Takazudo/zudo-bus/footprints/3dshapes/CAP-SMD_BD6.3-L6.6-W6.6-LS7.3-FD.step

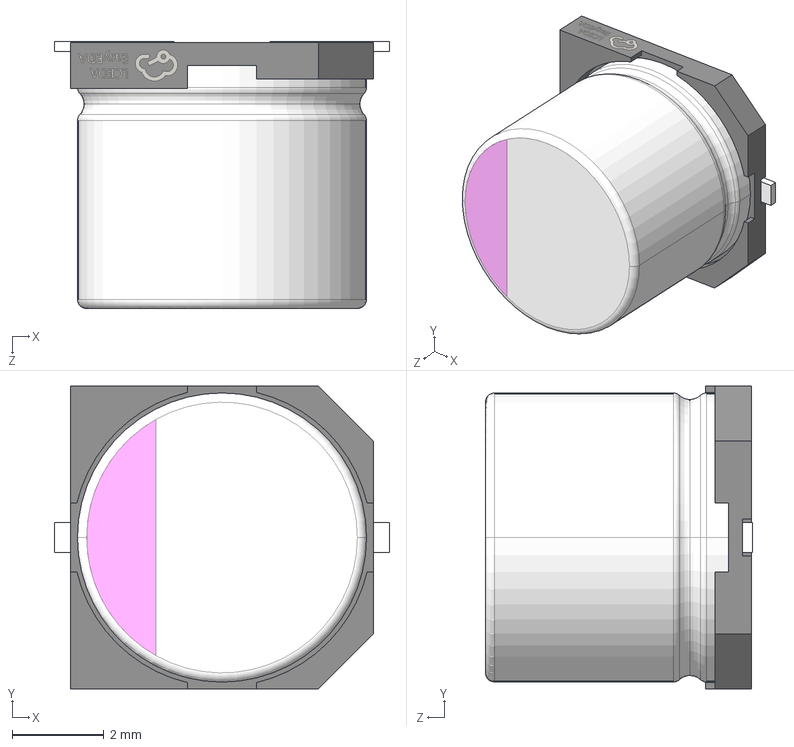
[picture p15: CAD file, 2026-02-04]
footprints/3dshapes/CAP-SMD_BD6.3-L6.6-W6.6-LS7.3-FD.step
7.30 x 6.60 x 5.82 mm
