Takazudo/zudo-bus/footprints/3dshapes/F1206_L3.2-W1.7-H0.6.step

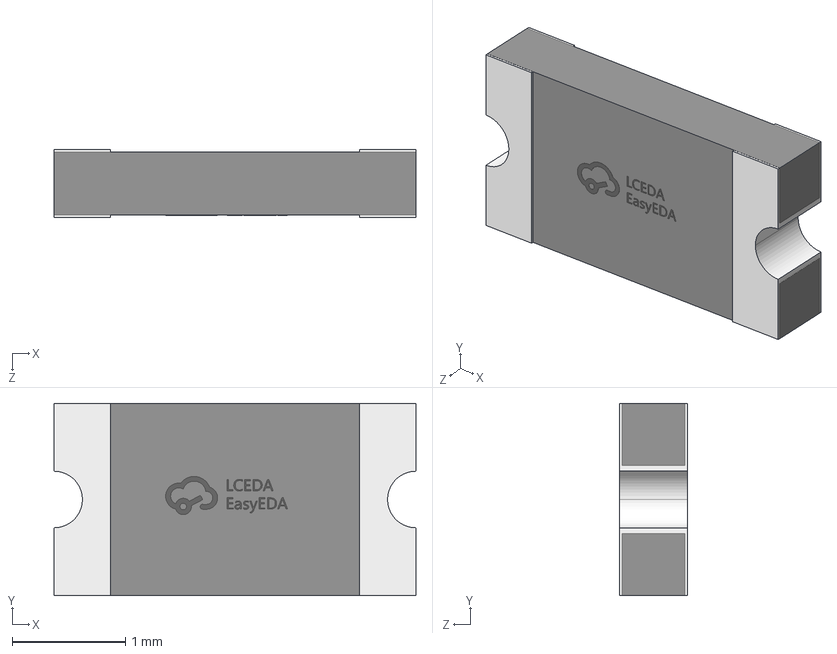
[picture p16: CAD file, 2026-02-04]
footprints/3dshapes/F1206_L3.2-W1.7-H0.6.step
3.20 x 1.70 x 0.6 mm
