Takazudo/zudo-bus/footprints/3dshapes/QFN-20_L3.0-W3.0-P0.40-BL-EP1.7.step

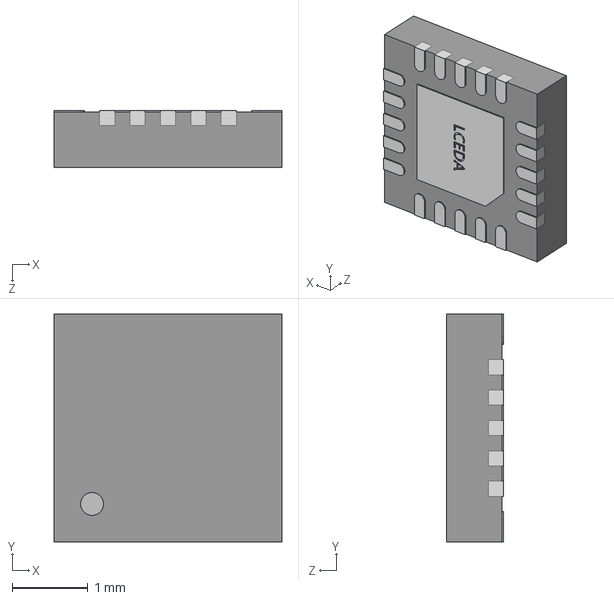
[picture p17: CAD file, 2026-02-04]
footprints/3dshapes/QFN-20_L3.0-W3.0-P0.40-BL-EP1.7.step
3.00 x 3.00 x 0.75 mm
