Takazudo/zudo-bus/footprints/3dshapes/F1812_L4.5-W3.2-H1.0.step

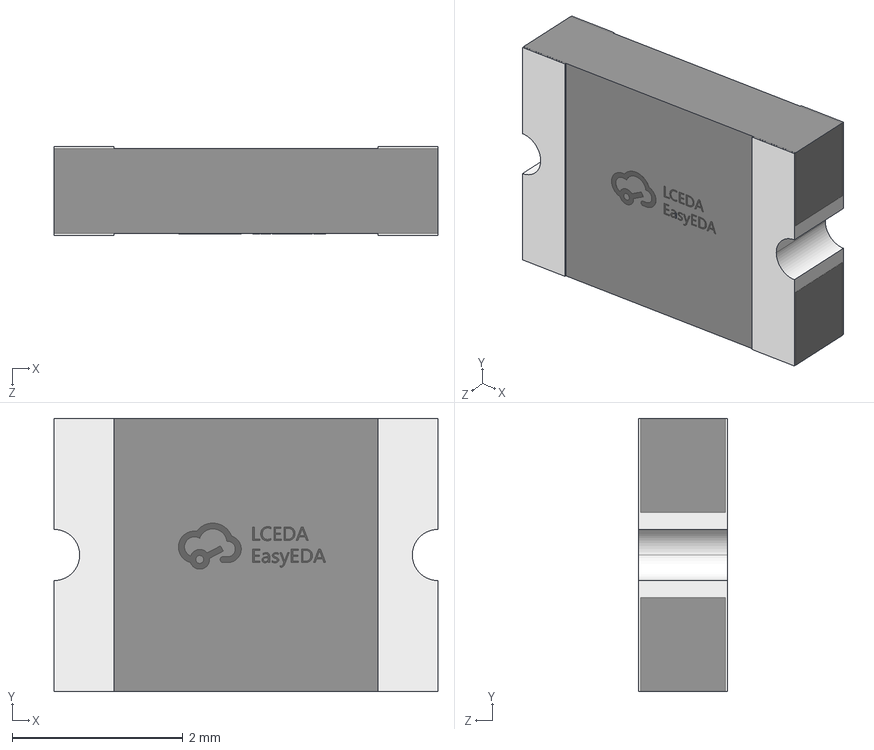
[picture p18: CAD file, 2026-02-04]
footprints/3dshapes/F1812_L4.5-W3.2-H1.0.step
4.50 x 3.20 x 1.04 mm
