Takazudo/zudo-bus/footprints/3dshapes/CAP-SMD_BD10.0-L10.3-W10.3-H10.2.step

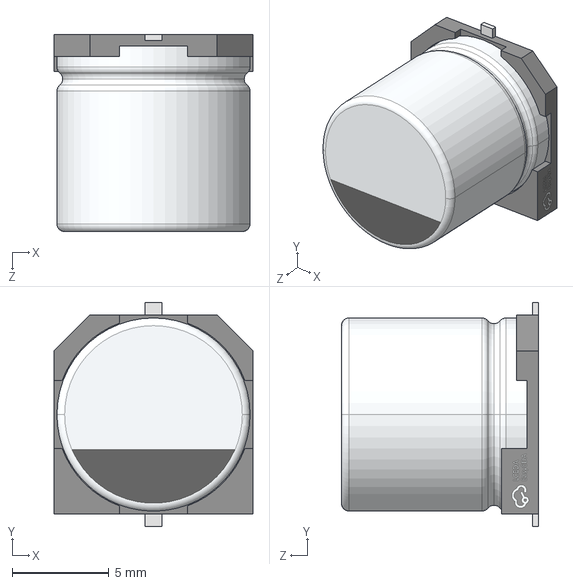
[picture p19: CAD file, 2026-02-04]
footprints/3dshapes/CAP-SMD_BD10.0-L10.3-W10.3-H10.2.step
10.3 x 11.6 x 10.2 mm
