Takazudo/zudo-bus/footprints/3dshapes/DC-IN-TH_DC550250-0366-2H.step

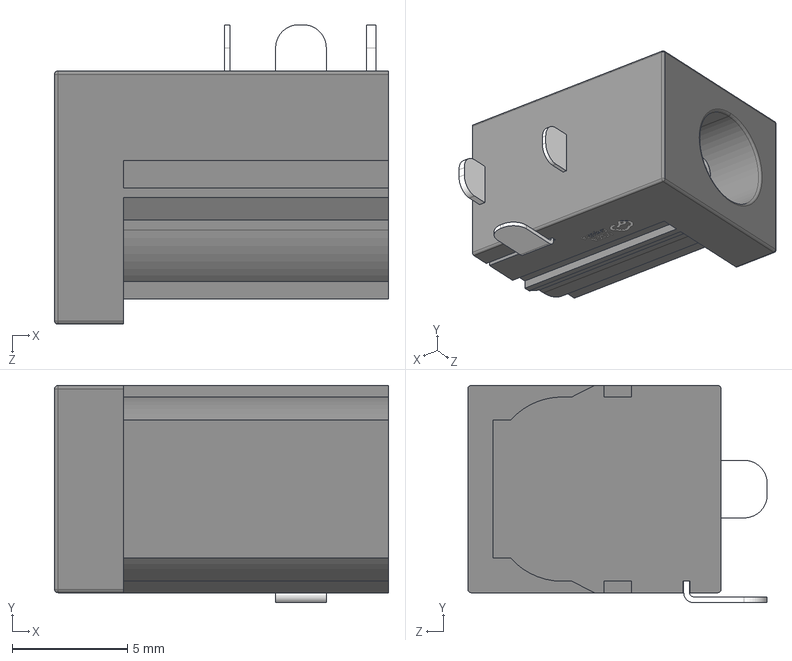
[picture p20: CAD file, 2026-02-04]
footprints/3dshapes/DC-IN-TH_DC550250-0366-2H.step
14.5 x 9.43 x 13.0 mm
