Takazudo/zudo-bus/footprints/3dshapes/CAP-SMD_BD6.3-L6.6-W6.6-FD.step

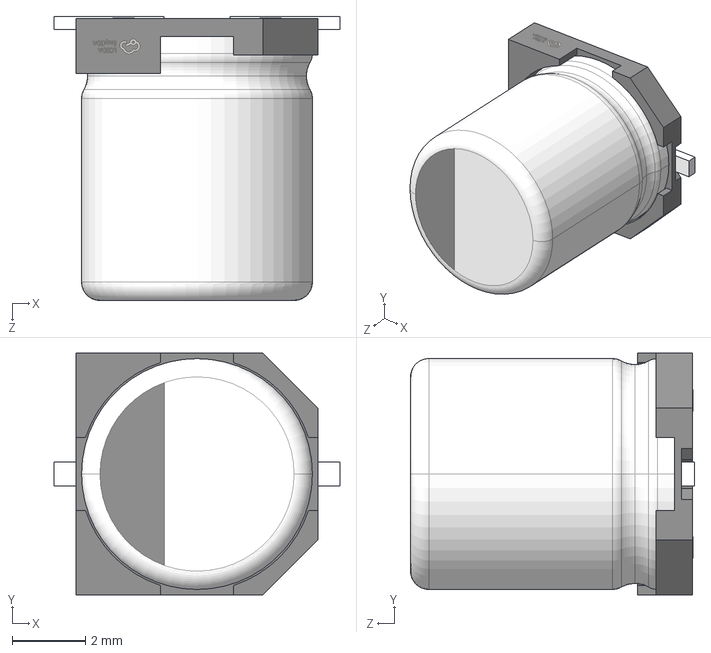
[picture p21: CAD file, 2026-02-04]
footprints/3dshapes/CAP-SMD_BD6.3-L6.6-W6.6-FD.step
7.80 x 6.60 x 7.75 mm
