Takazudo/zudo-bus/footprints/3dshapes/HDR-TH_16P-P2.54-M-WI-2X8P.step

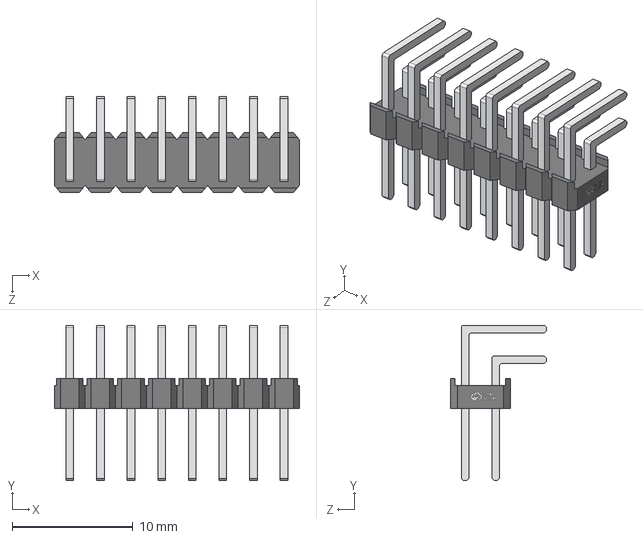
[picture p22: CAD file, 2026-02-04]
footprints/3dshapes/HDR-TH_16P-P2.54-M-WI-2X8P.step
20.3 x 12.9 x 8.00 mm
