Takazudo/zudo-bus/footprints/3dshapes/HDR-M-2.54_1x3.step

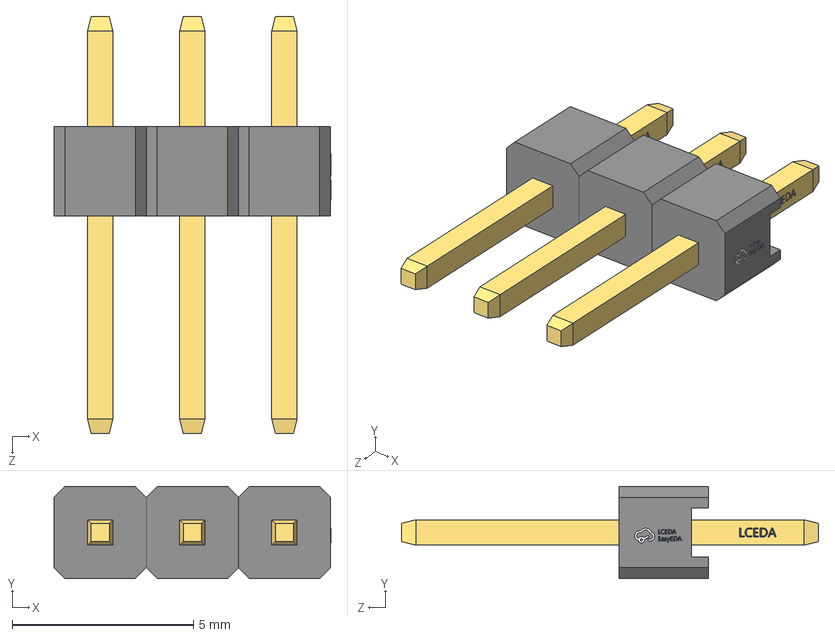
[picture p23: CAD file, 2026-02-04]
footprints/3dshapes/HDR-M-2.54_1x3.step
7.63 x 2.54 x 11.5 mm
