Takazudo/zudo-bus/footprints/3dshapes/R0805_L2.0-W1.3-H0.6.step

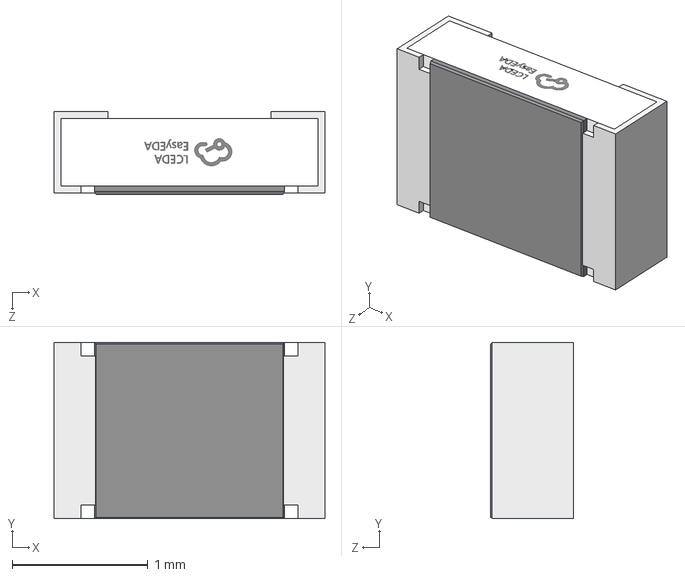
[picture p24: CAD file, 2026-02-04]
footprints/3dshapes/R0805_L2.0-W1.3-H0.6.step
2.00 x 1.30 x 0.61 mm
