Takazudo/zudo-bus/footprints/3dshapes/HDR-SMD_8P-P2.54-V-M-LS4.8_R2.step

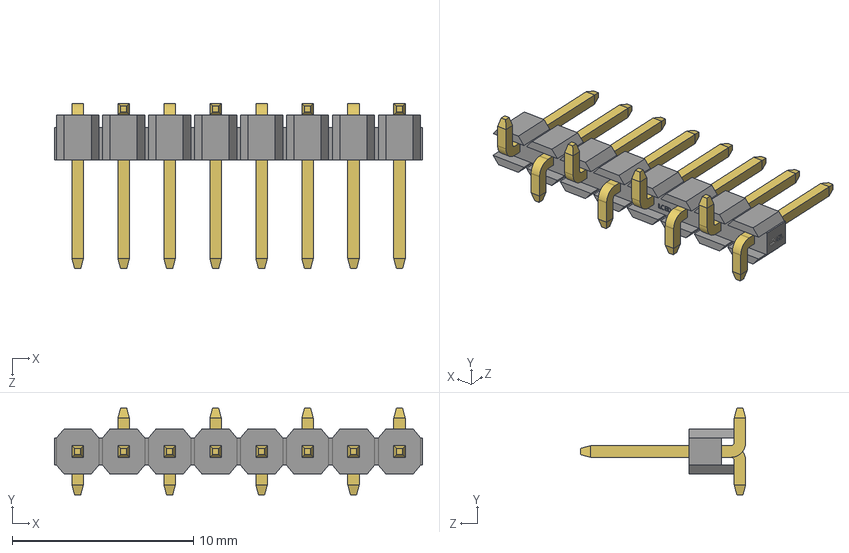
[picture p25: CAD file, 2026-02-04]
footprints/3dshapes/HDR-SMD_8P-P2.54-V-M-LS4.8_R2.step
20.3 x 4.80 x 9.14 mm
