Takazudo/zudo-bus/footprints/3dshapes/DO-214AC_L4.3-W2.7-LS5.0-RD.step

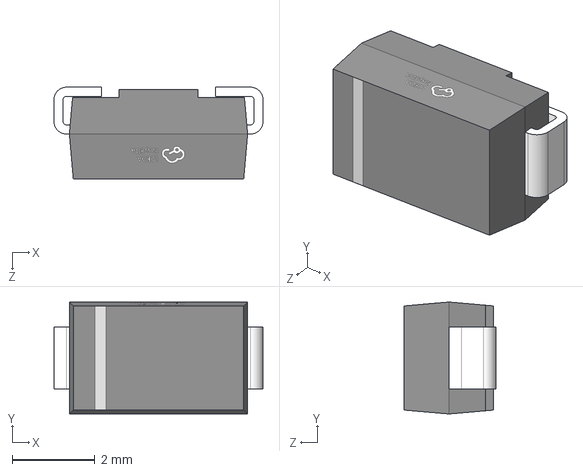
[picture p26: CAD file, 2026-02-04]
footprints/3dshapes/DO-214AC_L4.3-W2.7-LS5.0-RD.step
5.04 x 2.70 x 2.21 mm
