Takazudo/zudo-bus/footprints/3dshapes/TO-263-3_L10.2-W8.7-H4.5-LS14.4-P2.54.step

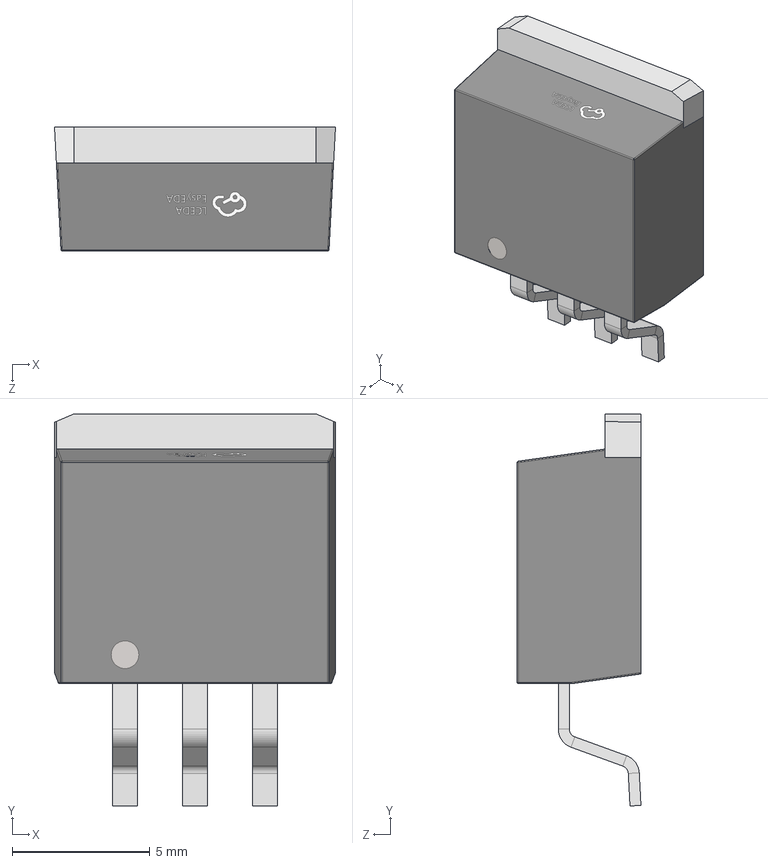
[picture p27: CAD file, 2026-02-04]
footprints/3dshapes/TO-263-3_L10.2-W8.7-H4.5-LS14.4-P2.54.step
10.2 x 14.2 x 4.50 mm
