Takazudo/zudo-bus/footprints/3dshapes/HDR-SMD_36P-P2.00-V-M_XBK_R2.step

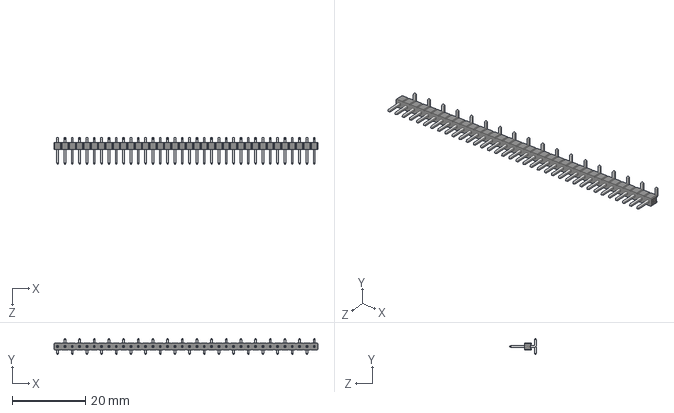
[picture p28: CAD file, 2026-02-04]
footprints/3dshapes/HDR-SMD_36P-P2.00-V-M_XBK_R2.step
72.0 x 4.40 x 7.25 mm
