Takazudo/zudo-bus/footprints/3dshapes/C0603_L1.6-W0.8-H0.8.step

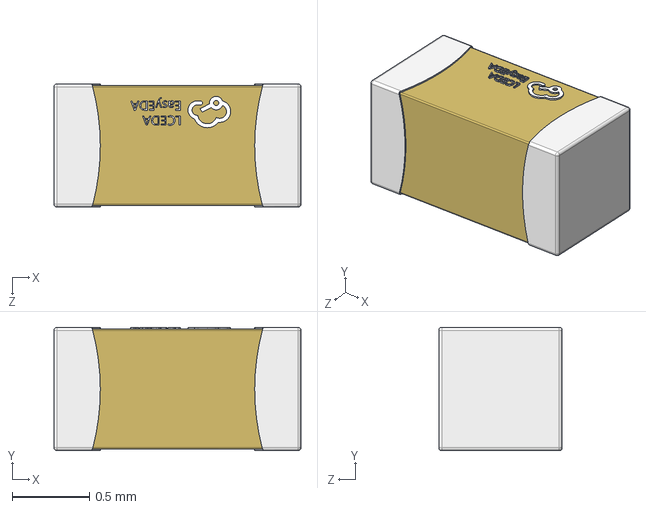
[picture p29: CAD file, 2026-02-04]
footprints/3dshapes/C0603_L1.6-W0.8-H0.8.step
1.60 x 0.8 x 0.8 mm
