Takazudo/zudo-bus/footprints/3dshapes/C1206_L3.2-W1.6-H1.3.step

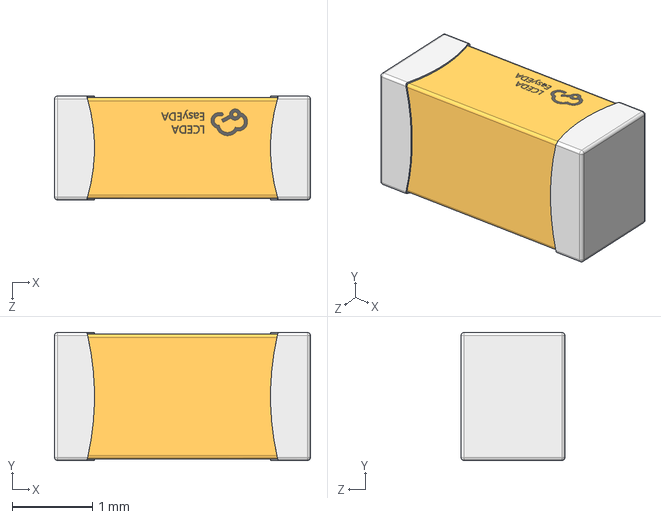
[picture p30: CAD file, 2026-02-04]
footprints/3dshapes/C1206_L3.2-W1.6-H1.3.step
3.20 x 1.60 x 1.30 mm
