Takazudo/zudo-bus/footprints/3dshapes/SMA_L4.4-W2.8-LS5.4-RD.step

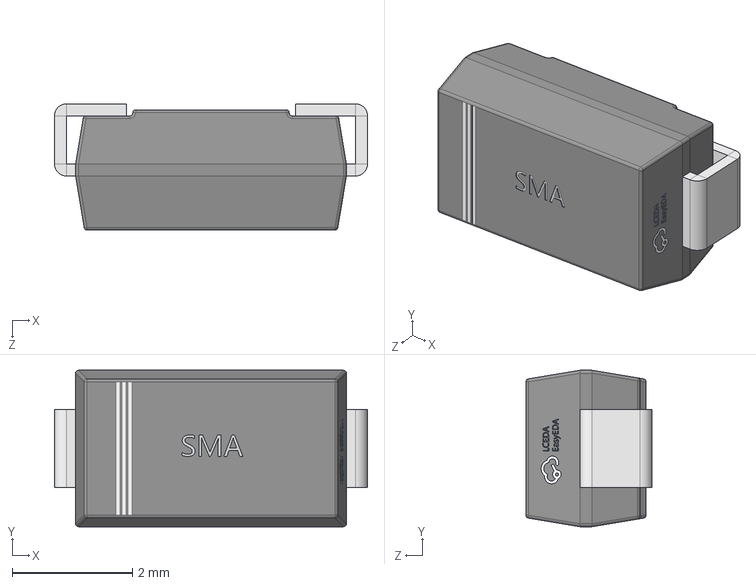
[picture p31: CAD file, 2026-02-04]
footprints/3dshapes/SMA_L4.4-W2.8-LS5.4-RD.step
5.20 x 2.60 x 2.10 mm
