Takazudo/zudo-bus/footprints/3dshapes/FUSE-SMD_L10.1-W3.1-H3.1.step

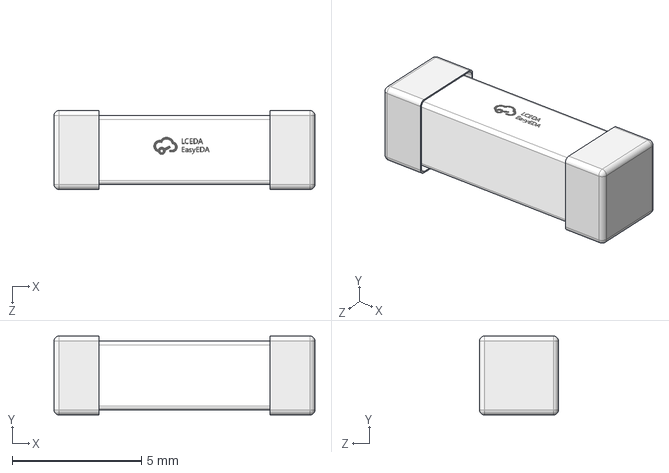
[picture p33: CAD file, 2026-02-04]
footprints/3dshapes/FUSE-SMD_L10.1-W3.1-H3.1.step
10.1 x 3.05 x 3.05 mm
