Takazudo/zudo-bus/footprints/3dshapes/SOD-123FL_L2.8-W1.8-LS3.7-RD.step

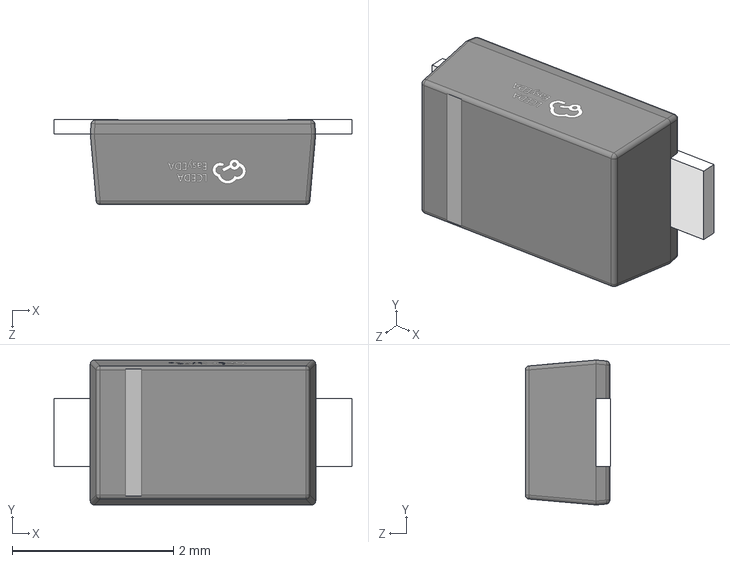
[picture p34: CAD file, 2026-02-04]
footprints/3dshapes/SOD-123FL_L2.8-W1.8-LS3.7-RD.step
3.70 x 1.80 x 1.06 mm
