Takazudo/zudo-bus/footprints/3dshapes/LED0805-RD.step

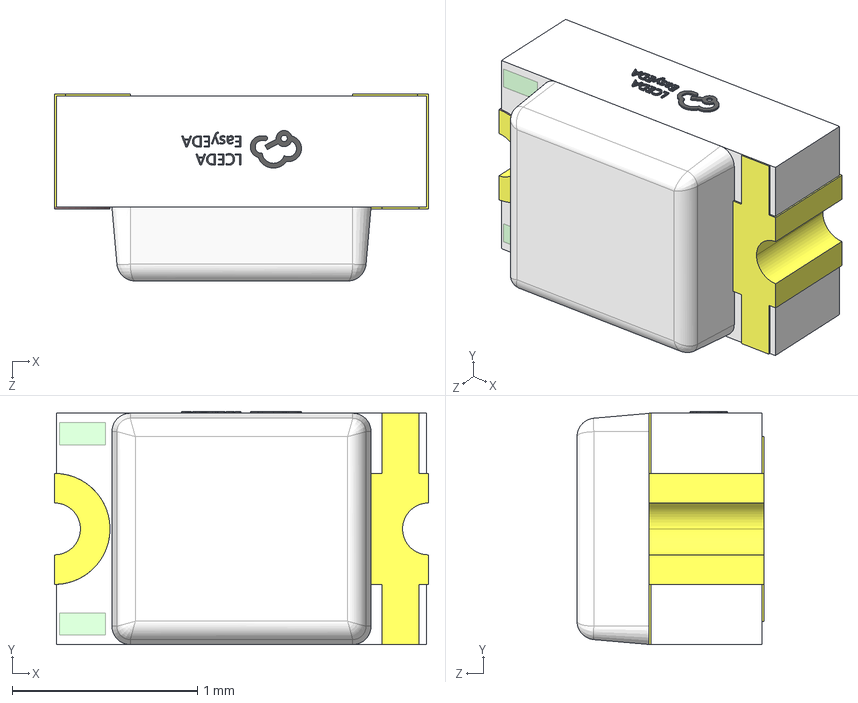
[picture p35: CAD file, 2026-02-04]
footprints/3dshapes/LED0805-RD.step
2.02 x 1.26 x 1.01 mm
