Takazudo/zudo-bus/footprints/3dshapes/HDR-TH_3P-P2.54-M-LI-1X3P.step

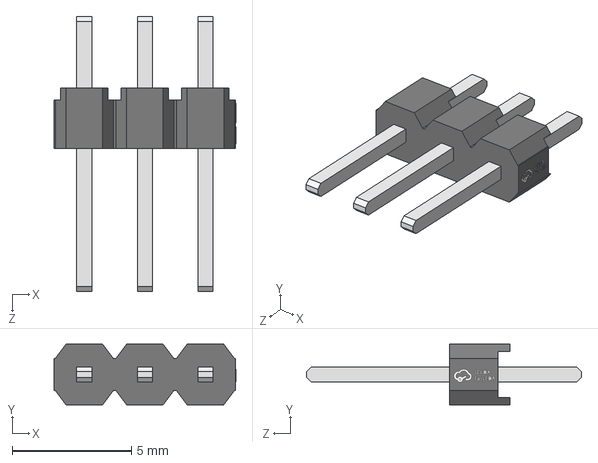
[picture p36: CAD file, 2026-02-04]
footprints/3dshapes/HDR-TH_3P-P2.54-M-LI-1X3P.step
7.63 x 2.54 x 11.5 mm
