Takazudo/zudo-bus/footprints/3dshapes/R0603.step

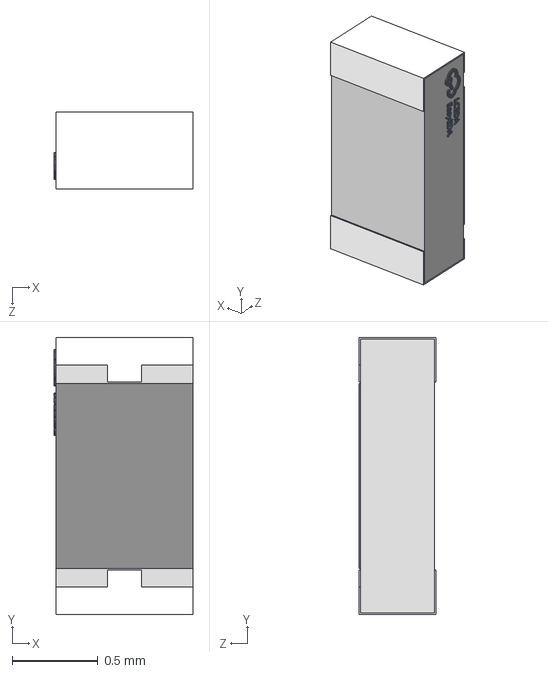
[picture p37: CAD file, 2026-02-04]
footprints/3dshapes/R0603.step
0.81 x 1.62 x 0.45 mm
