Takazudo/zudo-bus/footprints/3dshapes/CAP-SMD_BD18.0-L19.0-W19.0-LS20.4-FD.step

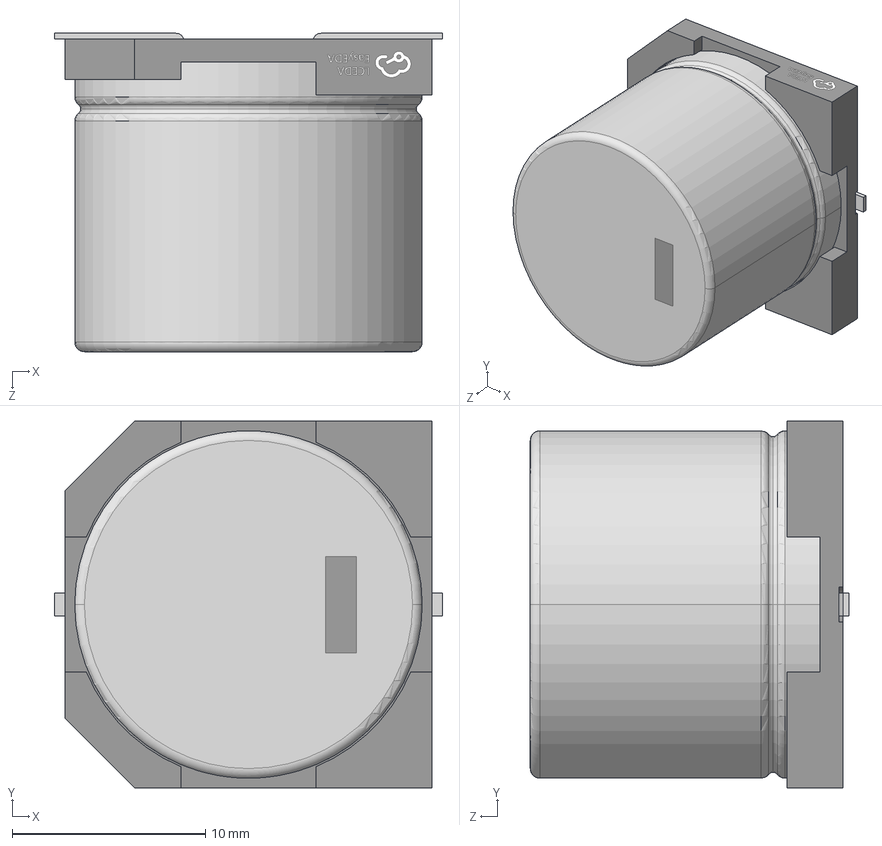
[picture p38: CAD file, 2026-02-04]
footprints/3dshapes/CAP-SMD_BD18.0-L19.0-W19.0-LS20.4-FD.step
20.1 x 19.0 x 16.5 mm
