Takazudo/zudo-bus/footprints/3dshapes/TO-263-2_L10.2-W8.7-H4.5-LS15.2-P2.54.step

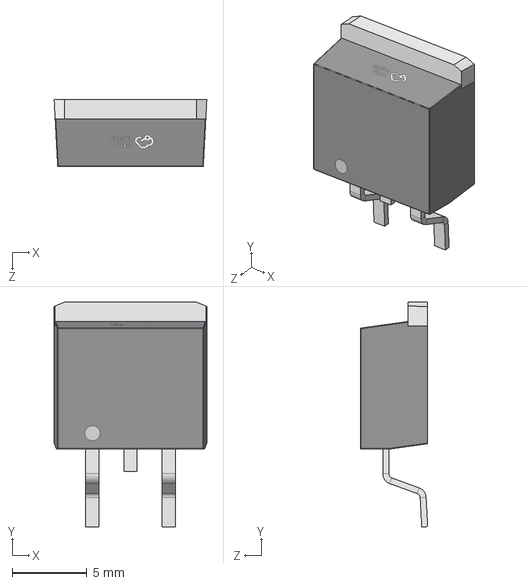
[picture p39: CAD file, 2026-02-04]
footprints/3dshapes/TO-263-2_L10.2-W8.7-H4.5-LS15.2-P2.54.step
10.2 x 15.0 x 4.50 mm
