Takazudo/zudo-bus/footprints/3dshapes/LED0603-R-RD_WHITE.step

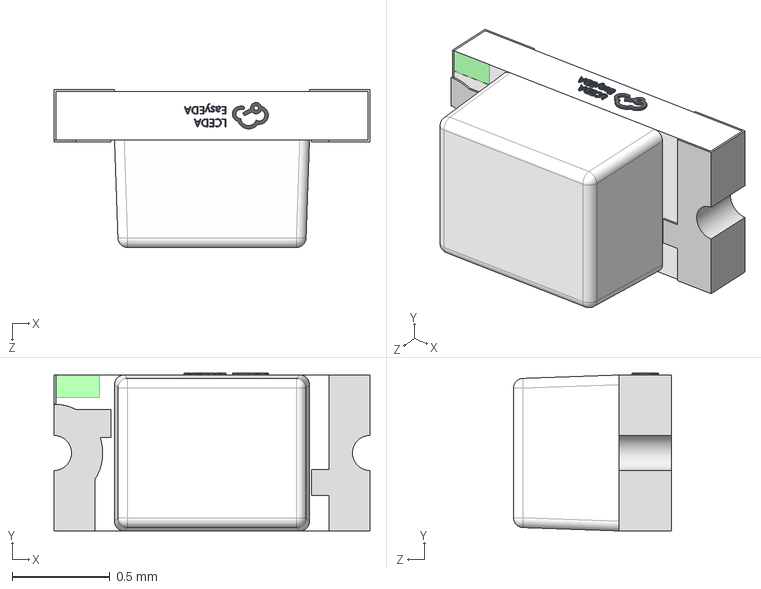
[picture p40: CAD file, 2026-02-04]
footprints/3dshapes/LED0603-R-RD_WHITE.step
1.62 x 0.81 x 0.81 mm
