Takazudo/zudo-bus/footprints/3dshapes/F1210_L3.2-W2.6-H0.6.step

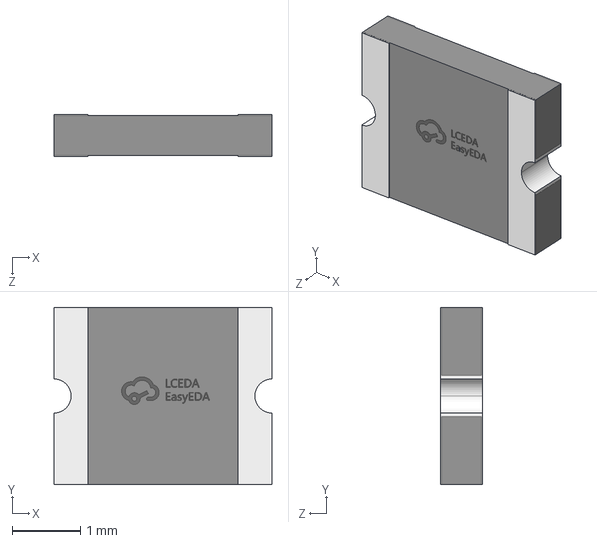
[picture p41: CAD file, 2026-02-04]
footprints/3dshapes/F1210_L3.2-W2.6-H0.6.step
3.20 x 2.60 x 0.62 mm
