Takazudo/zudo-bus/footprints/3dshapes/CONN-TH_2P-P5.00_WJ500V-5.08-2P.step

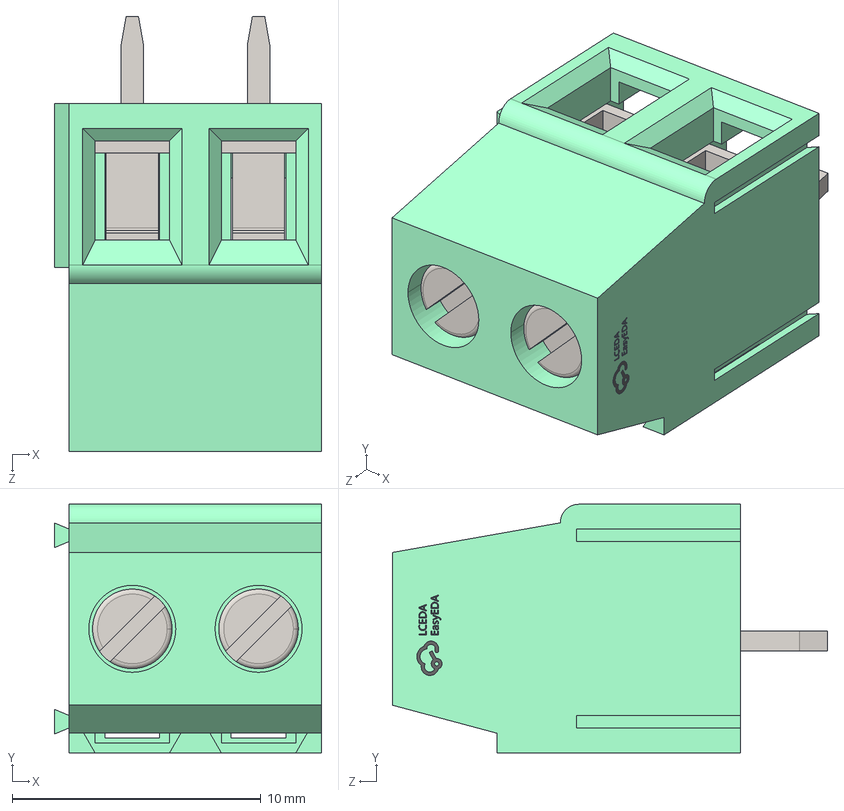
[picture p42: CAD file, 2026-02-04]
footprints/3dshapes/CONN-TH_2P-P5.00_WJ500V-5.08-2P.step
10.8 x 10.0 x 17.5 mm
