Takazudo/zudo-bus/footprints/3dshapes/CONN-TH_1217754-1.step

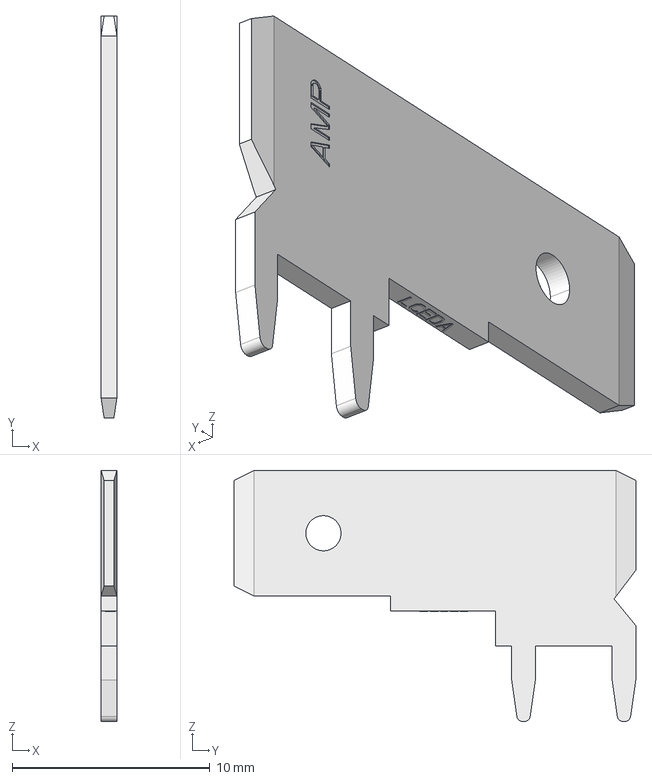
[picture p43: CAD file, 2026-02-04]
footprints/3dshapes/CONN-TH_1217754-1.step
0.8 x 20.3 x 12.7 mm
