Takazudo/zudo-bus/footprints/3dshapes/FUSE-SMD_L6.1-W2.6-H2.6.step

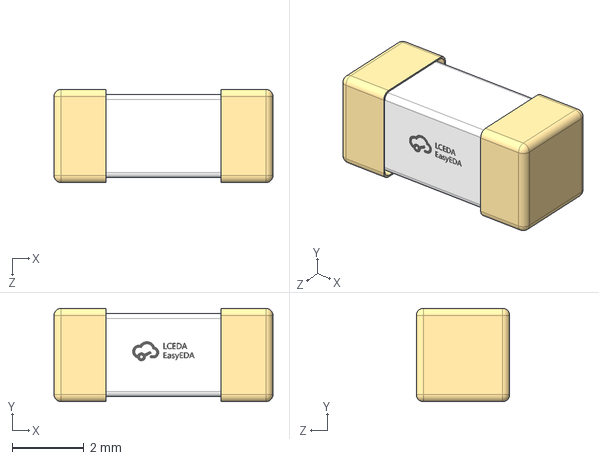
[picture p44: CAD file, 2026-02-04]
footprints/3dshapes/FUSE-SMD_L6.1-W2.6-H2.6.step
6.10 x 2.60 x 2.60 mm
