Takazudo/zudo-bus/footprints/3dshapes/SOD-123_L2.8-W1.8-LS3.7-BI.step

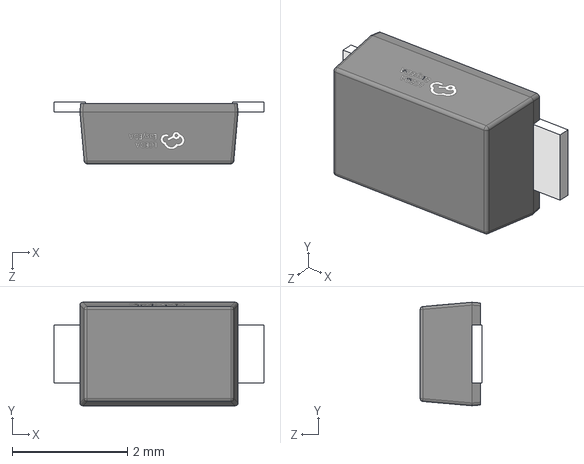
[picture p45: CAD file, 2026-02-04]
footprints/3dshapes/SOD-123_L2.8-W1.8-LS3.7-BI.step
3.65 x 1.80 x 1.07 mm
