Takazudo/zudo-bus/footprints/3dshapes/SOD-323_L1.7-W1.3-H1.1-LS2.5.step

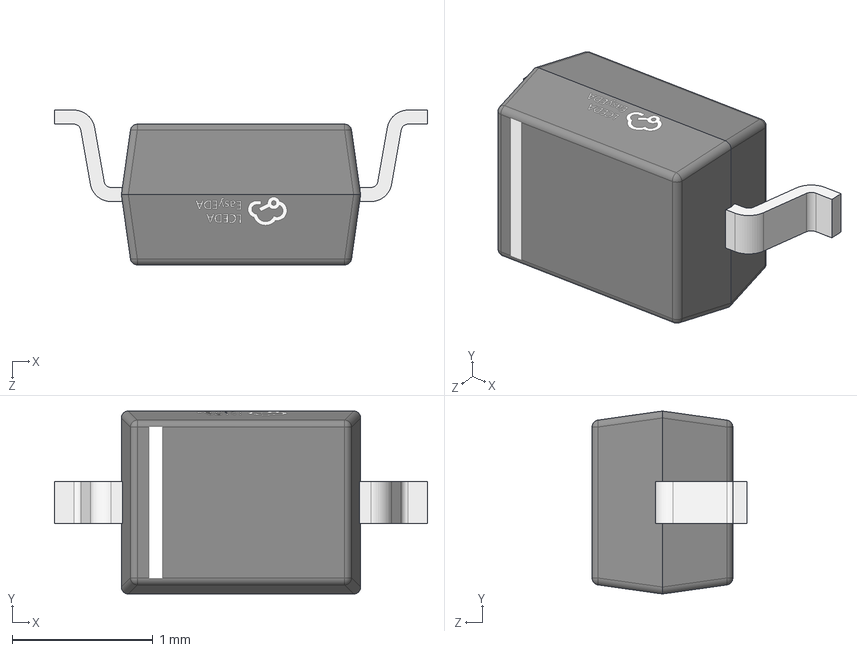
[picture p46: CAD file, 2026-02-04]
footprints/3dshapes/SOD-323_L1.7-W1.3-H1.1-LS2.5.step
2.65 x 1.30 x 1.10 mm
