Takazudo/zudo-bus/footprints/3dshapes/CAP-SMD_L4.3-W4.3-H5.3-LS5.1.step

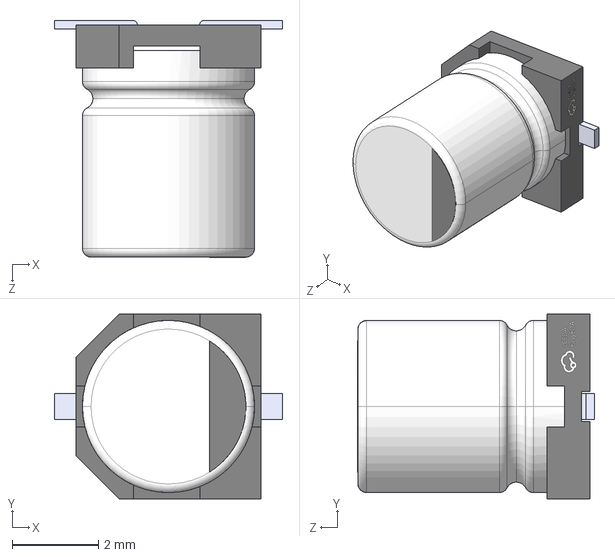
[picture p47: CAD file, 2026-02-04]
footprints/3dshapes/CAP-SMD_L4.3-W4.3-H5.3-LS5.1.step
5.30 x 4.30 x 5.51 mm
