Takazudo/zudo-bus/footprints/3dshapes/D-FLAT_L4.3-W2.6-LS5.3-RD.step

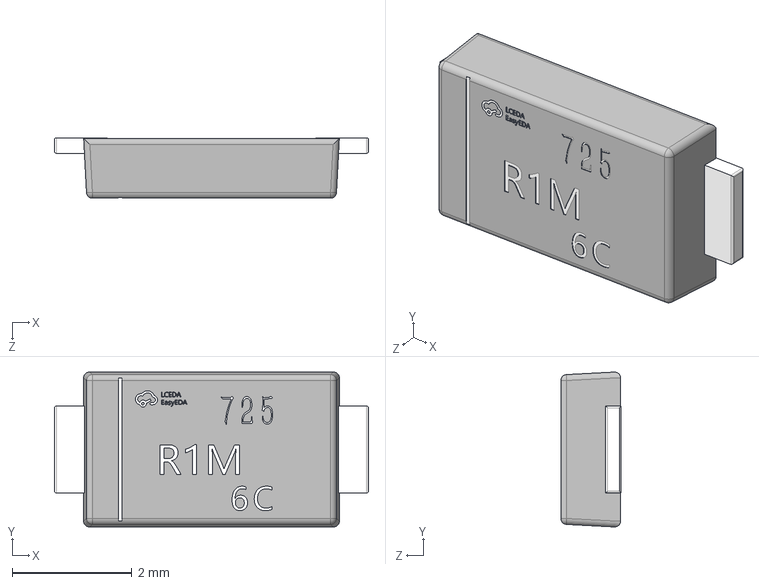
[picture p48: CAD file, 2026-02-04]
footprints/3dshapes/D-FLAT_L4.3-W2.6-LS5.3-RD.step
5.25 x 2.59 x 1.01 mm
