Takazudo/zudo-bus/footprints/3dshapes/TO-252-3_L6.5-W5.8-P4.58-BL.step

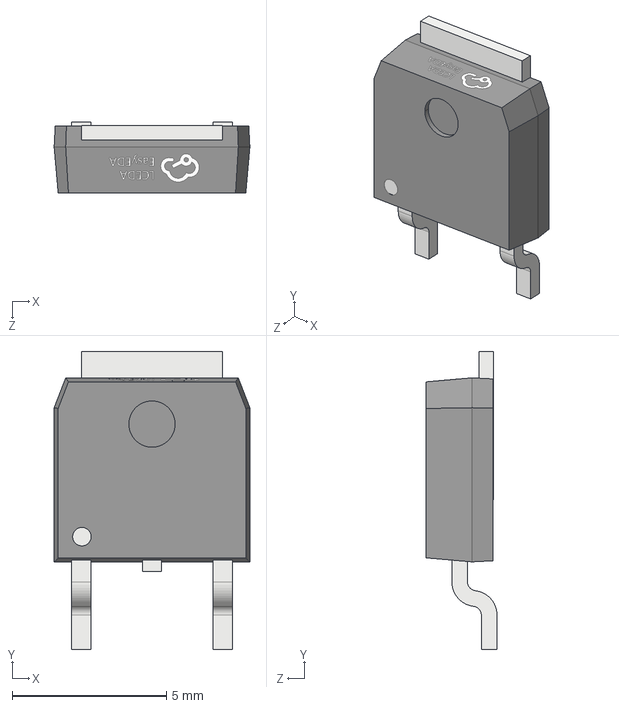
[picture p49: CAD file, 2026-02-04]
footprints/3dshapes/TO-252-3_L6.5-W5.8-P4.58-BL.step
6.35 x 9.67 x 2.31 mm
