Takazudo/zudo-bus/footprints/3dshapes/CAP-SMD_BD6.3-L6.6-W6.6-LS7.3-FD_H7.7.step

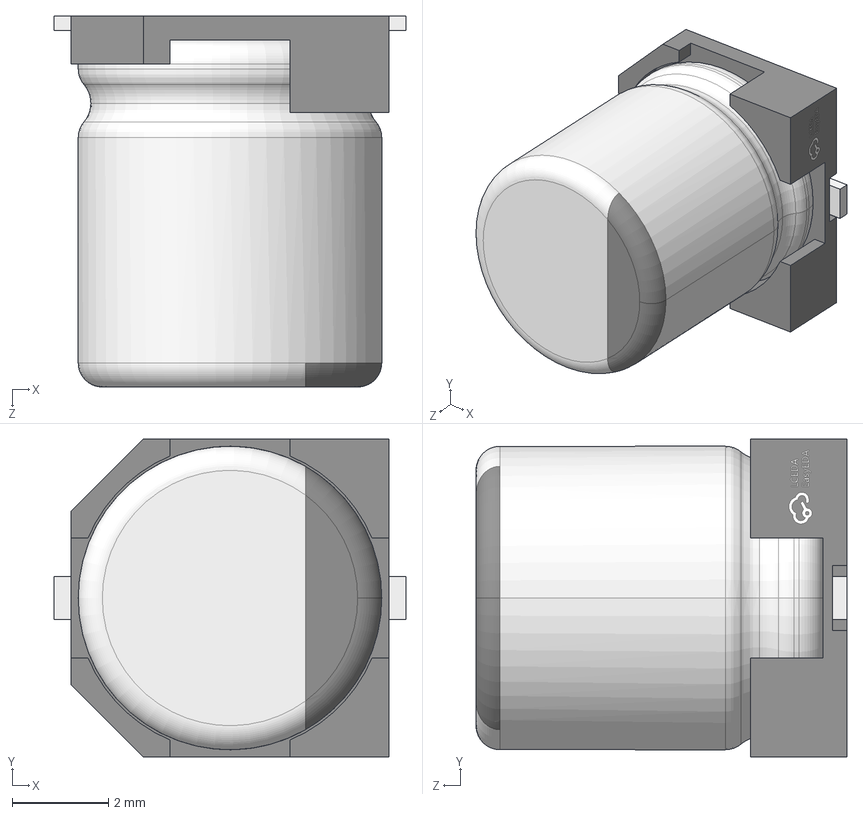
[picture p50: CAD file, 2026-02-04]
footprints/3dshapes/CAP-SMD_BD6.3-L6.6-W6.6-LS7.3-FD_H7.7.step
7.30 x 6.60 x 7.70 mm
