Takazudo/zudo-bus/doc/pnpm-lock.yaml

lockfileVersion: '9.0'

settings:
  autoInstallPeers: true
  excludeLinksFromLockfile: false

importers:

  .:
    dependencies:
      '@docusaurus/core':
        specifier: 3.9.2
        version: 3.9.2(@mdx-js/react@3.1.1(@types/react@19.2.8)(react@19.2.3))(react-dom@19.2.3(react@19.2.3))(react@19.2.3)(typescript@5.9.3)
      '@docusaurus/plugin-content-docs':
        specifier: 3.9.2
        version: 3.9.2(@mdx-js/react@3.1.1(@types/react@19.2.8)(react@19.2.3))(react-dom@19.2.3(react@19.2.3))(react@19.2.3)(typescript@5.9.3)
      '@docusaurus/preset-classic':
        specifier: 3.9.2
        version: 3.9.2(@algolia/client-search@5.46.2)(@mdx-js/react@3.1.1(@types/react@19.2.8)(react@19.2.3))(@types/react@19.2.8)(react-dom@19.2.3(react@19.2.3))(react@19.2.3)(search-insights@2.17.3)(typescript@5.9.3)
      '@docusaurus/theme-common':
        specifier: 3.9.2
        version: 3.9.2(@docusaurus/plugin-content-docs@3.9.2(@mdx-js/react@3.1.1(@types/react@19.2.8)(react@19.2.3))(react-dom@19.2.3(react@19.2.3))(react@19.2.3)(typescript@5.9.3))(react-dom@19.2.3(react@19.2.3))(react@19.2.3)
      '@docusaurus/theme-mermaid':
        specifier: ^3.9.2
        version: 3.9.2(@docusaurus/plugin-content-docs@3.9.2(@mdx-js/react@3.1.1(@types/react@19.2.8)(react@19.2.3))(react-dom@19.2.3(react@19.2.3))(react@19.2.3)(typescript@5.9.3))(@mdx-js/react@3.1.1(@types/react@19.2.8)(react@19.2.3))(react-dom@19.2.3(react@19.2.3))(react@19.2.3)(typescript@5.9.3)
      '@mdx-js/react':
        specifier: ^3.1.1
        version: 3.1.1(@types/react@19.2.8)(react@19.2.3)
      clsx:
        specifier: ^2.1.1
        version: 2.1.1
      prism-react-renderer:
        specifier: ^2.4.1
        version: 2.4.1(react@19.2.3)
      react:
        specifier: ^19.2.3
        version: 19.2.3
      react-dom:
        specifier: ^19.2.3
        version: 19.2.3(react@19.2.3)
    devDependencies:
      '@docusaurus/module-type-aliases':
        specifier: 3.9.2
        version: 3.9.2(react-dom@19.2.3(react@19.2.3))(react@19.2.3)
      '@docusaurus/types':
        specifier: 3.9.2
        version: 3.9.2(react-dom@19.2.3(react@19.2.3))(react@19.2.3)
      '@eslint/js':
        specifier: ^9.39.2
        version: 9.39.2
      '@types/react':
        specifier: ^19.2.7
        version: 19.2.8
      '@types/react-dom':
        specifier: ^19.2.3
        version: 19.2.3(@types/react@19.2.8)
      '@typescript-eslint/eslint-plugin':
        specifier: ^8.51.0
        version: 8.52.0(@typescript-eslint/parser@8.52.0(eslint@9.39.2(jiti@1.21.7))(typescript@5.9.3))(eslint@9.39.2(jiti@1.21.7))(typescript@5.9.3)
      '@typescript-eslint/parser':
        specifier: ^8.51.0
        version: 8.52.0(eslint@9.39.2(jiti@1.21.7))(typescript@5.9.3)
      eslint:
        specifier: ^9.39.2
        version: 9.39.2(jiti@1.21.7)
      eslint-config-prettier:
        specifier: ^10.1.8
        version: 10.1.8(eslint@9.39.2(jiti@1.21.7))
      eslint-plugin-prettier:
        specifier: ^5.5.4
        version: 5.5.4(@types/eslint@9.6.1)(eslint-config-prettier@10.1.8(eslint@9.39.2(jiti@1.21.7)))(eslint@9.39.2(jiti@1.21.7))(prettier@3.7.4)
      eslint-plugin-react:
        specifier: ^7.37.5
        version: 7.37.5(eslint@9.39.2(jiti@1.21.7))
      eslint-plugin-react-hooks:
        specifier: ^5.2.0
        version: 5.2.0(eslint@9.39.2(jiti@1.21.7))
      globals:
        specifier: ^16.5.0
        version: 16.5.0
      gray-matter:
        specifier: ^4.0.3
        version: 4.0.3
      husky:
        specifier: ^9.1.7
        version: 9.1.7
      lint-staged:
        specifier: ^16.2.7
        version: 16.2.7
      prettier:
        specifier: ^3.7.4
        version: 3.7.4
      typescript:
        specifier: ^5.9.3
        version: 5.9.3

packages:

  '@ai-sdk/gateway@2.0.25':
    resolution: {integrity: sha512-Rq+FX55ne7lMiqai7NcvvDZj4HLsr+hg77WayqmySqc6zhw3tIOLxd4Ty6OpwNj0C0bVMi3iCl2zvJIEirh9XA==}
    engines: {node: '>=18'}
    peerDependencies:
      zod: ^3.25.76 || ^4.1.8

  '@ai-sdk/provider-utils@3.0.20':
    resolution: {integrity: sha512-iXHVe0apM2zUEzauqJwqmpC37A5rihrStAih5Ks+JE32iTe4LZ58y17UGBjpQQTCRw9YxMeo2UFLxLpBluyvLQ==}
    engines: {node: '>=18'}
    peerDependencies:
      zod: ^3.25.76 || ^4.1.8

  '@ai-sdk/provider@2.0.1':
    resolution: {integrity: sha512-KCUwswvsC5VsW2PWFqF8eJgSCu5Ysj7m1TxiHTVA6g7k360bk0RNQENT8KTMAYEs+8fWPD3Uu4dEmzGHc+jGng==}
    engines: {node: '>=18'}

  '@ai-sdk/react@2.0.121':
    resolution: {integrity: sha512-VbckviE2ryPaWcecjGXP9zY4CJUqXYoLFfJZJl95XtZL4Gl8X0AuU2p7p6ModCoavHuFw1bfL8k6d0Mu59WROw==}
    engines: {node: '>=18'}
    peerDependencies:
      react: ^18 || ~19.0.1 || ~19.1.2 || ^19.2.1
      zod: ^3.25.76 || ^4.1.8
    peerDependenciesMeta:
      zod:
        optional: true

  '@algolia/abtesting@1.12.2':
    resolution: {integrity: sha512-oWknd6wpfNrmRcH0vzed3UPX0i17o4kYLM5OMITyMVM2xLgaRbIafoxL0e8mcrNNb0iORCJA0evnNDKRYth5WQ==}
    engines: {node: '>= 14.0.0'}

  '@algolia/autocomplete-core@1.19.2':
    resolution: {integrity: sha512-mKv7RyuAzXvwmq+0XRK8HqZXt9iZ5Kkm2huLjgn5JoCPtDy+oh9yxUMfDDaVCw0oyzZ1isdJBc7l9nuCyyR7Nw==}

  '@algolia/autocomplete-plugin-algolia-insights@1.19.2':
    resolution: {integrity: sha512-TjxbcC/r4vwmnZaPwrHtkXNeqvlpdyR+oR9Wi2XyfORkiGkLTVhX2j+O9SaCCINbKoDfc+c2PB8NjfOnz7+oKg==}
    peerDependencies:
      search-insights: '>= 1 < 3'

  '@algolia/autocomplete-shared@1.19.2':
    resolution: {integrity: sha512-jEazxZTVD2nLrC+wYlVHQgpBoBB5KPStrJxLzsIFl6Kqd1AlG9sIAGl39V5tECLpIQzB3Qa2T6ZPJ1ChkwMK/w==}
    peerDependencies:
      '@algolia/client-search': '>= 4.9.1 < 6'
      algoliasearch: '>= 4.9.1 < 6'

  '@algolia/client-abtesting@5.46.2':
    resolution: {integrity: sha512-oRSUHbylGIuxrlzdPA8FPJuwrLLRavOhAmFGgdAvMcX47XsyM+IOGa9tc7/K5SPvBqn4nhppOCEz7BrzOPWc4A==}
    engines: {node: '>= 14.0.0'}

  '@algolia/client-analytics@5.46.2':
    resolution: {integrity: sha512-EPBN2Oruw0maWOF4OgGPfioTvd+gmiNwx0HmD9IgmlS+l75DatcBkKOPNJN+0z3wBQWUO5oq602ATxIfmTQ8bA==}
    engines: {node: '>= 14.0.0'}

  '@algolia/client-common@5.46.2':
    resolution: {integrity: sha512-Hj8gswSJNKZ0oyd0wWissqyasm+wTz1oIsv5ZmLarzOZAp3vFEda8bpDQ8PUhO+DfkbiLyVnAxsPe4cGzWtqkg==}
    engines: {node: '>= 14.0.0'}

  '@algolia/client-insights@5.46.2':
    resolution: {integrity: sha512-6dBZko2jt8FmQcHCbmNLB0kCV079Mx/DJcySTL3wirgDBUH7xhY1pOuUTLMiGkqM5D8moVZTvTdRKZUJRkrwBA==}
    engines: {node: '>= 14.0.0'}

  '@algolia/client-personalization@5.46.2':
    resolution: {integrity: sha512-1waE2Uqh/PHNeDXGn/PM/WrmYOBiUGSVxAWqiJIj73jqPqvfzZgzdakHscIVaDl6Cp+j5dwjsZ5LCgaUr6DtmA==}
    engines: {node: '>= 14.0.0'}

  '@algolia/client-query-suggestions@5.46.2':
    resolution: {integrity: sha512-EgOzTZkyDcNL6DV0V/24+oBJ+hKo0wNgyrOX/mePBM9bc9huHxIY2352sXmoZ648JXXY2x//V1kropF/Spx83w==}
    engines: {node: '>= 14.0.0'}

  '@algolia/client-search@5.46.2':
    resolution: {integrity: sha512-ZsOJqu4HOG5BlvIFnMU0YKjQ9ZI6r3C31dg2jk5kMWPSdhJpYL9xa5hEe7aieE+707dXeMI4ej3diy6mXdZpgA==}
    engines: {node: '>= 14.0.0'}

  '@algolia/events@4.0.1':
    resolution: {integrity: sha512-FQzvOCgoFXAbf5Y6mYozw2aj5KCJoA3m4heImceldzPSMbdyS4atVjJzXKMsfX3wnZTFYwkkt8/z8UesLHlSBQ==}

  '@algolia/ingestion@1.46.2':
    resolution: {integrity: sha512-1Uw2OslTWiOFDtt83y0bGiErJYy5MizadV0nHnOoHFWMoDqWW0kQoMFI65pXqRSkVvit5zjXSLik2xMiyQJDWQ==}
    engines: {node: '>= 14.0.0'}

  '@algolia/monitoring@1.46.2':
    resolution: {integrity: sha512-xk9f+DPtNcddWN6E7n1hyNNsATBCHIqAvVGG2EAGHJc4AFYL18uM/kMTiOKXE/LKDPyy1JhIerrh9oYb7RBrgw==}
    engines: {node: '>= 14.0.0'}

  '@algolia/recommend@5.46.2':
    resolution: {integrity: sha512-NApbTPj9LxGzNw4dYnZmj2BoXiAc8NmbbH6qBNzQgXklGklt/xldTvu+FACN6ltFsTzoNU6j2mWNlHQTKGC5+Q==}
    engines: {node: '>= 14.0.0'}

  '@algolia/requester-browser-xhr@5.46.2':
    resolution: {integrity: sha512-ekotpCwpSp033DIIrsTpYlGUCF6momkgupRV/FA3m62SreTSZUKjgK6VTNyG7TtYfq9YFm/pnh65bATP/ZWJEg==}
    engines: {node: '>= 14.0.0'}

  '@algolia/requester-fetch@5.46.2':
    resolution: {integrity: sha512-gKE+ZFi/6y7saTr34wS0SqYFDcjHW4Wminv8PDZEi0/mE99+hSrbKgJWxo2ztb5eqGirQTgIh1AMVacGGWM1iw==}
    engines: {node: '>= 14.0.0'}

  '@algolia/requester-node-http@5.46.2':
    resolution: {integrity: sha512-ciPihkletp7ttweJ8Zt+GukSVLp2ANJHU+9ttiSxsJZThXc4Y2yJ8HGVWesW5jN1zrsZsezN71KrMx/iZsOYpg==}
    engines: {node: '>= 14.0.0'}

  '@antfu/install-pkg@1.1.0':
    resolution: {integrity: sha512-MGQsmw10ZyI+EJo45CdSER4zEb+p31LpDAFp2Z3gkSd1yqVZGi0Ebx++YTEMonJy4oChEMLsxZ64j8FH6sSqtQ==}

  '@babel/code-frame@7.27.1':
    resolution: {integrity: sha512-cjQ7ZlQ0Mv3b47hABuTevyTuYN4i+loJKGeV9flcCgIK37cCXRh+L1bd3iBHlynerhQ7BhCkn2BPbQUL+rGqFg==}
    engines: {node: '>=6.9.0'}

  '@babel/compat-data@7.28.5':
    resolution: {integrity: sha512-6uFXyCayocRbqhZOB+6XcuZbkMNimwfVGFji8CTZnCzOHVGvDqzvitu1re2AU5LROliz7eQPhB8CpAMvnx9EjA==}
    engines: {node: '>=6.9.0'}

  '@babel/core@7.28.5':
    resolution: {integrity: sha512-e7jT4DxYvIDLk1ZHmU/m/mB19rex9sv0c2ftBtjSBv+kVM/902eh0fINUzD7UwLLNR+jU585GxUJ8/EBfAM5fw==}
    engines: {node: '>=6.9.0'}

  '@babel/generator@7.28.5':
    resolution: {integrity: sha512-3EwLFhZ38J4VyIP6WNtt2kUdW9dokXA9Cr4IVIFHuCpZ3H8/YFOl5JjZHisrn1fATPBmKKqXzDFvh9fUwHz6CQ==}
    engines: {node: '>=6.9.0'}

  '@babel/helper-annotate-as-pure@7.27.3':
    resolution: {integrity: sha512-fXSwMQqitTGeHLBC08Eq5yXz2m37E4pJX1qAU1+2cNedz/ifv/bVXft90VeSav5nFO61EcNgwr0aJxbyPaWBPg==}
    engines: {node: '>=6.9.0'}

  '@babel/helper-compilation-targets@7.27.2':
    resolution: {integrity: sha512-2+1thGUUWWjLTYTHZWK1n8Yga0ijBz1XAhUXcKy81rd5g6yh7hGqMp45v7cadSbEHc9G3OTv45SyneRN3ps4DQ==}
    engines: {node: '>=6.9.0'}

  '@babel/helper-create-class-features-plugin@7.28.5':
    resolution: {integrity: sha512-q3WC4JfdODypvxArsJQROfupPBq9+lMwjKq7C33GhbFYJsufD0yd/ziwD+hJucLeWsnFPWZjsU2DNFqBPE7jwQ==}
    engines: {node: '>=6.9.0'}
    peerDependencies:
      '@babel/core': ^7.0.0

  '@babel/helper-create-regexp-features-plugin@7.28.5':
    resolution: {integrity: sha512-N1EhvLtHzOvj7QQOUCCS3NrPJP8c5W6ZXCHDn7Yialuy1iu4r5EmIYkXlKNqT99Ciw+W0mDqWoR6HWMZlFP3hw==}
    engines: {node: '>=6.9.0'}
    peerDependencies:
      '@babel/core': ^7.0.0

  '@babel/helper-define-polyfill-provider@0.6.5':
    resolution: {integrity: sha512-uJnGFcPsWQK8fvjgGP5LZUZZsYGIoPeRjSF5PGwrelYgq7Q15/Ft9NGFp1zglwgIv//W0uG4BevRuSJRyylZPg==}
    peerDependencies:
      '@babel/core': ^7.4.0 || ^8.0.0-0 <8.0.0

  '@babel/helper-globals@7.28.0':
    resolution: {integrity: sha512-+W6cISkXFa1jXsDEdYA8HeevQT/FULhxzR99pxphltZcVaugps53THCeiWA8SguxxpSp3gKPiuYfSWopkLQ4hw==}
    engines: {node: '>=6.9.0'}

  '@babel/helper-member-expression-to-functions@7.28.5':
    resolution: {integrity: sha512-cwM7SBRZcPCLgl8a7cY0soT1SptSzAlMH39vwiRpOQkJlh53r5hdHwLSCZpQdVLT39sZt+CRpNwYG4Y2v77atg==}
    engines: {node: '>=6.9.0'}

  '@babel/helper-module-imports@7.27.1':
    resolution: {integrity: sha512-0gSFWUPNXNopqtIPQvlD5WgXYI5GY2kP2cCvoT8kczjbfcfuIljTbcWrulD1CIPIX2gt1wghbDy08yE1p+/r3w==}
    engines: {node: '>=6.9.0'}

  '@babel/helper-module-transforms@7.28.3':
    resolution: {integrity: sha512-gytXUbs8k2sXS9PnQptz5o0QnpLL51SwASIORY6XaBKF88nsOT0Zw9szLqlSGQDP/4TljBAD5y98p2U1fqkdsw==}
    engines: {node: '>=6.9.0'}
    peerDependencies:
      '@babel/core': ^7.0.0

  '@babel/helper-optimise-call-expression@7.27.1':
    resolution: {integrity: sha512-URMGH08NzYFhubNSGJrpUEphGKQwMQYBySzat5cAByY1/YgIRkULnIy3tAMeszlL/so2HbeilYloUmSpd7GdVw==}
    engines: {node: '>=6.9.0'}

  '@babel/helper-plugin-utils@7.27.1':
    resolution: {integrity: sha512-1gn1Up5YXka3YYAHGKpbideQ5Yjf1tDa9qYcgysz+cNCXukyLl6DjPXhD3VRwSb8c0J9tA4b2+rHEZtc6R0tlw==}
    engines: {node: '>=6.9.0'}

  '@babel/helper-remap-async-to-generator@7.27.1':
    resolution: {integrity: sha512-7fiA521aVw8lSPeI4ZOD3vRFkoqkJcS+z4hFo82bFSH/2tNd6eJ5qCVMS5OzDmZh/kaHQeBaeyxK6wljcPtveA==}
    engines: {node: '>=6.9.0'}
    peerDependencies:
      '@babel/core': ^7.0.0

  '@babel/helper-replace-supers@7.27.1':
    resolution: {integrity: sha512-7EHz6qDZc8RYS5ElPoShMheWvEgERonFCs7IAonWLLUTXW59DP14bCZt89/GKyreYn8g3S83m21FelHKbeDCKA==}
    engines: {node: '>=6.9.0'}
    peerDependencies:
      '@babel/core': ^7.0.0

  '@babel/helper-skip-transparent-expression-wrappers@7.27.1':
    resolution: {integrity: sha512-Tub4ZKEXqbPjXgWLl2+3JpQAYBJ8+ikpQ2Ocj/q/r0LwE3UhENh7EUabyHjz2kCEsrRY83ew2DQdHluuiDQFzg==}
    engines: {node: '>=6.9.0'}

  '@babel/helper-string-parser@7.27.1':
    resolution: {integrity: sha512-qMlSxKbpRlAridDExk92nSobyDdpPijUq2DW6oDnUqd0iOGxmQjyqhMIihI9+zv4LPyZdRje2cavWPbCbWm3eA==}
    engines: {node: '>=6.9.0'}

  '@babel/helper-validator-identifier@7.28.5':
    resolution: {integrity: sha512-qSs4ifwzKJSV39ucNjsvc6WVHs6b7S03sOh2OcHF9UHfVPqWWALUsNUVzhSBiItjRZoLHx7nIarVjqKVusUZ1Q==}
    engines: {node: '>=6.9.0'}

  '@babel/helper-validator-option@7.27.1':
    resolution: {integrity: sha512-YvjJow9FxbhFFKDSuFnVCe2WxXk1zWc22fFePVNEaWJEu8IrZVlda6N0uHwzZrUM1il7NC9Mlp4MaJYbYd9JSg==}
    engines: {node: '>=6.9.0'}

  '@babel/helper-wrap-function@7.28.3':
    resolution: {integrity: sha512-zdf983tNfLZFletc0RRXYrHrucBEg95NIFMkn6K9dbeMYnsgHaSBGcQqdsCSStG2PYwRre0Qc2NNSCXbG+xc6g==}
    engines: {node: '>=6.9.0'}

  '@babel/helpers@7.28.4':
    resolution: {integrity: sha512-HFN59MmQXGHVyYadKLVumYsA9dBFun/ldYxipEjzA4196jpLZd8UjEEBLkbEkvfYreDqJhZxYAWFPtrfhNpj4w==}
    engines: {node: '>=6.9.0'}

  '@babel/parser@7.28.5':
    resolution: {integrity: sha512-KKBU1VGYR7ORr3At5HAtUQ+TV3SzRCXmA/8OdDZiLDBIZxVyzXuztPjfLd3BV1PRAQGCMWWSHYhL0F8d5uHBDQ==}
    engines: {node: '>=6.0.0'}
    hasBin: true

  '@babel/plugin-bugfix-firefox-class-in-computed-class-key@7.28.5':
    resolution: {integrity: sha512-87GDMS3tsmMSi/3bWOte1UblL+YUTFMV8SZPZ2eSEL17s74Cw/l63rR6NmGVKMYW2GYi85nE+/d6Hw5N0bEk2Q==}
    engines: {node: '>=6.9.0'}
    peerDependencies:
      '@babel/core': ^7.0.0

  '@babel/plugin-bugfix-safari-class-field-initializer-scope@7.27.1':
    resolution: {integrity: sha512-qNeq3bCKnGgLkEXUuFry6dPlGfCdQNZbn7yUAPCInwAJHMU7THJfrBSozkcWq5sNM6RcF3S8XyQL2A52KNR9IA==}
    engines: {node: '>=6.9.0'}
    peerDependencies:
      '@babel/core': ^7.0.0

  '@babel/plugin-bugfix-safari-id-destructuring-collision-in-function-expression@7.27.1':
    resolution: {integrity: sha512-g4L7OYun04N1WyqMNjldFwlfPCLVkgB54A/YCXICZYBsvJJE3kByKv9c9+R/nAfmIfjl2rKYLNyMHboYbZaWaA==}
    engines: {node: '>=6.9.0'}
    peerDependencies:
      '@babel/core': ^7.0.0

  '@babel/plugin-bugfix-v8-spread-parameters-in-optional-chaining@7.27.1':
    resolution: {integrity: sha512-oO02gcONcD5O1iTLi/6frMJBIwWEHceWGSGqrpCmEL8nogiS6J9PBlE48CaK20/Jx1LuRml9aDftLgdjXT8+Cw==}
    engines: {node: '>=6.9.0'}
    peerDependencies:
      '@babel/core': ^7.13.0

  '@babel/plugin-bugfix-v8-static-class-fields-redefine-readonly@7.28.3':
    resolution: {integrity: sha512-b6YTX108evsvE4YgWyQ921ZAFFQm3Bn+CA3+ZXlNVnPhx+UfsVURoPjfGAPCjBgrqo30yX/C2nZGX96DxvR9Iw==}
    engines: {node: '>=6.9.0'}
    peerDependencies:
      '@babel/core': ^7.0.0

  '@babel/plugin-proposal-private-property-in-object@7.21.0-placeholder-for-preset-env.2':
    resolution: {integrity: sha512-SOSkfJDddaM7mak6cPEpswyTRnuRltl429hMraQEglW+OkovnCzsiszTmsrlY//qLFjCpQDFRvjdm2wA5pPm9w==}
    engines: {node: '>=6.9.0'}
    peerDependencies:
      '@babel/core': ^7.0.0-0

  '@babel/plugin-syntax-dynamic-import@7.8.3':
    resolution: {integrity: sha512-5gdGbFon+PszYzqs83S3E5mpi7/y/8M9eC90MRTZfduQOYW76ig6SOSPNe41IG5LoP3FGBn2N0RjVDSQiS94kQ==}
    peerDependencies:
      '@babel/core': ^7.0.0-0

  '@babel/plugin-syntax-import-assertions@7.27.1':
    resolution: {integrity: sha512-UT/Jrhw57xg4ILHLFnzFpPDlMbcdEicaAtjPQpbj9wa8T4r5KVWCimHcL/460g8Ht0DMxDyjsLgiWSkVjnwPFg==}
    engines: {node: '>=6.9.0'}
    peerDependencies:
      '@babel/core': ^7.0.0-0

  '@babel/plugin-syntax-import-attributes@7.27.1':
    resolution: {integrity: sha512-oFT0FrKHgF53f4vOsZGi2Hh3I35PfSmVs4IBFLFj4dnafP+hIWDLg3VyKmUHfLoLHlyxY4C7DGtmHuJgn+IGww==}
    engines: {node: '>=6.9.0'}
    peerDependencies:
      '@babel/core': ^7.0.0-0

  '@babel/plugin-syntax-jsx@7.27.1':
    resolution: {integrity: sha512-y8YTNIeKoyhGd9O0Jiyzyyqk8gdjnumGTQPsz0xOZOQ2RmkVJeZ1vmmfIvFEKqucBG6axJGBZDE/7iI5suUI/w==}
    engines: {node: '>=6.9.0'}
    peerDependencies:
      '@babel/core': ^7.0.0-0

  '@babel/plugin-syntax-typescript@7.27.1':
    resolution: {integrity: sha512-xfYCBMxveHrRMnAWl1ZlPXOZjzkN82THFvLhQhFXFt81Z5HnN+EtUkZhv/zcKpmT3fzmWZB0ywiBrbC3vogbwQ==}
    engines: {node: '>=6.9.0'}
    peerDependencies:
      '@babel/core': ^7.0.0-0

  '@babel/plugin-syntax-unicode-sets-regex@7.18.6':
    resolution: {integrity: sha512-727YkEAPwSIQTv5im8QHz3upqp92JTWhidIC81Tdx4VJYIte/VndKf1qKrfnnhPLiPghStWfvC/iFaMCQu7Nqg==}
    engines: {node: '>=6.9.0'}
    peerDependencies:
      '@babel/core': ^7.0.0

  '@babel/plugin-transform-arrow-functions@7.27.1':
    resolution: {integrity: sha512-8Z4TGic6xW70FKThA5HYEKKyBpOOsucTOD1DjU3fZxDg+K3zBJcXMFnt/4yQiZnf5+MiOMSXQ9PaEK/Ilh1DeA==}
    engines: {node: '>=6.9.0'}
    peerDependencies:
      '@babel/core': ^7.0.0-0

  '@babel/plugin-transform-async-generator-functions@7.28.0':
    resolution: {integrity: sha512-BEOdvX4+M765icNPZeidyADIvQ1m1gmunXufXxvRESy/jNNyfovIqUyE7MVgGBjWktCoJlzvFA1To2O4ymIO3Q==}
    engines: {node: '>=6.9.0'}
    peerDependencies:
      '@babel/core': ^7.0.0-0

  '@babel/plugin-transform-async-to-generator@7.27.1':
    resolution: {integrity: sha512-NREkZsZVJS4xmTr8qzE5y8AfIPqsdQfRuUiLRTEzb7Qii8iFWCyDKaUV2c0rCuh4ljDZ98ALHP/PetiBV2nddA==}
    engines: {node: '>=6.9.0'}
    peerDependencies:
      '@babel/core': ^7.0.0-0

  '@babel/plugin-transform-block-scoped-functions@7.27.1':
    resolution: {integrity: sha512-cnqkuOtZLapWYZUYM5rVIdv1nXYuFVIltZ6ZJ7nIj585QsjKM5dhL2Fu/lICXZ1OyIAFc7Qy+bvDAtTXqGrlhg==}
    engines: {node: '>=6.9.0'}
    peerDependencies:
      '@babel/core': ^7.0.0-0

  '@babel/plugin-transform-block-scoping@7.28.5':
    resolution: {integrity: sha512-45DmULpySVvmq9Pj3X9B+62Xe+DJGov27QravQJU1LLcapR6/10i+gYVAucGGJpHBp5mYxIMK4nDAT/QDLr47g==}
    engines: {node: '>=6.9.0'}
    peerDependencies:
      '@babel/core': ^7.0.0-0

  '@babel/plugin-transform-class-properties@7.27.1':
    resolution: {integrity: sha512-D0VcalChDMtuRvJIu3U/fwWjf8ZMykz5iZsg77Nuj821vCKI3zCyRLwRdWbsuJ/uRwZhZ002QtCqIkwC/ZkvbA==}
    engines: {node: '>=6.9.0'}
    peerDependencies:
      '@babel/core': ^7.0.0-0

  '@babel/plugin-transform-class-static-block@7.28.3':
    resolution: {integrity: sha512-LtPXlBbRoc4Njl/oh1CeD/3jC+atytbnf/UqLoqTDcEYGUPj022+rvfkbDYieUrSj3CaV4yHDByPE+T2HwfsJg==}
    engines: {node: '>=6.9.0'}
    peerDependencies:
      '@babel/core': ^7.12.0

  '@babel/plugin-transform-classes@7.28.4':
    resolution: {integrity: sha512-cFOlhIYPBv/iBoc+KS3M6et2XPtbT2HiCRfBXWtfpc9OAyostldxIf9YAYB6ypURBBbx+Qv6nyrLzASfJe+hBA==}
    engines: {node: '>=6.9.0'}
    peerDependencies:
      '@babel/core': ^7.0.0-0

  '@babel/plugin-transform-computed-properties@7.27.1':
    resolution: {integrity: sha512-lj9PGWvMTVksbWiDT2tW68zGS/cyo4AkZ/QTp0sQT0mjPopCmrSkzxeXkznjqBxzDI6TclZhOJbBmbBLjuOZUw==}
    engines: {node: '>=6.9.0'}
    peerDependencies:
      '@babel/core': ^7.0.0-0

  '@babel/plugin-transform-destructuring@7.28.5':
    resolution: {integrity: sha512-Kl9Bc6D0zTUcFUvkNuQh4eGXPKKNDOJQXVyyM4ZAQPMveniJdxi8XMJwLo+xSoW3MIq81bD33lcUe9kZpl0MCw==}
    engines: {node: '>=6.9.0'}
    peerDependencies:
      '@babel/core': ^7.0.0-0

  '@babel/plugin-transform-dotall-regex@7.27.1':
    resolution: {integrity: sha512-gEbkDVGRvjj7+T1ivxrfgygpT7GUd4vmODtYpbs0gZATdkX8/iSnOtZSxiZnsgm1YjTgjI6VKBGSJJevkrclzw==}
    engines: {node: '>=6.9.0'}
    peerDependencies:
      '@babel/core': ^7.0.0-0

  '@babel/plugin-transform-duplicate-keys@7.27.1':
    resolution: {integrity: sha512-MTyJk98sHvSs+cvZ4nOauwTTG1JeonDjSGvGGUNHreGQns+Mpt6WX/dVzWBHgg+dYZhkC4X+zTDfkTU+Vy9y7Q==}
    engines: {node: '>=6.9.0'}
    peerDependencies:
      '@babel/core': ^7.0.0-0

  '@babel/plugin-transform-duplicate-named-capturing-groups-regex@7.27.1':
    resolution: {integrity: sha512-hkGcueTEzuhB30B3eJCbCYeCaaEQOmQR0AdvzpD4LoN0GXMWzzGSuRrxR2xTnCrvNbVwK9N6/jQ92GSLfiZWoQ==}
    engines: {node: '>=6.9.0'}
    peerDependencies:
      '@babel/core': ^7.0.0

  '@babel/plugin-transform-dynamic-import@7.27.1':
    resolution: {integrity: sha512-MHzkWQcEmjzzVW9j2q8LGjwGWpG2mjwaaB0BNQwst3FIjqsg8Ct/mIZlvSPJvfi9y2AC8mi/ktxbFVL9pZ1I4A==}
    engines: {node: '>=6.9.0'}
    peerDependencies:
      '@babel/core': ^7.0.0-0

  '@babel/plugin-transform-explicit-resource-management@7.28.0':
    resolution: {integrity: sha512-K8nhUcn3f6iB+P3gwCv/no7OdzOZQcKchW6N389V6PD8NUWKZHzndOd9sPDVbMoBsbmjMqlB4L9fm+fEFNVlwQ==}
    engines: {node: '>=6.9.0'}
    peerDependencies:
      '@babel/core': ^7.0.0-0

  '@babel/plugin-transform-exponentiation-operator@7.28.5':
    resolution: {integrity: sha512-D4WIMaFtwa2NizOp+dnoFjRez/ClKiC2BqqImwKd1X28nqBtZEyCYJ2ozQrrzlxAFrcrjxo39S6khe9RNDlGzw==}
    engines: {node: '>=6.9.0'}
    peerDependencies:
      '@babel/core': ^7.0.0-0

  '@babel/plugin-transform-export-namespace-from@7.27.1':
    resolution: {integrity: sha512-tQvHWSZ3/jH2xuq/vZDy0jNn+ZdXJeM8gHvX4lnJmsc3+50yPlWdZXIc5ay+umX+2/tJIqHqiEqcJvxlmIvRvQ==}
    engines: {node: '>=6.9.0'}
    peerDependencies:
      '@babel/core': ^7.0.0-0

  '@babel/plugin-transform-for-of@7.27.1':
    resolution: {integrity: sha512-BfbWFFEJFQzLCQ5N8VocnCtA8J1CLkNTe2Ms2wocj75dd6VpiqS5Z5quTYcUoo4Yq+DN0rtikODccuv7RU81sw==}
    engines: {node: '>=6.9.0'}
    peerDependencies:
      '@babel/core': ^7.0.0-0

  '@babel/plugin-transform-function-name@7.27.1':
    resolution: {integrity: sha512-1bQeydJF9Nr1eBCMMbC+hdwmRlsv5XYOMu03YSWFwNs0HsAmtSxxF1fyuYPqemVldVyFmlCU7w8UE14LupUSZQ==}
    engines: {node: '>=6.9.0'}
    peerDependencies:
      '@babel/core': ^7.0.0-0

  '@babel/plugin-transform-json-strings@7.27.1':
    resolution: {integrity: sha512-6WVLVJiTjqcQauBhn1LkICsR2H+zm62I3h9faTDKt1qP4jn2o72tSvqMwtGFKGTpojce0gJs+76eZ2uCHRZh0Q==}
    engines: {node: '>=6.9.0'}
    peerDependencies:
      '@babel/core': ^7.0.0-0

  '@babel/plugin-transform-literals@7.27.1':
    resolution: {integrity: sha512-0HCFSepIpLTkLcsi86GG3mTUzxV5jpmbv97hTETW3yzrAij8aqlD36toB1D0daVFJM8NK6GvKO0gslVQmm+zZA==}
    engines: {node: '>=6.9.0'}
    peerDependencies:
      '@babel/core': ^7.0.0-0

  '@babel/plugin-transform-logical-assignment-operators@7.28.5':
    resolution: {integrity: sha512-axUuqnUTBuXyHGcJEVVh9pORaN6wC5bYfE7FGzPiaWa3syib9m7g+/IT/4VgCOe2Upef43PHzeAvcrVek6QuuA==}
    engines: {node: '>=6.9.0'}
    peerDependencies:
      '@babel/core': ^7.0.0-0

  '@babel/plugin-transform-member-expression-literals@7.27.1':
    resolution: {integrity: sha512-hqoBX4dcZ1I33jCSWcXrP+1Ku7kdqXf1oeah7ooKOIiAdKQ+uqftgCFNOSzA5AMS2XIHEYeGFg4cKRCdpxzVOQ==}
    engines: {node: '>=6.9.0'}
    peerDependencies:
      '@babel/core': ^7.0.0-0

  '@babel/plugin-transform-modules-amd@7.27.1':
    resolution: {integrity: sha512-iCsytMg/N9/oFq6n+gFTvUYDZQOMK5kEdeYxmxt91fcJGycfxVP9CnrxoliM0oumFERba2i8ZtwRUCMhvP1LnA==}
    engines: {node: '>=6.9.0'}
    peerDependencies:
      '@babel/core': ^7.0.0-0

  '@babel/plugin-transform-modules-commonjs@7.27.1':
    resolution: {integrity: sha512-OJguuwlTYlN0gBZFRPqwOGNWssZjfIUdS7HMYtN8c1KmwpwHFBwTeFZrg9XZa+DFTitWOW5iTAG7tyCUPsCCyw==}
    engines: {node: '>=6.9.0'}
    peerDependencies:
      '@babel/core': ^7.0.0-0

  '@babel/plugin-transform-modules-systemjs@7.28.5':
    resolution: {integrity: sha512-vn5Jma98LCOeBy/KpeQhXcV2WZgaRUtjwQmjoBuLNlOmkg0fB5pdvYVeWRYI69wWKwK2cD1QbMiUQnoujWvrew==}
    engines: {node: '>=6.9.0'}
    peerDependencies:
      '@babel/core': ^7.0.0-0

  '@babel/plugin-transform-modules-umd@7.27.1':
    resolution: {integrity: sha512-iQBE/xC5BV1OxJbp6WG7jq9IWiD+xxlZhLrdwpPkTX3ydmXdvoCpyfJN7acaIBZaOqTfr76pgzqBJflNbeRK+w==}
    engines: {node: '>=6.9.0'}
    peerDependencies:
      '@babel/core': ^7.0.0-0

  '@babel/plugin-transform-named-capturing-groups-regex@7.27.1':
    resolution: {integrity: sha512-SstR5JYy8ddZvD6MhV0tM/j16Qds4mIpJTOd1Yu9J9pJjH93bxHECF7pgtc28XvkzTD6Pxcm/0Z73Hvk7kb3Ng==}
    engines: {node: '>=6.9.0'}
    peerDependencies:
      '@babel/core': ^7.0.0

  '@babel/plugin-transform-new-target@7.27.1':
    resolution: {integrity: sha512-f6PiYeqXQ05lYq3TIfIDu/MtliKUbNwkGApPUvyo6+tc7uaR4cPjPe7DFPr15Uyycg2lZU6btZ575CuQoYh7MQ==}
    engines: {node: '>=6.9.0'}
    peerDependencies:
      '@babel/core': ^7.0.0-0

  '@babel/plugin-transform-nullish-coalescing-operator@7.27.1':
    resolution: {integrity: sha512-aGZh6xMo6q9vq1JGcw58lZ1Z0+i0xB2x0XaauNIUXd6O1xXc3RwoWEBlsTQrY4KQ9Jf0s5rgD6SiNkaUdJegTA==}
    engines: {node: '>=6.9.0'}
    peerDependencies:
      '@babel/core': ^7.0.0-0

  '@babel/plugin-transform-numeric-separator@7.27.1':
    resolution: {integrity: sha512-fdPKAcujuvEChxDBJ5c+0BTaS6revLV7CJL08e4m3de8qJfNIuCc2nc7XJYOjBoTMJeqSmwXJ0ypE14RCjLwaw==}
    engines: {node: '>=6.9.0'}
    peerDependencies:
      '@babel/core': ^7.0.0-0

  '@babel/plugin-transform-object-rest-spread@7.28.4':
    resolution: {integrity: sha512-373KA2HQzKhQCYiRVIRr+3MjpCObqzDlyrM6u4I201wL8Mp2wHf7uB8GhDwis03k2ti8Zr65Zyyqs1xOxUF/Ew==}
    engines: {node: '>=6.9.0'}
    peerDependencies:
      '@babel/core': ^7.0.0-0

  '@babel/plugin-transform-object-super@7.27.1':
    resolution: {integrity: sha512-SFy8S9plRPbIcxlJ8A6mT/CxFdJx/c04JEctz4jf8YZaVS2px34j7NXRrlGlHkN/M2gnpL37ZpGRGVFLd3l8Ng==}
    engines: {node: '>=6.9.0'}
    peerDependencies:
      '@babel/core': ^7.0.0-0

  '@babel/plugin-transform-optional-catch-binding@7.27.1':
    resolution: {integrity: sha512-txEAEKzYrHEX4xSZN4kJ+OfKXFVSWKB2ZxM9dpcE3wT7smwkNmXo5ORRlVzMVdJbD+Q8ILTgSD7959uj+3Dm3Q==}
    engines: {node: '>=6.9.0'}
    peerDependencies:
      '@babel/core': ^7.0.0-0

  '@babel/plugin-transform-optional-chaining@7.28.5':
    resolution: {integrity: sha512-N6fut9IZlPnjPwgiQkXNhb+cT8wQKFlJNqcZkWlcTqkcqx6/kU4ynGmLFoa4LViBSirn05YAwk+sQBbPfxtYzQ==}
    engines: {node: '>=6.9.0'}
    peerDependencies:
      '@babel/core': ^7.0.0-0

  '@babel/plugin-transform-parameters@7.27.7':
    resolution: {integrity: sha512-qBkYTYCb76RRxUM6CcZA5KRu8K4SM8ajzVeUgVdMVO9NN9uI/GaVmBg/WKJJGnNokV9SY8FxNOVWGXzqzUidBg==}
    engines: {node: '>=6.9.0'}
    peerDependencies:
      '@babel/core': ^7.0.0-0

  '@babel/plugin-transform-private-methods@7.27.1':
    resolution: {integrity: sha512-10FVt+X55AjRAYI9BrdISN9/AQWHqldOeZDUoLyif1Kn05a56xVBXb8ZouL8pZ9jem8QpXaOt8TS7RHUIS+GPA==}
    engines: {node: '>=6.9.0'}
    peerDependencies:
      '@babel/core': ^7.0.0-0

  '@babel/plugin-transform-private-property-in-object@7.27.1':
    resolution: {integrity: sha512-5J+IhqTi1XPa0DXF83jYOaARrX+41gOewWbkPyjMNRDqgOCqdffGh8L3f/Ek5utaEBZExjSAzcyjmV9SSAWObQ==}
    engines: {node: '>=6.9.0'}
    peerDependencies:
      '@babel/core': ^7.0.0-0

  '@babel/plugin-transform-property-literals@7.27.1':
    resolution: {integrity: sha512-oThy3BCuCha8kDZ8ZkgOg2exvPYUlprMukKQXI1r1pJ47NCvxfkEy8vK+r/hT9nF0Aa4H1WUPZZjHTFtAhGfmQ==}
    engines: {node: '>=6.9.0'}
    peerDependencies:
      '@babel/core': ^7.0.0-0

  '@babel/plugin-transform-react-constant-elements@7.27.1':
    resolution: {integrity: sha512-edoidOjl/ZxvYo4lSBOQGDSyToYVkTAwyVoa2tkuYTSmjrB1+uAedoL5iROVLXkxH+vRgA7uP4tMg2pUJpZ3Ug==}
    engines: {node: '>=6.9.0'}
    peerDependencies:
      '@babel/core': ^7.0.0-0

  '@babel/plugin-transform-react-display-name@7.28.0':
    resolution: {integrity: sha512-D6Eujc2zMxKjfa4Zxl4GHMsmhKKZ9VpcqIchJLvwTxad9zWIYulwYItBovpDOoNLISpcZSXoDJ5gaGbQUDqViA==}
    engines: {node: '>=6.9.0'}
    peerDependencies:
      '@babel/core': ^7.0.0-0

  '@babel/plugin-transform-react-jsx-development@7.27.1':
    resolution: {integrity: sha512-ykDdF5yI4f1WrAolLqeF3hmYU12j9ntLQl/AOG1HAS21jxyg1Q0/J/tpREuYLfatGdGmXp/3yS0ZA76kOlVq9Q==}
    engines: {node: '>=6.9.0'}
    peerDependencies:
      '@babel/core': ^7.0.0-0

  '@babel/plugin-transform-react-jsx@7.27.1':
    resolution: {integrity: sha512-2KH4LWGSrJIkVf5tSiBFYuXDAoWRq2MMwgivCf+93dd0GQi8RXLjKA/0EvRnVV5G0hrHczsquXuD01L8s6dmBw==}
    engines: {node: '>=6.9.0'}
    peerDependencies:
      '@babel/core': ^7.0.0-0

  '@babel/plugin-transform-react-pure-annotations@7.27.1':
    resolution: {integrity: sha512-JfuinvDOsD9FVMTHpzA/pBLisxpv1aSf+OIV8lgH3MuWrks19R27e6a6DipIg4aX1Zm9Wpb04p8wljfKrVSnPA==}
    engines: {node: '>=6.9.0'}
    peerDependencies:
      '@babel/core': ^7.0.0-0

  '@babel/plugin-transform-regenerator@7.28.4':
    resolution: {integrity: sha512-+ZEdQlBoRg9m2NnzvEeLgtvBMO4tkFBw5SQIUgLICgTrumLoU7lr+Oghi6km2PFj+dbUt2u1oby2w3BDO9YQnA==}
    engines: {node: '>=6.9.0'}
    peerDependencies:
      '@babel/core': ^7.0.0-0

  '@babel/plugin-transform-regexp-modifiers@7.27.1':
    resolution: {integrity: sha512-TtEciroaiODtXvLZv4rmfMhkCv8jx3wgKpL68PuiPh2M4fvz5jhsA7697N1gMvkvr/JTF13DrFYyEbY9U7cVPA==}
    engines: {node: '>=6.9.0'}
    peerDependencies:
      '@babel/core': ^7.0.0

  '@babel/plugin-transform-reserved-words@7.27.1':
    resolution: {integrity: sha512-V2ABPHIJX4kC7HegLkYoDpfg9PVmuWy/i6vUM5eGK22bx4YVFD3M5F0QQnWQoDs6AGsUWTVOopBiMFQgHaSkVw==}
    engines: {node: '>=6.9.0'}
    peerDependencies:
      '@babel/core': ^7.0.0-0

  '@babel/plugin-transform-runtime@7.28.5':
    resolution: {integrity: sha512-20NUVgOrinudkIBzQ2bNxP08YpKprUkRTiRSd2/Z5GOdPImJGkoN4Z7IQe1T5AdyKI1i5L6RBmluqdSzvaq9/w==}
    engines: {node: '>=6.9.0'}
    peerDependencies:
      '@babel/core': ^7.0.0-0

  '@babel/plugin-transform-shorthand-properties@7.27.1':
    resolution: {integrity: sha512-N/wH1vcn4oYawbJ13Y/FxcQrWk63jhfNa7jef0ih7PHSIHX2LB7GWE1rkPrOnka9kwMxb6hMl19p7lidA+EHmQ==}
    engines: {node: '>=6.9.0'}
    peerDependencies:
      '@babel/core': ^7.0.0-0

  '@babel/plugin-transform-spread@7.27.1':
    resolution: {integrity: sha512-kpb3HUqaILBJcRFVhFUs6Trdd4mkrzcGXss+6/mxUd273PfbWqSDHRzMT2234gIg2QYfAjvXLSquP1xECSg09Q==}
    engines: {node: '>=6.9.0'}
    peerDependencies:
      '@babel/core': ^7.0.0-0

  '@babel/plugin-transform-sticky-regex@7.27.1':
    resolution: {integrity: sha512-lhInBO5bi/Kowe2/aLdBAawijx+q1pQzicSgnkB6dUPc1+RC8QmJHKf2OjvU+NZWitguJHEaEmbV6VWEouT58g==}
    engines: {node: '>=6.9.0'}
    peerDependencies:
      '@babel/core': ^7.0.0-0

  '@babel/plugin-transform-template-literals@7.27.1':
    resolution: {integrity: sha512-fBJKiV7F2DxZUkg5EtHKXQdbsbURW3DZKQUWphDum0uRP6eHGGa/He9mc0mypL680pb+e/lDIthRohlv8NCHkg==}
    engines: {node: '>=6.9.0'}
    peerDependencies:
      '@babel/core': ^7.0.0-0

  '@babel/plugin-transform-typeof-symbol@7.27.1':
    resolution: {integrity: sha512-RiSILC+nRJM7FY5srIyc4/fGIwUhyDuuBSdWn4y6yT6gm652DpCHZjIipgn6B7MQ1ITOUnAKWixEUjQRIBIcLw==}
    engines: {node: '>=6.9.0'}
    peerDependencies:
      '@babel/core': ^7.0.0-0

  '@babel/plugin-transform-typescript@7.28.5':
    resolution: {integrity: sha512-x2Qa+v/CuEoX7Dr31iAfr0IhInrVOWZU/2vJMJ00FOR/2nM0BcBEclpaf9sWCDc+v5e9dMrhSH8/atq/kX7+bA==}
    engines: {node: '>=6.9.0'}
    peerDependencies:
      '@babel/core': ^7.0.0-0

  '@babel/plugin-transform-unicode-escapes@7.27.1':
    resolution: {integrity: sha512-Ysg4v6AmF26k9vpfFuTZg8HRfVWzsh1kVfowA23y9j/Gu6dOuahdUVhkLqpObp3JIv27MLSii6noRnuKN8H0Mg==}
    engines: {node: '>=6.9.0'}
    peerDependencies:
      '@babel/core': ^7.0.0-0

  '@babel/plugin-transform-unicode-property-regex@7.27.1':
    resolution: {integrity: sha512-uW20S39PnaTImxp39O5qFlHLS9LJEmANjMG7SxIhap8rCHqu0Ik+tLEPX5DKmHn6CsWQ7j3lix2tFOa5YtL12Q==}
    engines: {node: '>=6.9.0'}
    peerDependencies:
      '@babel/core': ^7.0.0-0

  '@babel/plugin-transform-unicode-regex@7.27.1':
    resolution: {integrity: sha512-xvINq24TRojDuyt6JGtHmkVkrfVV3FPT16uytxImLeBZqW3/H52yN+kM1MGuyPkIQxrzKwPHs5U/MP3qKyzkGw==}
    engines: {node: '>=6.9.0'}
    peerDependencies:
      '@babel/core': ^7.0.0-0

  '@babel/plugin-transform-unicode-sets-regex@7.27.1':
    resolution: {integrity: sha512-EtkOujbc4cgvb0mlpQefi4NTPBzhSIevblFevACNLUspmrALgmEBdL/XfnyyITfd8fKBZrZys92zOWcik7j9Tw==}
    engines: {node: '>=6.9.0'}
    peerDependencies:
      '@babel/core': ^7.0.0

  '@babel/preset-env@7.28.5':
    resolution: {integrity: sha512-S36mOoi1Sb6Fz98fBfE+UZSpYw5mJm0NUHtIKrOuNcqeFauy1J6dIvXm2KRVKobOSaGq4t/hBXdN4HGU3wL9Wg==}
    engines: {node: '>=6.9.0'}
    peerDependencies:
      '@babel/core': ^7.0.0-0

  '@babel/preset-modules@0.1.6-no-external-plugins':
    resolution: {integrity: sha512-HrcgcIESLm9aIR842yhJ5RWan/gebQUJ6E/E5+rf0y9o6oj7w0Br+sWuL6kEQ/o/AdfvR1Je9jG18/gnpwjEyA==}
    peerDependencies:
      '@babel/core': ^7.0.0-0 || ^8.0.0-0 <8.0.0

  '@babel/preset-react@7.28.5':
    resolution: {integrity: sha512-Z3J8vhRq7CeLjdC58jLv4lnZ5RKFUJWqH5emvxmv9Hv3BD1T9R/Im713R4MTKwvFaV74ejZ3sM01LyEKk4ugNQ==}
    engines: {node: '>=6.9.0'}
    peerDependencies:
      '@babel/core': ^7.0.0-0

  '@babel/preset-typescript@7.28.5':
    resolution: {integrity: sha512-+bQy5WOI2V6LJZpPVxY+yp66XdZ2yifu0Mc1aP5CQKgjn4QM5IN2i5fAZ4xKop47pr8rpVhiAeu+nDQa12C8+g==}
    engines: {node: '>=6.9.0'}
    peerDependencies:
      '@babel/core': ^7.0.0-0

  '@babel/runtime-corejs3@7.28.4':
    resolution: {integrity: sha512-h7iEYiW4HebClDEhtvFObtPmIvrd1SSfpI9EhOeKk4CtIK/ngBWFpuhCzhdmRKtg71ylcue+9I6dv54XYO1epQ==}
    engines: {node: '>=6.9.0'}

  '@babel/runtime@7.28.4':
    resolution: {integrity: sha512-Q/N6JNWvIvPnLDvjlE1OUBLPQHH6l3CltCEsHIujp45zQUSSh8K+gHnaEX45yAT1nyngnINhvWtzN+Nb9D8RAQ==}
    engines: {node: '>=6.9.0'}

  '@babel/template@7.27.2':
    resolution: {integrity: sha512-LPDZ85aEJyYSd18/DkjNh4/y1ntkE5KwUHWTiqgRxruuZL2F1yuHligVHLvcHY2vMHXttKFpJn6LwfI7cw7ODw==}
    engines: {node: '>=6.9.0'}

  '@babel/traverse@7.28.5':
    resolution: {integrity: sha512-TCCj4t55U90khlYkVV/0TfkJkAkUg3jZFA3Neb7unZT8CPok7iiRfaX0F+WnqWqt7OxhOn0uBKXCw4lbL8W0aQ==}
    engines: {node: '>=6.9.0'}

  '@babel/types@7.28.5':
    resolution: {integrity: sha512-qQ5m48eI/MFLQ5PxQj4PFaprjyCTLI37ElWMmNs0K8Lk3dVeOdNpB3ks8jc7yM5CDmVC73eMVk/trk3fgmrUpA==}
    engines: {node: '>=6.9.0'}

  '@braintree/sanitize-url@7.1.1':
    resolution: {integrity: sha512-i1L7noDNxtFyL5DmZafWy1wRVhGehQmzZaz1HiN5e7iylJMSZR7ekOV7NsIqa5qBldlLrsKv4HbgFUVlQrz8Mw==}

  '@chevrotain/cst-dts-gen@11.0.3':
    resolution: {integrity: sha512-BvIKpRLeS/8UbfxXxgC33xOumsacaeCKAjAeLyOn7Pcp95HiRbrpl14S+9vaZLolnbssPIUuiUd8IvgkRyt6NQ==}

  '@chevrotain/gast@11.0.3':
    resolution: {integrity: sha512-+qNfcoNk70PyS/uxmj3li5NiECO+2YKZZQMbmjTqRI3Qchu8Hig/Q9vgkHpI3alNjr7M+a2St5pw5w5F6NL5/Q==}

  '@chevrotain/regexp-to-ast@11.0.3':
    resolution: {integrity: sha512-1fMHaBZxLFvWI067AVbGJav1eRY7N8DDvYCTwGBiE/ytKBgP8azTdgyrKyWZ9Mfh09eHWb5PgTSO8wi7U824RA==}

  '@chevrotain/types@11.0.3':
    resolution: {integrity: sha512-gsiM3G8b58kZC2HaWR50gu6Y1440cHiJ+i3JUvcp/35JchYejb2+5MVeJK0iKThYpAa/P2PYFV4hoi44HD+aHQ==}

  '@chevrotain/utils@11.0.3':
    resolution: {integrity: sha512-YslZMgtJUyuMbZ+aKvfF3x1f5liK4mWNxghFRv7jqRR9C3R3fAOGTTKvxXDa2Y1s9zSbcpuO0cAxDYsc9SrXoQ==}

  '@colors/colors@1.5.0':
    resolution: {integrity: sha512-ooWCrlZP11i8GImSjTHYHLkvFDP48nS4+204nGb1RiX/WXYHmJA2III9/e2DWVabCESdW7hBAEzHRqUn9OUVvQ==}
    engines: {node: '>=0.1.90'}

  '@csstools/cascade-layer-name-parser@2.0.5':
    resolution: {integrity: sha512-p1ko5eHgV+MgXFVa4STPKpvPxr6ReS8oS2jzTukjR74i5zJNyWO1ZM1m8YKBXnzDKWfBN1ztLYlHxbVemDD88A==}
    engines: {node: '>=18'}
    peerDependencies:
      '@csstools/css-parser-algorithms': ^3.0.5
      '@csstools/css-tokenizer': ^3.0.4

  '@csstools/color-helpers@5.1.0':
    resolution: {integrity: sha512-S11EXWJyy0Mz5SYvRmY8nJYTFFd1LCNV+7cXyAgQtOOuzb4EsgfqDufL+9esx72/eLhsRdGZwaldu/h+E4t4BA==}
    engines: {node: '>=18'}

  '@csstools/css-calc@2.1.4':
    resolution: {integrity: sha512-3N8oaj+0juUw/1H3YwmDDJXCgTB1gKU6Hc/bB502u9zR0q2vd786XJH9QfrKIEgFlZmhZiq6epXl4rHqhzsIgQ==}
    engines: {node: '>=18'}
    peerDependencies:
      '@csstools/css-parser-algorithms': ^3.0.5
      '@csstools/css-tokenizer': ^3.0.4

  '@csstools/css-color-parser@3.1.0':
    resolution: {integrity: sha512-nbtKwh3a6xNVIp/VRuXV64yTKnb1IjTAEEh3irzS+HkKjAOYLTGNb9pmVNntZ8iVBHcWDA2Dof0QtPgFI1BaTA==}
    engines: {node: '>=18'}
    peerDependencies:
      '@csstools/css-parser-algorithms': ^3.0.5
      '@csstools/css-tokenizer': ^3.0.4

  '@csstools/css-parser-algorithms@3.0.5':
    resolution: {integrity: sha512-DaDeUkXZKjdGhgYaHNJTV9pV7Y9B3b644jCLs9Upc3VeNGg6LWARAT6O+Q+/COo+2gg/bM5rhpMAtf70WqfBdQ==}
    engines: {node: '>=18'}
    peerDependencies:
      '@csstools/css-tokenizer': ^3.0.4

  '@csstools/css-tokenizer@3.0.4':
    resolution: {integrity: sha512-Vd/9EVDiu6PPJt9yAh6roZP6El1xHrdvIVGjyBsHR0RYwNHgL7FJPyIIW4fANJNG6FtyZfvlRPpFI4ZM/lubvw==}
    engines: {node: '>=18'}

  '@csstools/media-query-list-parser@4.0.3':
    resolution: {integrity: sha512-HAYH7d3TLRHDOUQK4mZKf9k9Ph/m8Akstg66ywKR4SFAigjs3yBiUeZtFxywiTm5moZMAp/5W/ZuFnNXXYLuuQ==}
    engines: {node: '>=18'}
    peerDependencies:
      '@csstools/css-parser-algorithms': ^3.0.5
      '@csstools/css-tokenizer': ^3.0.4

  '@csstools/postcss-alpha-function@1.0.1':
    resolution: {integrity: sha512-isfLLwksH3yHkFXfCI2Gcaqg7wGGHZZwunoJzEZk0yKYIokgre6hYVFibKL3SYAoR1kBXova8LB+JoO5vZzi9w==}
    engines: {node: '>=18'}
    peerDependencies:
      postcss: ^8.4

  '@csstools/postcss-cascade-layers@5.0.2':
    resolution: {integrity: sha512-nWBE08nhO8uWl6kSAeCx4im7QfVko3zLrtgWZY4/bP87zrSPpSyN/3W3TDqz1jJuH+kbKOHXg5rJnK+ZVYcFFg==}
    engines: {node: '>=18'}
    peerDependencies:
      postcss: ^8.4

  '@csstools/postcss-color-function-display-p3-linear@1.0.1':
    resolution: {integrity: sha512-E5qusdzhlmO1TztYzDIi8XPdPoYOjoTY6HBYBCYSj+Gn4gQRBlvjgPQXzfzuPQqt8EhkC/SzPKObg4Mbn8/xMg==}
    engines: {node: '>=18'}
    peerDependencies:
      postcss: ^8.4

  '@csstools/postcss-color-function@4.0.12':
    resolution: {integrity: sha512-yx3cljQKRaSBc2hfh8rMZFZzChaFgwmO2JfFgFr1vMcF3C/uyy5I4RFIBOIWGq1D+XbKCG789CGkG6zzkLpagA==}
    engines: {node: '>=18'}
    peerDependencies:
      postcss: ^8.4

  '@csstools/postcss-color-mix-function@3.0.12':
    resolution: {integrity: sha512-4STERZfCP5Jcs13P1U5pTvI9SkgLgfMUMhdXW8IlJWkzOOOqhZIjcNhWtNJZes2nkBDsIKJ0CJtFtuaZ00moag==}
    engines: {node: '>=18'}
    peerDependencies:
      postcss: ^8.4

  '@csstools/postcss-color-mix-variadic-function-arguments@1.0.2':
    resolution: {integrity: sha512-rM67Gp9lRAkTo+X31DUqMEq+iK+EFqsidfecmhrteErxJZb6tUoJBVQca1Vn1GpDql1s1rD1pKcuYzMsg7Z1KQ==}
    engines: {node: '>=18'}
    peerDependencies:
      postcss: ^8.4

  '@csstools/postcss-content-alt-text@2.0.8':
    resolution: {integrity: sha512-9SfEW9QCxEpTlNMnpSqFaHyzsiRpZ5J5+KqCu1u5/eEJAWsMhzT40qf0FIbeeglEvrGRMdDzAxMIz3wqoGSb+Q==}
    engines: {node: '>=18'}
    peerDependencies:
      postcss: ^8.4

  '@csstools/postcss-contrast-color-function@2.0.12':
    resolution: {integrity: sha512-YbwWckjK3qwKjeYz/CijgcS7WDUCtKTd8ShLztm3/i5dhh4NaqzsbYnhm4bjrpFpnLZ31jVcbK8YL77z3GBPzA==}
    engines: {node: '>=18'}
    peerDependencies:
      postcss: ^8.4

  '@csstools/postcss-exponential-functions@2.0.9':
    resolution: {integrity: sha512-abg2W/PI3HXwS/CZshSa79kNWNZHdJPMBXeZNyPQFbbj8sKO3jXxOt/wF7juJVjyDTc6JrvaUZYFcSBZBhaxjw==}
    engines: {node: '>=18'}
    peerDependencies:
      postcss: ^8.4

  '@csstools/postcss-font-format-keywords@4.0.0':
    resolution: {integrity: sha512-usBzw9aCRDvchpok6C+4TXC57btc4bJtmKQWOHQxOVKen1ZfVqBUuCZ/wuqdX5GHsD0NRSr9XTP+5ID1ZZQBXw==}
    engines: {node: '>=18'}
    peerDependencies:
      postcss: ^8.4

  '@csstools/postcss-gamut-mapping@2.0.11':
    resolution: {integrity: sha512-fCpCUgZNE2piVJKC76zFsgVW1apF6dpYsqGyH8SIeCcM4pTEsRTWTLCaJIMKFEundsCKwY1rwfhtrio04RJ4Dw==}
    engines: {node: '>=18'}
    peerDependencies:
      postcss: ^8.4

  '@csstools/postcss-gradients-interpolation-method@5.0.12':
    resolution: {integrity: sha512-jugzjwkUY0wtNrZlFeyXzimUL3hN4xMvoPnIXxoZqxDvjZRiSh+itgHcVUWzJ2VwD/VAMEgCLvtaJHX+4Vj3Ow==}
    engines: {node: '>=18'}
    peerDependencies:
      postcss: ^8.4

  '@csstools/postcss-hwb-function@4.0.12':
    resolution: {integrity: sha512-mL/+88Z53KrE4JdePYFJAQWFrcADEqsLprExCM04GDNgHIztwFzj0Mbhd/yxMBngq0NIlz58VVxjt5abNs1VhA==}
    engines: {node: '>=18'}
    peerDependencies:
      postcss: ^8.4

  '@csstools/postcss-ic-unit@4.0.4':
    resolution: {integrity: sha512-yQ4VmossuOAql65sCPppVO1yfb7hDscf4GseF0VCA/DTDaBc0Wtf8MTqVPfjGYlT5+2buokG0Gp7y0atYZpwjg==}
    engines: {node: '>=18'}
    peerDependencies:
      postcss: ^8.4

  '@csstools/postcss-initial@2.0.1':
    resolution: {integrity: sha512-L1wLVMSAZ4wovznquK0xmC7QSctzO4D0Is590bxpGqhqjboLXYA16dWZpfwImkdOgACdQ9PqXsuRroW6qPlEsg==}
    engines: {node: '>=18'}
    peerDependencies:
      postcss: ^8.4

  '@csstools/postcss-is-pseudo-class@5.0.3':
    resolution: {integrity: sha512-jS/TY4SpG4gszAtIg7Qnf3AS2pjcUM5SzxpApOrlndMeGhIbaTzWBzzP/IApXoNWEW7OhcjkRT48jnAUIFXhAQ==}
    engines: {node: '>=18'}
    peerDependencies:
      postcss: ^8.4

  '@csstools/postcss-light-dark-function@2.0.11':
    resolution: {integrity: sha512-fNJcKXJdPM3Lyrbmgw2OBbaioU7yuKZtiXClf4sGdQttitijYlZMD5K7HrC/eF83VRWRrYq6OZ0Lx92leV2LFA==}
    engines: {node: '>=18'}
    peerDependencies:
      postcss: ^8.4

  '@csstools/postcss-logical-float-and-clear@3.0.0':
    resolution: {integrity: sha512-SEmaHMszwakI2rqKRJgE+8rpotFfne1ZS6bZqBoQIicFyV+xT1UF42eORPxJkVJVrH9C0ctUgwMSn3BLOIZldQ==}
    engines: {node: '>=18'}
    peerDependencies:
      postcss: ^8.4

  '@csstools/postcss-logical-overflow@2.0.0':
    resolution: {integrity: sha512-spzR1MInxPuXKEX2csMamshR4LRaSZ3UXVaRGjeQxl70ySxOhMpP2252RAFsg8QyyBXBzuVOOdx1+bVO5bPIzA==}
    engines: {node: '>=18'}
    peerDependencies:
      postcss: ^8.4

  '@csstools/postcss-logical-overscroll-behavior@2.0.0':
    resolution: {integrity: sha512-e/webMjoGOSYfqLunyzByZj5KKe5oyVg/YSbie99VEaSDE2kimFm0q1f6t/6Jo+VVCQ/jbe2Xy+uX+C4xzWs4w==}
    engines: {node: '>=18'}
    peerDependencies:
      postcss: ^8.4

  '@csstools/postcss-logical-resize@3.0.0':
    resolution: {integrity: sha512-DFbHQOFW/+I+MY4Ycd/QN6Dg4Hcbb50elIJCfnwkRTCX05G11SwViI5BbBlg9iHRl4ytB7pmY5ieAFk3ws7yyg==}
    engines: {node: '>=18'}
    peerDependencies:
      postcss: ^8.4

  '@csstools/postcss-logical-viewport-units@3.0.4':
    resolution: {integrity: sha512-q+eHV1haXA4w9xBwZLKjVKAWn3W2CMqmpNpZUk5kRprvSiBEGMgrNH3/sJZ8UA3JgyHaOt3jwT9uFa4wLX4EqQ==}
    engines: {node: '>=18'}
    peerDependencies:
      postcss: ^8.4

  '@csstools/postcss-media-minmax@2.0.9':
    resolution: {integrity: sha512-af9Qw3uS3JhYLnCbqtZ9crTvvkR+0Se+bBqSr7ykAnl9yKhk6895z9rf+2F4dClIDJWxgn0iZZ1PSdkhrbs2ig==}
    engines: {node: '>=18'}
    peerDependencies:
      postcss: ^8.4

  '@csstools/postcss-media-queries-aspect-ratio-number-values@3.0.5':
    resolution: {integrity: sha512-zhAe31xaaXOY2Px8IYfoVTB3wglbJUVigGphFLj6exb7cjZRH9A6adyE22XfFK3P2PzwRk0VDeTJmaxpluyrDg==}
    engines: {node: '>=18'}
    peerDependencies:
      postcss: ^8.4

  '@csstools/postcss-nested-calc@4.0.0':
    resolution: {integrity: sha512-jMYDdqrQQxE7k9+KjstC3NbsmC063n1FTPLCgCRS2/qHUbHM0mNy9pIn4QIiQGs9I/Bg98vMqw7mJXBxa0N88A==}
    engines: {node: '>=18'}
    peerDependencies:
      postcss: ^8.4

  '@csstools/postcss-normalize-display-values@4.0.1':
    resolution: {integrity: sha512-TQUGBuRvxdc7TgNSTevYqrL8oItxiwPDixk20qCB5me/W8uF7BPbhRrAvFuhEoywQp/woRsUZ6SJ+sU5idZAIA==}
    engines: {node: '>=18'}
    peerDependencies:
      postcss: ^8.4

  '@csstools/postcss-oklab-function@4.0.12':
    resolution: {integrity: sha512-HhlSmnE1NKBhXsTnNGjxvhryKtO7tJd1w42DKOGFD6jSHtYOrsJTQDKPMwvOfrzUAk8t7GcpIfRyM7ssqHpFjg==}
    engines: {node: '>=18'}
    peerDependencies:
      postcss: ^8.4

  '@csstools/postcss-position-area-property@1.0.0':
    resolution: {integrity: sha512-fUP6KR8qV2NuUZV3Cw8itx0Ep90aRjAZxAEzC3vrl6yjFv+pFsQbR18UuQctEKmA72K9O27CoYiKEgXxkqjg8Q==}
    engines: {node: '>=18'}
    peerDependencies:
      postcss: ^8.4

  '@csstools/postcss-progressive-custom-properties@4.2.1':
    resolution: {integrity: sha512-uPiiXf7IEKtUQXsxu6uWtOlRMXd2QWWy5fhxHDnPdXKCQckPP3E34ZgDoZ62r2iT+UOgWsSbM4NvHE5m3mAEdw==}
    engines: {node: '>=18'}
    peerDependencies:
      postcss: ^8.4

  '@csstools/postcss-property-rule-prelude-list@1.0.0':
    resolution: {integrity: sha512-IxuQjUXq19fobgmSSvUDO7fVwijDJaZMvWQugxfEUxmjBeDCVaDuMpsZ31MsTm5xbnhA+ElDi0+rQ7sQQGisFA==}
    engines: {node: '>=18'}
    peerDependencies:
      postcss: ^8.4

  '@csstools/postcss-random-function@2.0.1':
    resolution: {integrity: sha512-q+FQaNiRBhnoSNo+GzqGOIBKoHQ43lYz0ICrV+UudfWnEF6ksS6DsBIJSISKQT2Bvu3g4k6r7t0zYrk5pDlo8w==}
    engines: {node: '>=18'}
    peerDependencies:
      postcss: ^8.4

  '@csstools/postcss-relative-color-syntax@3.0.12':
    resolution: {integrity: sha512-0RLIeONxu/mtxRtf3o41Lq2ghLimw0w9ByLWnnEVuy89exmEEq8bynveBxNW3nyHqLAFEeNtVEmC1QK9MZ8Huw==}
    engines: {node: '>=18'}
    peerDependencies:
      postcss: ^8.4

  '@csstools/postcss-scope-pseudo-class@4.0.1':
    resolution: {integrity: sha512-IMi9FwtH6LMNuLea1bjVMQAsUhFxJnyLSgOp/cpv5hrzWmrUYU5fm0EguNDIIOHUqzXode8F/1qkC/tEo/qN8Q==}
    engines: {node: '>=18'}
    peerDependencies:
      postcss: ^8.4

  '@csstools/postcss-sign-functions@1.1.4':
    resolution: {integrity: sha512-P97h1XqRPcfcJndFdG95Gv/6ZzxUBBISem0IDqPZ7WMvc/wlO+yU0c5D/OCpZ5TJoTt63Ok3knGk64N+o6L2Pg==}
    engines: {node: '>=18'}
    peerDependencies:
      postcss: ^8.4

  '@csstools/postcss-stepped-value-functions@4.0.9':
    resolution: {integrity: sha512-h9btycWrsex4dNLeQfyU3y3w40LMQooJWFMm/SK9lrKguHDcFl4VMkncKKoXi2z5rM9YGWbUQABI8BT2UydIcA==}
    engines: {node: '>=18'}
    peerDependencies:
      postcss: ^8.4

  '@csstools/postcss-syntax-descriptor-syntax-production@1.0.1':
    resolution: {integrity: sha512-GneqQWefjM//f4hJ/Kbox0C6f2T7+pi4/fqTqOFGTL3EjnvOReTqO1qUQ30CaUjkwjYq9qZ41hzarrAxCc4gow==}
    engines: {node: '>=18'}
    peerDependencies:
      postcss: ^8.4

  '@csstools/postcss-system-ui-font-family@1.0.0':
    resolution: {integrity: sha512-s3xdBvfWYfoPSBsikDXbuorcMG1nN1M6GdU0qBsGfcmNR0A/qhloQZpTxjA3Xsyrk1VJvwb2pOfiOT3at/DuIQ==}
    engines: {node: '>=18'}
    peerDependencies:
      postcss: ^8.4

  '@csstools/postcss-text-decoration-shorthand@4.0.3':
    resolution: {integrity: sha512-KSkGgZfx0kQjRIYnpsD7X2Om9BUXX/Kii77VBifQW9Ih929hK0KNjVngHDH0bFB9GmfWcR9vJYJJRvw/NQjkrA==}
    engines: {node: '>=18'}
    peerDependencies:
      postcss: ^8.4

  '@csstools/postcss-trigonometric-functions@4.0.9':
    resolution: {integrity: sha512-Hnh5zJUdpNrJqK9v1/E3BbrQhaDTj5YiX7P61TOvUhoDHnUmsNNxcDAgkQ32RrcWx9GVUvfUNPcUkn8R3vIX6A==}
    engines: {node: '>=18'}
    peerDependencies:
      postcss: ^8.4

  '@csstools/postcss-unset-value@4.0.0':
    resolution: {integrity: sha512-cBz3tOCI5Fw6NIFEwU3RiwK6mn3nKegjpJuzCndoGq3BZPkUjnsq7uQmIeMNeMbMk7YD2MfKcgCpZwX5jyXqCA==}
    engines: {node: '>=18'}
    peerDependencies:
      postcss: ^8.4

  '@csstools/selector-resolve-nested@3.1.0':
    resolution: {integrity: sha512-mf1LEW0tJLKfWyvn5KdDrhpxHyuxpbNwTIwOYLIvsTffeyOf85j5oIzfG0yosxDgx/sswlqBnESYUcQH0vgZ0g==}
    engines: {node: '>=18'}
    peerDependencies:
      postcss-selector-parser: ^7.0.0

  '@csstools/selector-specificity@5.0.0':
    resolution: {integrity: sha512-PCqQV3c4CoVm3kdPhyeZ07VmBRdH2EpMFA/pd9OASpOEC3aXNGoqPDAZ80D0cLpMBxnmk0+yNhGsEx31hq7Gtw==}
    engines: {node: '>=18'}
    peerDependencies:
      postcss-selector-parser: ^7.0.0

  '@csstools/utilities@2.0.0':
    resolution: {integrity: sha512-5VdOr0Z71u+Yp3ozOx8T11N703wIFGVRgOWbOZMKgglPJsWA54MRIoMNVMa7shUToIhx5J8vX4sOZgD2XiihiQ==}
    engines: {node: '>=18'}
    peerDependencies:
      postcss: ^8.4

  '@discoveryjs/json-ext@0.5.7':
    resolution: {integrity: sha512-dBVuXR082gk3jsFp7Rd/JI4kytwGHecnCoTtXFb7DB6CNHp4rg5k1bhg0nWdLGLnOV71lmDzGQaLMy8iPLY0pw==}
    engines: {node: '>=10.0.0'}

  '@docsearch/core@4.4.0':
    resolution: {integrity: sha512-kiwNo5KEndOnrf5Kq/e5+D9NBMCFgNsDoRpKQJ9o/xnSlheh6b8AXppMuuUVVdAUIhIfQFk/07VLjjk/fYyKmw==}
    peerDependencies:
      '@types/react': '>= 16.8.0 < 20.0.0'
      react: '>= 16.8.0 < 20.0.0'
      react-dom: '>= 16.8.0 < 20.0.0'
    peerDependenciesMeta:
      '@types/react':
        optional: true
      react:
        optional: true
      react-dom:
        optional: true

  '@docsearch/css@4.4.0':
    resolution: {integrity: sha512-e9vPgtih6fkawakmYo0Y6V4BKBmDV7Ykudn7ADWXUs5b6pmtBRwDbpSG/WiaUG63G28OkJDEnsMvgIAnZgGwYw==}

  '@docsearch/react@4.4.0':
    resolution: {integrity: sha512-z12zeg1mV7WD4Ag4pKSuGukETJLaucVFwszDXL/qLaEgRqxEaVacO9SR1qqnCXvZztlvz2rt7cMqryi/7sKfjA==}
    peerDependencies:
      '@types/react': '>= 16.8.0 < 20.0.0'
      react: '>= 16.8.0 < 20.0.0'
      react-dom: '>= 16.8.0 < 20.0.0'
      search-insights: '>= 1 < 3'
    peerDependenciesMeta:
      '@types/react':
        optional: true
      react:
        optional: true
      react-dom:
        optional: true
      search-insights:
        optional: true

  '@docusaurus/babel@3.9.2':
    resolution: {integrity: sha512-GEANdi/SgER+L7Japs25YiGil/AUDnFFHaCGPBbundxoWtCkA2lmy7/tFmgED4y1htAy6Oi4wkJEQdGssnw9MA==}
    engines: {node: '>=20.0'}

  '@docusaurus/bundler@3.9.2':
    resolution: {integrity: sha512-ZOVi6GYgTcsZcUzjblpzk3wH1Fya2VNpd5jtHoCCFcJlMQ1EYXZetfAnRHLcyiFeBABaI1ltTYbOBtH/gahGVA==}
    engines: {node: '>=20.0'}
    peerDependencies:
      '@docusaurus/faster': '*'
    peerDependenciesMeta:
      '@docusaurus/faster':
        optional: true

  '@docusaurus/core@3.9.2':
    resolution: {integrity: sha512-HbjwKeC+pHUFBfLMNzuSjqFE/58+rLVKmOU3lxQrpsxLBOGosYco/Q0GduBb0/jEMRiyEqjNT/01rRdOMWq5pw==}
    engines: {node: '>=20.0'}
    hasBin: true
    peerDependencies:
      '@mdx-js/react': ^3.0.0
      react: ^18.0.0 || ^19.0.0
      react-dom: ^18.0.0 || ^19.0.0

  '@docusaurus/cssnano-preset@3.9.2':
    resolution: {integrity: sha512-8gBKup94aGttRduABsj7bpPFTX7kbwu+xh3K9NMCF5K4bWBqTFYW+REKHF6iBVDHRJ4grZdIPbvkiHd/XNKRMQ==}
    engines: {node: '>=20.0'}

  '@docusaurus/logger@3.9.2':
    resolution: {integrity: sha512-/SVCc57ByARzGSU60c50rMyQlBuMIJCjcsJlkphxY6B0GV4UH3tcA1994N8fFfbJ9kX3jIBe/xg3XP5qBtGDbA==}
    engines: {node: '>=20.0'}

  '@docusaurus/mdx-loader@3.9.2':
    resolution: {integrity: sha512-wiYoGwF9gdd6rev62xDU8AAM8JuLI/hlwOtCzMmYcspEkzecKrP8J8X+KpYnTlACBUUtXNJpSoCwFWJhLRevzQ==}
    engines: {node: '>=20.0'}
    peerDependencies:
      react: ^18.0.0 || ^19.0.0
      react-dom: ^18.0.0 || ^19.0.0

  '@docusaurus/module-type-aliases@3.9.2':
    resolution: {integrity: sha512-8qVe2QA9hVLzvnxP46ysuofJUIc/yYQ82tvA/rBTrnpXtCjNSFLxEZfd5U8cYZuJIVlkPxamsIgwd5tGZXfvew==}
    peerDependencies:
      react: '*'
      react-dom: '*'

  '@docusaurus/plugin-content-blog@3.9.2':
    resolution: {integrity: sha512-3I2HXy3L1QcjLJLGAoTvoBnpOwa6DPUa3Q0dMK19UTY9mhPkKQg/DYhAGTiBUKcTR0f08iw7kLPqOhIgdV3eVQ==}
    engines: {node: '>=20.0'}
    peerDependencies:
      '@docusaurus/plugin-content-docs': '*'
      react: ^18.0.0 || ^19.0.0
      react-dom: ^18.0.0 || ^19.0.0

  '@docusaurus/plugin-content-docs@3.9.2':
    resolution: {integrity: sha512-C5wZsGuKTY8jEYsqdxhhFOe1ZDjH0uIYJ9T/jebHwkyxqnr4wW0jTkB72OMqNjsoQRcb0JN3PcSeTwFlVgzCZg==}
    engines: {node: '>=20.0'}
    peerDependencies:
      react: ^18.0.0 || ^19.0.0
      react-dom: ^18.0.0 || ^19.0.0

  '@docusaurus/plugin-content-pages@3.9.2':
    resolution: {integrity: sha512-s4849w/p4noXUrGpPUF0BPqIAfdAe76BLaRGAGKZ1gTDNiGxGcpsLcwJ9OTi1/V8A+AzvsmI9pkjie2zjIQZKA==}
    engines: {node: '>=20.0'}
    peerDependencies:
      react: ^18.0.0 || ^19.0.0
      react-dom: ^18.0.0 || ^19.0.0

  '@docusaurus/plugin-css-cascade-layers@3.9.2':
    resolution: {integrity: sha512-w1s3+Ss+eOQbscGM4cfIFBlVg/QKxyYgj26k5AnakuHkKxH6004ZtuLe5awMBotIYF2bbGDoDhpgQ4r/kcj4rQ==}
    engines: {node: '>=20.0'}

  '@docusaurus/plugin-debug@3.9.2':
    resolution: {integrity: sha512-j7a5hWuAFxyQAkilZwhsQ/b3T7FfHZ+0dub6j/GxKNFJp2h9qk/P1Bp7vrGASnvA9KNQBBL1ZXTe7jlh4VdPdA==}
    engines: {node: '>=20.0'}
    peerDependencies:
      react: ^18.0.0 || ^19.0.0
      react-dom: ^18.0.0 || ^19.0.0

  '@docusaurus/plugin-google-analytics@3.9.2':
    resolution: {integrity: sha512-mAwwQJ1Us9jL/lVjXtErXto4p4/iaLlweC54yDUK1a97WfkC6Z2k5/769JsFgwOwOP+n5mUQGACXOEQ0XDuVUw==}
    engines: {node: '>=20.0'}
    peerDependencies:
      react: ^18.0.0 || ^19.0.0
      react-dom: ^18.0.0 || ^19.0.0

  '@docusaurus/plugin-google-gtag@3.9.2':
    resolution: {integrity: sha512-YJ4lDCphabBtw19ooSlc1MnxtYGpjFV9rEdzjLsUnBCeis2djUyCozZaFhCg6NGEwOn7HDDyMh0yzcdRpnuIvA==}
    engines: {node: '>=20.0'}
    peerDependencies:
      react: ^18.0.0 || ^19.0.0
      react-dom: ^18.0.0 || ^19.0.0

  '@docusaurus/plugin-google-tag-manager@3.9.2':
    resolution: {integrity: sha512-LJtIrkZN/tuHD8NqDAW1Tnw0ekOwRTfobWPsdO15YxcicBo2ykKF0/D6n0vVBfd3srwr9Z6rzrIWYrMzBGrvNw==}
    engines: {node: '>=20.0'}
    peerDependencies:
      react: ^18.0.0 || ^19.0.0
      react-dom: ^18.0.0 || ^19.0.0

  '@docusaurus/plugin-sitemap@3.9.2':
    resolution: {integrity: sha512-WLh7ymgDXjG8oPoM/T4/zUP7KcSuFYRZAUTl8vR6VzYkfc18GBM4xLhcT+AKOwun6kBivYKUJf+vlqYJkm+RHw==}
    engines: {node: '>=20.0'}
    peerDependencies:
      react: ^18.0.0 || ^19.0.0
      react-dom: ^18.0.0 || ^19.0.0

  '@docusaurus/plugin-svgr@3.9.2':
    resolution: {integrity: sha512-n+1DE+5b3Lnf27TgVU5jM1d4x5tUh2oW5LTsBxJX4PsAPV0JGcmI6p3yLYtEY0LRVEIJh+8RsdQmRE66wSV8mw==}
    engines: {node: '>=20.0'}
    peerDependencies:
      react: ^18.0.0 || ^19.0.0
      react-dom: ^18.0.0 || ^19.0.0

  '@docusaurus/preset-classic@3.9.2':
    resolution: {integrity: sha512-IgyYO2Gvaigi21LuDIe+nvmN/dfGXAiMcV/murFqcpjnZc7jxFAxW+9LEjdPt61uZLxG4ByW/oUmX/DDK9t/8w==}
    engines: {node: '>=20.0'}
    peerDependencies:
      react: ^18.0.0 || ^19.0.0
      react-dom: ^18.0.0 || ^19.0.0

  '@docusaurus/react-loadable@6.0.0':
    resolution: {integrity: sha512-YMMxTUQV/QFSnbgrP3tjDzLHRg7vsbMn8e9HAa8o/1iXoiomo48b7sk/kkmWEuWNDPJVlKSJRB6Y2fHqdJk+SQ==}
    peerDependencies:
      react: '*'

  '@docusaurus/theme-classic@3.9.2':
    resolution: {integrity: sha512-IGUsArG5hhekXd7RDb11v94ycpJpFdJPkLnt10fFQWOVxAtq5/D7hT6lzc2fhyQKaaCE62qVajOMKL7OiAFAIA==}
    engines: {node: '>=20.0'}
    peerDependencies:
      react: ^18.0.0 || ^19.0.0
      react-dom: ^18.0.0 || ^19.0.0

  '@docusaurus/theme-common@3.9.2':
    resolution: {integrity: sha512-6c4DAbR6n6nPbnZhY2V3tzpnKnGL+6aOsLvFL26VRqhlczli9eWG0VDUNoCQEPnGwDMhPS42UhSAnz5pThm5Ag==}
    engines: {node: '>=20.0'}
    peerDependencies:
      '@docusaurus/plugin-content-docs': '*'
      react: ^18.0.0 || ^19.0.0
      react-dom: ^18.0.0 || ^19.0.0

  '@docusaurus/theme-mermaid@3.9.2':
    resolution: {integrity: sha512-5vhShRDq/ntLzdInsQkTdoKWSzw8d1jB17sNPYhA/KvYYFXfuVEGHLM6nrf8MFbV8TruAHDG21Fn3W4lO8GaDw==}
    engines: {node: '>=20.0'}
    peerDependencies:
      '@mermaid-js/layout-elk': ^0.1.9
      react: ^18.0.0 || ^19.0.0
      react-dom: ^18.0.0 || ^19.0.0
    peerDependenciesMeta:
      '@mermaid-js/layout-elk':
        optional: true

  '@docusaurus/theme-search-algolia@3.9.2':
    resolution: {integrity: sha512-GBDSFNwjnh5/LdkxCKQHkgO2pIMX1447BxYUBG2wBiajS21uj64a+gH/qlbQjDLxmGrbrllBrtJkUHxIsiwRnw==}
    engines: {node: '>=20.0'}
    peerDependencies:
      react: ^18.0.0 || ^19.0.0
      react-dom: ^18.0.0 || ^19.0.0

  '@docusaurus/theme-translations@3.9.2':
    resolution: {integrity: sha512-vIryvpP18ON9T9rjgMRFLr2xJVDpw1rtagEGf8Ccce4CkTrvM/fRB8N2nyWYOW5u3DdjkwKw5fBa+3tbn9P4PA==}
    engines: {node: '>=20.0'}

  '@docusaurus/types@3.9.2':
    resolution: {integrity: sha512-Ux1JUNswg+EfUEmajJjyhIohKceitY/yzjRUpu04WXgvVz+fbhVC0p+R0JhvEu4ytw8zIAys2hrdpQPBHRIa8Q==}
    peerDependencies:
      react: ^18.0.0 || ^19.0.0
      react-dom: ^18.0.0 || ^19.0.0

  '@docusaurus/utils-common@3.9.2':
    resolution: {integrity: sha512-I53UC1QctruA6SWLvbjbhCpAw7+X7PePoe5pYcwTOEXD/PxeP8LnECAhTHHwWCblyUX5bMi4QLRkxvyZ+IT8Aw==}
    engines: {node: '>=20.0'}

  '@docusaurus/utils-validation@3.9.2':
    resolution: {integrity: sha512-l7yk3X5VnNmATbwijJkexdhulNsQaNDwoagiwujXoxFbWLcxHQqNQ+c/IAlzrfMMOfa/8xSBZ7KEKDesE/2J7A==}
    engines: {node: '>=20.0'}

  '@docusaurus/utils@3.9.2':
    resolution: {integrity: sha512-lBSBiRruFurFKXr5Hbsl2thmGweAPmddhF3jb99U4EMDA5L+e5Y1rAkOS07Nvrup7HUMBDrCV45meaxZnt28nQ==}
    engines: {node: '>=20.0'}

  '@eslint-community/eslint-utils@4.9.1':
    resolution: {integrity: sha512-phrYmNiYppR7znFEdqgfWHXR6NCkZEK7hwWDHZUjit/2/U0r6XvkDl0SYnoM51Hq7FhCGdLDT6zxCCOY1hexsQ==}
    engines: {node: ^12.22.0 || ^14.17.0 || >=16.0.0}
    peerDependencies:
      eslint: ^6.0.0 || ^7.0.0 || >=8.0.0

  '@eslint-community/regexpp@4.12.2':
    resolution: {integrity: sha512-EriSTlt5OC9/7SXkRSCAhfSxxoSUgBm33OH+IkwbdpgoqsSsUg7y3uh+IICI/Qg4BBWr3U2i39RpmycbxMq4ew==}
    engines: {node: ^12.0.0 || ^14.0.0 || >=16.0.0}

  '@eslint/config-array@0.21.1':
    resolution: {integrity: sha512-aw1gNayWpdI/jSYVgzN5pL0cfzU02GT3NBpeT/DXbx1/1x7ZKxFPd9bwrzygx/qiwIQiJ1sw/zD8qY/kRvlGHA==}
    engines: {node: ^18.18.0 || ^20.9.0 || >=21.1.0}

  '@eslint/config-helpers@0.4.2':
    resolution: {integrity: sha512-gBrxN88gOIf3R7ja5K9slwNayVcZgK6SOUORm2uBzTeIEfeVaIhOpCtTox3P6R7o2jLFwLFTLnC7kU/RGcYEgw==}
    engines: {node: ^18.18.0 || ^20.9.0 || >=21.1.0}

  '@eslint/core@0.17.0':
    resolution: {integrity: sha512-yL/sLrpmtDaFEiUj1osRP4TI2MDz1AddJL+jZ7KSqvBuliN4xqYY54IfdN8qD8Toa6g1iloph1fxQNkjOxrrpQ==}
    engines: {node: ^18.18.0 || ^20.9.0 || >=21.1.0}

  '@eslint/eslintrc@3.3.3':
    resolution: {integrity: sha512-Kr+LPIUVKz2qkx1HAMH8q1q6azbqBAsXJUxBl/ODDuVPX45Z9DfwB8tPjTi6nNZ8BuM3nbJxC5zCAg5elnBUTQ==}
    engines: {node: ^18.18.0 || ^20.9.0 || >=21.1.0}

  '@eslint/js@9.39.2':
    resolution: {integrity: sha512-q1mjIoW1VX4IvSocvM/vbTiveKC4k9eLrajNEuSsmjymSDEbpGddtpfOoN7YGAqBK3NG+uqo8ia4PDTt8buCYA==}
    engines: {node: ^18.18.0 || ^20.9.0 || >=21.1.0}

  '@eslint/object-schema@2.1.7':
    resolution: {integrity: sha512-VtAOaymWVfZcmZbp6E2mympDIHvyjXs/12LqWYjVw6qjrfF+VK+fyG33kChz3nnK+SU5/NeHOqrTEHS8sXO3OA==}
    engines: {node: ^18.18.0 || ^20.9.0 || >=21.1.0}

  '@eslint/plugin-kit@0.4.1':
    resolution: {integrity: sha512-43/qtrDUokr7LJqoF2c3+RInu/t4zfrpYdoSDfYyhg52rwLV6TnOvdG4fXm7IkSB3wErkcmJS9iEhjVtOSEjjA==}
    engines: {node: ^18.18.0 || ^20.9.0 || >=21.1.0}

  '@hapi/hoek@9.3.0':
    resolution: {integrity: sha512-/c6rf4UJlmHlC9b5BaNvzAcFv7HZ2QHaV0D4/HNlBdvFnvQq8RI4kYdhyPCl7Xj+oWvTWQ8ujhqS53LIgAe6KQ==}

  '@hapi/topo@5.1.0':
    resolution: {integrity: sha512-foQZKJig7Ob0BMAYBfcJk8d77QtOe7Wo4ox7ff1lQYoNNAb6jwcY1ncdoy2e9wQZzvNy7ODZCYJkK8kzmcAnAg==}

  '@humanfs/core@0.19.1':
    resolution: {integrity: sha512-5DyQ4+1JEUzejeK1JGICcideyfUbGixgS9jNgex5nqkW+cY7WZhxBigmieN5Qnw9ZosSNVC9KQKyb+GUaGyKUA==}
    engines: {node: '>=18.18.0'}

  '@humanfs/node@0.16.7':
    resolution: {integrity: sha512-/zUx+yOsIrG4Y43Eh2peDeKCxlRt/gET6aHfaKpuq267qXdYDFViVHfMaLyygZOnl0kGWxFIgsBy8QFuTLUXEQ==}
    engines: {node: '>=18.18.0'}

  '@humanwhocodes/module-importer@1.0.1':
    resolution: {integrity: sha512-bxveV4V8v5Yb4ncFTT3rPSgZBOpCkjfK0y4oVVVJwIuDVBRMDXrPyXRL988i5ap9m9bnyEEjWfm5WkBmtffLfA==}
    engines: {node: '>=12.22'}

  '@humanwhocodes/retry@0.4.3':
    resolution: {integrity: sha512-bV0Tgo9K4hfPCek+aMAn81RppFKv2ySDQeMoSZuvTASywNTnVJCArCZE2FWqpvIatKu7VMRLWlR1EazvVhDyhQ==}
    engines: {node: '>=18.18'}

  '@iconify/types@2.0.0':
    resolution: {integrity: sha512-+wluvCrRhXrhyOmRDJ3q8mux9JkKy5SJ/v8ol2tu4FVjyYvtEzkc/3pK15ET6RKg4b4w4BmTk1+gsCUhf21Ykg==}

  '@iconify/utils@3.1.0':
    resolution: {integrity: sha512-Zlzem1ZXhI1iHeeERabLNzBHdOa4VhQbqAcOQaMKuTuyZCpwKbC2R4Dd0Zo3g9EAc+Y4fiarO8HIHRAth7+skw==}

  '@jest/schemas@29.6.3':
    resolution: {integrity: sha512-mo5j5X+jIZmJQveBKeS/clAueipV7KgiX1vMgCxam1RNYiqE1w62n0/tJJnHtjW8ZHcQco5gY85jA3mi0L+nSA==}
    engines: {node: ^14.15.0 || ^16.10.0 || >=18.0.0}

  '@jest/types@29.6.3':
    resolution: {integrity: sha512-u3UPsIilWKOM3F9CXtrG8LEJmNxwoCQC/XVj4IKYXvvpx7QIi/Kg1LI5uDmDpKlac62NUtX7eLjRh+jVZcLOzw==}
    engines: {node: ^14.15.0 || ^16.10.0 || >=18.0.0}

  '@jridgewell/gen-mapping@0.3.13':
    resolution: {integrity: sha512-2kkt/7niJ6MgEPxF0bYdQ6etZaA+fQvDcLKckhy1yIQOzaoKjBBjSj63/aLVjYE3qhRt5dvM+uUyfCg6UKCBbA==}

  '@jridgewell/remapping@2.3.5':
    resolution: {integrity: sha512-LI9u/+laYG4Ds1TDKSJW2YPrIlcVYOwi2fUC6xB43lueCjgxV4lffOCZCtYFiH6TNOX+tQKXx97T4IKHbhyHEQ==}

  '@jridgewell/resolve-uri@3.1.2':
    resolution: {integrity: sha512-bRISgCIjP20/tbWSPWMEi54QVPRZExkuD9lJL+UIxUKtwVJA8wW1Trb1jMs1RFXo1CBTNZ/5hpC9QvmKWdopKw==}
    engines: {node: '>=6.0.0'}

  '@jridgewell/source-map@0.3.11':
    resolution: {integrity: sha512-ZMp1V8ZFcPG5dIWnQLr3NSI1MiCU7UETdS/A0G8V/XWHvJv3ZsFqutJn1Y5RPmAPX6F3BiE397OqveU/9NCuIA==}

  '@jridgewell/sourcemap-codec@1.5.5':
    resolution: {integrity: sha512-cYQ9310grqxueWbl+WuIUIaiUaDcj7WOq5fVhEljNVgRfOUhY9fy2zTvfoqWsnebh8Sl70VScFbICvJnLKB0Og==}

  '@jridgewell/trace-mapping@0.3.31':
    resolution: {integrity: sha512-zzNR+SdQSDJzc8joaeP8QQoCQr8NuYx2dIIytl1QeBEZHJ9uW6hebsrYgbz8hJwUQao3TWCMtmfV8Nu1twOLAw==}

  '@jsonjoy.com/base64@1.1.2':
    resolution: {integrity: sha512-q6XAnWQDIMA3+FTiOYajoYqySkO+JSat0ytXGSuRdq9uXE7o92gzuQwQM14xaCRlBLGq3v5miDGC4vkVTn54xA==}
    engines: {node: '>=10.0'}
    peerDependencies:
      tslib: '2'

  '@jsonjoy.com/buffers@1.2.1':
    resolution: {integrity: sha512-12cdlDwX4RUM3QxmUbVJWqZ/mrK6dFQH4Zxq6+r1YXKXYBNgZXndx2qbCJwh3+WWkCSn67IjnlG3XYTvmvYtgA==}
    engines: {node: '>=10.0'}
    peerDependencies:
      tslib: '2'

  '@jsonjoy.com/codegen@1.0.0':
    resolution: {integrity: sha512-E8Oy+08cmCf0EK/NMxpaJZmOxPqM+6iSe2S4nlSBrPZOORoDJILxtbSUEDKQyTamm/BVAhIGllOBNU79/dwf0g==}
    engines: {node: '>=10.0'}
    peerDependencies:
      tslib: '2'

  '@jsonjoy.com/json-pack@1.21.0':
    resolution: {integrity: sha512-+AKG+R2cfZMShzrF2uQw34v3zbeDYUqnQ+jg7ORic3BGtfw9p/+N6RJbq/kkV8JmYZaINknaEQ2m0/f693ZPpg==}
    engines: {node: '>=10.0'}
    peerDependencies:
      tslib: '2'

  '@jsonjoy.com/json-pointer@1.0.2':
    resolution: {integrity: sha512-Fsn6wM2zlDzY1U+v4Nc8bo3bVqgfNTGcn6dMgs6FjrEnt4ZCe60o6ByKRjOGlI2gow0aE/Q41QOigdTqkyK5fg==}
    engines: {node: '>=10.0'}
    peerDependencies:
      tslib: '2'

  '@jsonjoy.com/util@1.9.0':
    resolution: {integrity: sha512-pLuQo+VPRnN8hfPqUTLTHk126wuYdXVxE6aDmjSeV4NCAgyxWbiOIeNJVtID3h1Vzpoi9m4jXezf73I6LgabgQ==}
    engines: {node: '>=10.0'}
    peerDependencies:
      tslib: '2'

  '@leichtgewicht/ip-codec@2.0.5':
    resolution: {integrity: sha512-Vo+PSpZG2/fmgmiNzYK9qWRh8h/CHrwD0mo1h1DzL4yzHNSfWYujGTYsWGreD000gcgmZ7K4Ys6Tx9TxtsKdDw==}

  '@mdx-js/mdx@3.1.1':
    resolution: {integrity: sha512-f6ZO2ifpwAQIpzGWaBQT2TXxPv6z3RBzQKpVftEWN78Vl/YweF1uwussDx8ECAXVtr3Rs89fKyG9YlzUs9DyGQ==}

  '@mdx-js/react@3.1.1':
    resolution: {integrity: sha512-f++rKLQgUVYDAtECQ6fn/is15GkEH9+nZPM3MS0RcxVqoTfawHvDlSCH7JbMhAM6uJ32v3eXLvLmLvjGu7PTQw==}
    peerDependencies:
      '@types/react': '>=16'
      react: '>=16'

  '@mermaid-js/parser@0.6.3':
    resolution: {integrity: sha512-lnjOhe7zyHjc+If7yT4zoedx2vo4sHaTmtkl1+or8BRTnCtDmcTpAjpzDSfCZrshM5bCoz0GyidzadJAH1xobA==}

  '@noble/hashes@1.4.0':
    resolution: {integrity: sha512-V1JJ1WTRUqHHrOSh597hURcMqVKVGL/ea3kv0gSnEdsEZ0/+VyPghM1lMNGc00z7CIQorSvbKpuJkxvuHbvdbg==}
    engines: {node: '>= 16'}

  '@nodelib/fs.scandir@2.1.5':
    resolution: {integrity: sha512-vq24Bq3ym5HEQm2NKCr3yXDwjc7vTsEThRDnkp2DK9p1uqLR+DHurm/NOTo0KG7HYHU7eppKZj3MyqYuMBf62g==}
    engines: {node: '>= 8'}

  '@nodelib/fs.stat@2.0.5':
    resolution: {integrity: sha512-RkhPPp2zrqDAQA/2jNhnztcPAlv64XdhIp7a7454A5ovI7Bukxgt7MX7udwAu3zg1DcpPU0rz3VV1SeaqvY4+A==}
    engines: {node: '>= 8'}

  '@nodelib/fs.walk@1.2.8':
    resolution: {integrity: sha512-oGB+UxlgWcgQkgwo8GcEGwemoTFt3FIO9ababBmaGwXIoBKZ+GTy0pP185beGg7Llih/NSHSV2XAs1lnznocSg==}
    engines: {node: '>= 8'}

  '@opentelemetry/api@1.9.0':
    resolution: {integrity: sha512-3giAOQvZiH5F9bMlMiv8+GSPMeqg0dbaeo58/0SlA9sxSqZhnUtxzX9/2FzyhS9sWQf5S0GJE0AKBrFqjpeYcg==}
    engines: {node: '>=8.0.0'}

  '@peculiar/asn1-cms@2.6.0':
    resolution: {integrity: sha512-2uZqP+ggSncESeUF/9Su8rWqGclEfEiz1SyU02WX5fUONFfkjzS2Z/F1Li0ofSmf4JqYXIOdCAZqIXAIBAT1OA==}

  '@peculiar/asn1-csr@2.6.0':
    resolution: {integrity: sha512-BeWIu5VpTIhfRysfEp73SGbwjjoLL/JWXhJ/9mo4vXnz3tRGm+NGm3KNcRzQ9VMVqwYS2RHlolz21svzRXIHPQ==}

  '@peculiar/asn1-ecc@2.6.0':
    resolution: {integrity: sha512-FF3LMGq6SfAOwUG2sKpPXblibn6XnEIKa+SryvUl5Pik+WR9rmRA3OCiwz8R3lVXnYnyRkSZsSLdml8H3UiOcw==}

  '@peculiar/asn1-pfx@2.6.0':
    resolution: {integrity: sha512-rtUvtf+tyKGgokHHmZzeUojRZJYPxoD/jaN1+VAB4kKR7tXrnDCA/RAWXAIhMJJC+7W27IIRGe9djvxKgsldCQ==}

  '@peculiar/asn1-pkcs8@2.6.0':
    resolution: {integrity: sha512-KyQ4D8G/NrS7Fw3XCJrngxmjwO/3htnA0lL9gDICvEQ+GJ+EPFqldcJQTwPIdvx98Tua+WjkdKHSC0/Km7T+lA==}

  '@peculiar/asn1-pkcs9@2.6.0':
    resolution: {integrity: sha512-b78OQ6OciW0aqZxdzliXGYHASeCvvw5caqidbpQRYW2mBtXIX2WhofNXTEe7NyxTb0P6J62kAAWLwn0HuMF1Fw==}

  '@peculiar/asn1-rsa@2.6.0':
    resolution: {integrity: sha512-Nu4C19tsrTsCp9fDrH+sdcOKoVfdfoQQ7S3VqjJU6vedR7tY3RLkQ5oguOIB3zFW33USDUuYZnPEQYySlgha4w==}

  '@peculiar/asn1-schema@2.6.0':
    resolution: {integrity: sha512-xNLYLBFTBKkCzEZIw842BxytQQATQv+lDTCEMZ8C196iJcJJMBUZxrhSTxLaohMyKK8QlzRNTRkUmanucnDSqg==}

  '@peculiar/asn1-x509-attr@2.6.0':
    resolution: {integrity: sha512-MuIAXFX3/dc8gmoZBkwJWxUWOSvG4MMDntXhrOZpJVMkYX+MYc/rUAU2uJOved9iJEoiUx7//3D8oG83a78UJA==}

  '@peculiar/asn1-x509@2.6.0':
    resolution: {integrity: sha512-uzYbPEpoQiBoTq0/+jZtpM6Gq6zADBx+JNFP3yqRgziWBxQ/Dt/HcuvRfm9zJTPdRcBqPNdaRHTVwpyiq6iNMA==}

  '@peculiar/x509@1.14.3':
    resolution: {integrity: sha512-C2Xj8FZ0uHWeCXXqX5B4/gVFQmtSkiuOolzAgutjTfseNOHT3pUjljDZsTSxXFGgio54bCzVFqmEOUrIVk8RDA==}
    engines: {node: '>=20.0.0'}

  '@pkgr/core@0.2.9':
    resolution: {integrity: sha512-QNqXyfVS2wm9hweSYD2O7F0G06uurj9kZ96TRQE5Y9hU7+tgdZwIkbAKc5Ocy1HxEY2kuDQa6cQ1WRs/O5LFKA==}
    engines: {node: ^12.20.0 || ^14.18.0 || >=16.0.0}

  '@pnpm/config.env-replace@1.1.0':
    resolution: {integrity: sha512-htyl8TWnKL7K/ESFa1oW2UB5lVDxuF5DpM7tBi6Hu2LNL3mWkIzNLG6N4zoCUP1lCKNxWy/3iu8mS8MvToGd6w==}
    engines: {node: '>=12.22.0'}

  '@pnpm/network.ca-file@1.0.2':
    resolution: {integrity: sha512-YcPQ8a0jwYU9bTdJDpXjMi7Brhkr1mXsXrUJvjqM2mQDgkRiz8jFaQGOdaLxgjtUfQgZhKy/O3cG/YwmgKaxLA==}
    engines: {node: '>=12.22.0'}

  '@pnpm/npm-conf@2.3.1':
    resolution: {integrity: sha512-c83qWb22rNRuB0UaVCI0uRPNRr8Z0FWnEIvT47jiHAmOIUHbBOg5XvV7pM5x+rKn9HRpjxquDbXYSXr3fAKFcw==}
    engines: {node: '>=12'}

  '@polka/url@1.0.0-next.29':
    resolution: {integrity: sha512-wwQAWhWSuHaag8c4q/KN/vCoeOJYshAIvMQwD4GpSb3OiZklFfvAgmj0VCBBImRpuF/aFgIRzllXlVX93Jevww==}

  '@sideway/address@4.1.5':
    resolution: {integrity: sha512-IqO/DUQHUkPeixNQ8n0JA6102hT9CmaljNTPmQ1u8MEhBo/R4Q8eKLN/vGZxuebwOroDB4cbpjheD4+/sKFK4Q==}

  '@sideway/formula@3.0.1':
    resolution: {integrity: sha512-/poHZJJVjx3L+zVD6g9KgHfYnb443oi7wLu/XKojDviHy6HOEOA6z1Trk5aR1dGcmPenJEgb2sK2I80LeS3MIg==}

  '@sideway/pinpoint@2.0.0':
    resolution: {integrity: sha512-RNiOoTPkptFtSVzQevY/yWtZwf/RxyVnPy/OcA9HBM3MlGDnBEYL5B41H0MTn0Uec8Hi+2qUtTfG2WWZBmMejQ==}

  '@sinclair/typebox@0.27.8':
    resolution: {integrity: sha512-+Fj43pSMwJs4KRrH/938Uf+uAELIgVBmQzg/q1YG10djyfA3TnrU8N8XzqCh/okZdszqBQTZf96idMfE5lnwTA==}

  '@sindresorhus/is@4.6.0':
    resolution: {integrity: sha512-t09vSN3MdfsyCHoFcTRCH/iUtG7OJ0CsjzB8cjAmKc/va/kIgeDI/TxsigdncE/4be734m0cvIYwNaV4i2XqAw==}
    engines: {node: '>=10'}

  '@sindresorhus/is@5.6.0':
    resolution: {integrity: sha512-TV7t8GKYaJWsn00tFDqBw8+Uqmr8A0fRU1tvTQhyZzGv0sJCGRQL3JGMI3ucuKo3XIZdUP+Lx7/gh2t3lewy7g==}
    engines: {node: '>=14.16'}

  '@slorber/react-helmet-async@1.3.0':
    resolution: {integrity: sha512-e9/OK8VhwUSc67diWI8Rb3I0YgI9/SBQtnhe9aEuK6MhZm7ntZZimXgwXnd8W96YTmSOb9M4d8LwhRZyhWr/1A==}
    peerDependencies:
      react: ^16.6.0 || ^17.0.0 || ^18.0.0 || ^19.0.0
      react-dom: ^16.6.0 || ^17.0.0 || ^18.0.0 || ^19.0.0

  '@slorber/remark-comment@1.0.0':
    resolution: {integrity: sha512-RCE24n7jsOj1M0UPvIQCHTe7fI0sFL4S2nwKVWwHyVr/wI/H8GosgsJGyhnsZoGFnD/P2hLf1mSbrrgSLN93NA==}

  '@standard-schema/spec@1.1.0':
    resolution: {integrity: sha512-l2aFy5jALhniG5HgqrD6jXLi/rUWrKvqN/qJx6yoJsgKhblVd+iqqU4RCXavm/jPityDo5TCvKMnpjKnOriy0w==}

  '@svgr/babel-plugin-add-jsx-attribute@8.0.0':
    resolution: {integrity: sha512-b9MIk7yhdS1pMCZM8VeNfUlSKVRhsHZNMl5O9SfaX0l0t5wjdgu4IDzGB8bpnGBBOjGST3rRFVsaaEtI4W6f7g==}
    engines: {node: '>=14'}
    peerDependencies:
      '@babel/core': ^7.0.0-0

  '@svgr/babel-plugin-remove-jsx-attribute@8.0.0':
    resolution: {integrity: sha512-BcCkm/STipKvbCl6b7QFrMh/vx00vIP63k2eM66MfHJzPr6O2U0jYEViXkHJWqXqQYjdeA9cuCl5KWmlwjDvbA==}
    engines: {node: '>=14'}
    peerDependencies:
      '@babel/core': ^7.0.0-0

  '@svgr/babel-plugin-remove-jsx-empty-expression@8.0.0':
    resolution: {integrity: sha512-5BcGCBfBxB5+XSDSWnhTThfI9jcO5f0Ai2V24gZpG+wXF14BzwxxdDb4g6trdOux0rhibGs385BeFMSmxtS3uA==}
    engines: {node: '>=14'}
    peerDependencies:
      '@babel/core': ^7.0.0-0

  '@svgr/babel-plugin-replace-jsx-attribute-value@8.0.0':
    resolution: {integrity: sha512-KVQ+PtIjb1BuYT3ht8M5KbzWBhdAjjUPdlMtpuw/VjT8coTrItWX6Qafl9+ji831JaJcu6PJNKCV0bp01lBNzQ==}
    engines: {node: '>=14'}
    peerDependencies:
      '@babel/core': ^7.0.0-0

  '@svgr/babel-plugin-svg-dynamic-title@8.0.0':
    resolution: {integrity: sha512-omNiKqwjNmOQJ2v6ge4SErBbkooV2aAWwaPFs2vUY7p7GhVkzRkJ00kILXQvRhA6miHnNpXv7MRnnSjdRjK8og==}
    engines: {node: '>=14'}
    peerDependencies:
      '@babel/core': ^7.0.0-0

  '@svgr/babel-plugin-svg-em-dimensions@8.0.0':
    resolution: {integrity: sha512-mURHYnu6Iw3UBTbhGwE/vsngtCIbHE43xCRK7kCw4t01xyGqb2Pd+WXekRRoFOBIY29ZoOhUCTEweDMdrjfi9g==}
    engines: {node: '>=14'}
    peerDependencies:
      '@babel/core': ^7.0.0-0

  '@svgr/babel-plugin-transform-react-native-svg@8.1.0':
    resolution: {integrity: sha512-Tx8T58CHo+7nwJ+EhUwx3LfdNSG9R2OKfaIXXs5soiy5HtgoAEkDay9LIimLOcG8dJQH1wPZp/cnAv6S9CrR1Q==}
    engines: {node: '>=14'}
    peerDependencies:
      '@babel/core': ^7.0.0-0

  '@svgr/babel-plugin-transform-svg-component@8.0.0':
    resolution: {integrity: sha512-DFx8xa3cZXTdb/k3kfPeaixecQLgKh5NVBMwD0AQxOzcZawK4oo1Jh9LbrcACUivsCA7TLG8eeWgrDXjTMhRmw==}
    engines: {node: '>=12'}
    peerDependencies:
      '@babel/core': ^7.0.0-0

  '@svgr/babel-preset@8.1.0':
    resolution: {integrity: sha512-7EYDbHE7MxHpv4sxvnVPngw5fuR6pw79SkcrILHJ/iMpuKySNCl5W1qcwPEpU+LgyRXOaAFgH0KhwD18wwg6ug==}
    engines: {node: '>=14'}
    peerDependencies:
      '@babel/core': ^7.0.0-0

  '@svgr/core@8.1.0':
    resolution: {integrity: sha512-8QqtOQT5ACVlmsvKOJNEaWmRPmcojMOzCz4Hs2BGG/toAp/K38LcsMRyLp349glq5AzJbCEeimEoxaX6v/fLrA==}
    engines: {node: '>=14'}

  '@svgr/hast-util-to-babel-ast@8.0.0':
    resolution: {integrity: sha512-EbDKwO9GpfWP4jN9sGdYwPBU0kdomaPIL2Eu4YwmgP+sJeXT+L7bMwJUBnhzfH8Q2qMBqZ4fJwpCyYsAN3mt2Q==}
    engines: {node: '>=14'}

  '@svgr/plugin-jsx@8.1.0':
    resolution: {integrity: sha512-0xiIyBsLlr8quN+WyuxooNW9RJ0Dpr8uOnH/xrCVO8GLUcwHISwj1AG0k+LFzteTkAA0GbX0kj9q6Dk70PTiPA==}
    engines: {node: '>=14'}
    peerDependencies:
      '@svgr/core': '*'

  '@svgr/plugin-svgo@8.1.0':
    resolution: {integrity: sha512-Ywtl837OGO9pTLIN/onoWLmDQ4zFUycI1g76vuKGEz6evR/ZTJlJuz3G/fIkb6OVBJ2g0o6CGJzaEjfmEo3AHA==}
    engines: {node: '>=14'}
    peerDependencies:
      '@svgr/core': '*'

  '@svgr/webpack@8.1.0':
    resolution: {integrity: sha512-LnhVjMWyMQV9ZmeEy26maJk+8HTIbd59cH4F2MJ439k9DqejRisfFNGAPvRYlKETuh9LrImlS8aKsBgKjMA8WA==}
    engines: {node: '>=14'}

  '@szmarczak/http-timer@5.0.1':
    resolution: {integrity: sha512-+PmQX0PiAYPMeVYe237LJAYvOMYW1j2rH5YROyS3b4CTVJum34HfRvKvAzozHAQG0TnHNdUfY9nCeUyRAs//cw==}
    engines: {node: '>=14.16'}

  '@trysound/sax@0.2.0':
    resolution: {integrity: sha512-L7z9BgrNEcYyUYtF+HaEfiS5ebkh9jXqbszz7pC0hRBPaatV0XjSD3+eHrpqFemQfgwiFF0QPIarnIihIDn7OA==}
    engines: {node: '>=10.13.0'}

  '@types/body-parser@1.19.6':
    resolution: {integrity: sha512-HLFeCYgz89uk22N5Qg3dvGvsv46B8GLvKKo1zKG4NybA8U2DiEO3w9lqGg29t/tfLRJpJ6iQxnVw4OnB7MoM9g==}

  '@types/bonjour@3.5.13':
    resolution: {integrity: sha512-z9fJ5Im06zvUL548KvYNecEVlA7cVDkGUi6kZusb04mpyEFKCIZJvloCcmpmLaIahDpOQGHaHmG6imtPMmPXGQ==}

  '@types/connect-history-api-fallback@1.5.4':
    resolution: {integrity: sha512-n6Cr2xS1h4uAulPRdlw6Jl6s1oG8KrVilPN2yUITEs+K48EzMJJ3W1xy8K5eWuFvjp3R74AOIGSmp2UfBJ8HFw==}

  '@types/connect@3.4.38':
    resolution: {integrity: sha512-K6uROf1LD88uDQqJCktA4yzL1YYAK6NgfsI0v/mTgyPKWsX1CnJ0XPSDhViejru1GcRkLWb8RlzFYJRqGUbaug==}

  '@types/d3-array@3.2.2':
    resolution: {integrity: sha512-hOLWVbm7uRza0BYXpIIW5pxfrKe0W+D5lrFiAEYR+pb6w3N2SwSMaJbXdUfSEv+dT4MfHBLtn5js0LAWaO6otw==}

  '@types/d3-axis@3.0.6':
    resolution: {integrity: sha512-pYeijfZuBd87T0hGn0FO1vQ/cgLk6E1ALJjfkC0oJ8cbwkZl3TpgS8bVBLZN+2jjGgg38epgxb2zmoGtSfvgMw==}

  '@types/d3-brush@3.0.6':
    resolution: {integrity: sha512-nH60IZNNxEcrh6L1ZSMNA28rj27ut/2ZmI3r96Zd+1jrZD++zD3LsMIjWlvg4AYrHn/Pqz4CF3veCxGjtbqt7A==}

  '@types/d3-chord@3.0.6':
    resolution: {integrity: sha512-LFYWWd8nwfwEmTZG9PfQxd17HbNPksHBiJHaKuY1XeqscXacsS2tyoo6OdRsjf+NQYeB6XrNL3a25E3gH69lcg==}

  '@types/d3-color@3.1.3':
    resolution: {integrity: sha512-iO90scth9WAbmgv7ogoq57O9YpKmFBbmoEoCHDB2xMBY0+/KVrqAaCDyCE16dUspeOvIxFFRI+0sEtqDqy2b4A==}

  '@types/d3-contour@3.0.6':
    resolution: {integrity: sha512-BjzLgXGnCWjUSYGfH1cpdo41/hgdWETu4YxpezoztawmqsvCeep+8QGfiY6YbDvfgHz/DkjeIkkZVJavB4a3rg==}

  '@types/d3-delaunay@6.0.4':
    resolution: {integrity: sha512-ZMaSKu4THYCU6sV64Lhg6qjf1orxBthaC161plr5KuPHo3CNm8DTHiLw/5Eq2b6TsNP0W0iJrUOFscY6Q450Hw==}

  '@types/d3-dispatch@3.0.7':
    resolution: {integrity: sha512-5o9OIAdKkhN1QItV2oqaE5KMIiXAvDWBDPrD85e58Qlz1c1kI/J0NcqbEG88CoTwJrYe7ntUCVfeUl2UJKbWgA==}

  '@types/d3-drag@3.0.7':
    resolution: {integrity: sha512-HE3jVKlzU9AaMazNufooRJ5ZpWmLIoc90A37WU2JMmeq28w1FQqCZswHZ3xR+SuxYftzHq6WU6KJHvqxKzTxxQ==}

  '@types/d3-dsv@3.0.7':
    resolution: {integrity: sha512-n6QBF9/+XASqcKK6waudgL0pf/S5XHPPI8APyMLLUHd8NqouBGLsU8MgtO7NINGtPBtk9Kko/W4ea0oAspwh9g==}

  '@types/d3-ease@3.0.2':
    resolution: {integrity: sha512-NcV1JjO5oDzoK26oMzbILE6HW7uVXOHLQvHshBUW4UMdZGfiY6v5BeQwh9a9tCzv+CeefZQHJt5SRgK154RtiA==}

  '@types/d3-fetch@3.0.7':
    resolution: {integrity: sha512-fTAfNmxSb9SOWNB9IoG5c8Hg6R+AzUHDRlsXsDZsNp6sxAEOP0tkP3gKkNSO/qmHPoBFTxNrjDprVHDQDvo5aA==}

  '@types/d3-force@3.0.10':
    resolution: {integrity: sha512-ZYeSaCF3p73RdOKcjj+swRlZfnYpK1EbaDiYICEEp5Q6sUiqFaFQ9qgoshp5CzIyyb/yD09kD9o2zEltCexlgw==}

  '@types/d3-format@3.0.4':
    resolution: {integrity: sha512-fALi2aI6shfg7vM5KiR1wNJnZ7r6UuggVqtDA+xiEdPZQwy/trcQaHnwShLuLdta2rTymCNpxYTiMZX/e09F4g==}

  '@types/d3-geo@3.1.0':
    resolution: {integrity: sha512-856sckF0oP/diXtS4jNsiQw/UuK5fQG8l/a9VVLeSouf1/PPbBE1i1W852zVwKwYCBkFJJB7nCFTbk6UMEXBOQ==}

  '@types/d3-hierarchy@3.1.7':
    resolution: {integrity: sha512-tJFtNoYBtRtkNysX1Xq4sxtjK8YgoWUNpIiUee0/jHGRwqvzYxkq0hGVbbOGSz+JgFxxRu4K8nb3YpG3CMARtg==}

  '@types/d3-interpolate@3.0.4':
    resolution: {integrity: sha512-mgLPETlrpVV1YRJIglr4Ez47g7Yxjl1lj7YKsiMCb27VJH9W8NVM6Bb9d8kkpG/uAQS5AmbA48q2IAolKKo1MA==}

  '@types/d3-path@3.1.1':
    resolution: {integrity: sha512-VMZBYyQvbGmWyWVea0EHs/BwLgxc+MKi1zLDCONksozI4YJMcTt8ZEuIR4Sb1MMTE8MMW49v0IwI5+b7RmfWlg==}

  '@types/d3-polygon@3.0.2':
    resolution: {integrity: sha512-ZuWOtMaHCkN9xoeEMr1ubW2nGWsp4nIql+OPQRstu4ypeZ+zk3YKqQT0CXVe/PYqrKpZAi+J9mTs05TKwjXSRA==}

  '@types/d3-quadtree@3.0.6':
    resolution: {integrity: sha512-oUzyO1/Zm6rsxKRHA1vH0NEDG58HrT5icx/azi9MF1TWdtttWl0UIUsjEQBBh+SIkrpd21ZjEv7ptxWys1ncsg==}

  '@types/d3-random@3.0.3':
    resolution: {integrity: sha512-Imagg1vJ3y76Y2ea0871wpabqp613+8/r0mCLEBfdtqC7xMSfj9idOnmBYyMoULfHePJyxMAw3nWhJxzc+LFwQ==}

  '@types/d3-scale-chromatic@3.1.0':
    resolution: {integrity: sha512-iWMJgwkK7yTRmWqRB5plb1kadXyQ5Sj8V/zYlFGMUBbIPKQScw+Dku9cAAMgJG+z5GYDoMjWGLVOvjghDEFnKQ==}

  '@types/d3-scale@4.0.9':
    resolution: {integrity: sha512-dLmtwB8zkAeO/juAMfnV+sItKjlsw2lKdZVVy6LRr0cBmegxSABiLEpGVmSJJ8O08i4+sGR6qQtb6WtuwJdvVw==}

  '@types/d3-selection@3.0.11':
    resolution: {integrity: sha512-bhAXu23DJWsrI45xafYpkQ4NtcKMwWnAC/vKrd2l+nxMFuvOT3XMYTIj2opv8vq8AO5Yh7Qac/nSeP/3zjTK0w==}

  '@types/d3-shape@3.1.8':
    resolution: {integrity: sha512-lae0iWfcDeR7qt7rA88BNiqdvPS5pFVPpo5OfjElwNaT2yyekbM0C9vK+yqBqEmHr6lDkRnYNoTBYlAgJa7a4w==}

  '@types/d3-time-format@4.0.3':
    resolution: {integrity: sha512-5xg9rC+wWL8kdDj153qZcsJ0FWiFt0J5RB6LYUNZjwSnesfblqrI/bJ1wBdJ8OQfncgbJG5+2F+qfqnqyzYxyg==}

  '@types/d3-time@3.0.4':
    resolution: {integrity: sha512-yuzZug1nkAAaBlBBikKZTgzCeA+k1uy4ZFwWANOfKw5z5LRhV0gNA7gNkKm7HoK+HRN0wX3EkxGk0fpbWhmB7g==}

  '@types/d3-timer@3.0.2':
    resolution: {integrity: sha512-Ps3T8E8dZDam6fUyNiMkekK3XUsaUEik+idO9/YjPtfj2qruF8tFBXS7XhtE4iIXBLxhmLjP3SXpLhVf21I9Lw==}

  '@types/d3-transition@3.0.9':
    resolution: {integrity: sha512-uZS5shfxzO3rGlu0cC3bjmMFKsXv+SmZZcgp0KD22ts4uGXp5EVYGzu/0YdwZeKmddhcAccYtREJKkPfXkZuCg==}

  '@types/d3-zoom@3.0.8':
    resolution: {integrity: sha512-iqMC4/YlFCSlO8+2Ii1GGGliCAY4XdeG748w5vQUbevlbDu0zSjH/+jojorQVBK/se0j6DUFNPBGSqD3YWYnDw==}

  '@types/d3@7.4.3':
    resolution: {integrity: sha512-lZXZ9ckh5R8uiFVt8ogUNf+pIrK4EsWrx2Np75WvF/eTpJ0FMHNhjXk8CKEx/+gpHbNQyJWehbFaTvqmHWB3ww==}

  '@types/debug@4.1.12':
    resolution: {integrity: sha512-vIChWdVG3LG1SMxEvI/AK+FWJthlrqlTu7fbrlywTkkaONwk/UAGaULXRlf8vkzFBLVm0zkMdCquhL5aOjhXPQ==}

  '@types/eslint-scope@3.7.7':
    resolution: {integrity: sha512-MzMFlSLBqNF2gcHWO0G1vP/YQyfvrxZ0bF+u7mzUdZ1/xK4A4sru+nraZz5i3iEIk1l1uyicaDVTB4QbbEkAYg==}

  '@types/eslint@9.6.1':
    resolution: {integrity: sha512-FXx2pKgId/WyYo2jXw63kk7/+TY7u7AziEJxJAnSFzHlqTAS3Ync6SvgYAN/k4/PQpnnVuzoMuVnByKK2qp0ag==}

  '@types/estree-jsx@1.0.5':
    resolution: {integrity: sha512-52CcUVNFyfb1A2ALocQw/Dd1BQFNmSdkuC3BkZ6iqhdMfQz7JWOFRuJFloOzjk+6WijU56m9oKXFAXc7o3Towg==}

  '@types/estree@1.0.8':
    resolution: {integrity: sha512-dWHzHa2WqEXI/O1E9OjrocMTKJl2mSrEolh1Iomrv6U+JuNwaHXsXx9bLu5gG7BUWFIN0skIQJQ/L1rIex4X6w==}

  '@types/express-serve-static-core@4.19.8':
    resolution: {integrity: sha512-02S5fmqeoKzVZCHPZid4b8JH2eM5HzQLZWN2FohQEy/0eXTq8VXZfSN6Pcr3F6N9R/vNrj7cpgbhjie6m/1tCA==}

  '@types/express@4.17.25':
    resolution: {integrity: sha512-dVd04UKsfpINUnK0yBoYHDF3xu7xVH4BuDotC/xGuycx4CgbP48X/KF/586bcObxT0HENHXEU8Nqtu6NR+eKhw==}

  '@types/geojson@7946.0.16':
    resolution: {integrity: sha512-6C8nqWur3j98U6+lXDfTUWIfgvZU+EumvpHKcYjujKH7woYyLj2sUmff0tRhrqM7BohUw7Pz3ZB1jj2gW9Fvmg==}

  '@types/gtag.js@0.0.12':
    resolution: {integrity: sha512-YQV9bUsemkzG81Ea295/nF/5GijnD2Af7QhEofh7xu+kvCN6RdodgNwwGWXB5GMI3NoyvQo0odNctoH/qLMIpg==}

  '@types/hast@3.0.4':
    resolution: {integrity: sha512-WPs+bbQw5aCj+x6laNGWLH3wviHtoCv/P3+otBhbOhJgG8qtpdAMlTCxLtsTWA7LH1Oh/bFCHsBn0TPS5m30EQ==}

  '@types/history@4.7.11':
    resolution: {integrity: sha512-qjDJRrmvBMiTx+jyLxvLfJU7UznFuokDv4f3WRuriHKERccVpFU+8XMQUAbDzoiJCsmexxRExQeMwwCdamSKDA==}

  '@types/html-minifier-terser@6.1.0':
    resolution: {integrity: sha512-oh/6byDPnL1zeNXFrDXFLyZjkr1MsBG667IM792caf1L2UPOOMf65NFzjUH/ltyfwjAGfs1rsX1eftK0jC/KIg==}

  '@types/http-cache-semantics@4.0.4':
    resolution: {integrity: sha512-1m0bIFVc7eJWyve9S0RnuRgcQqF/Xd5QsUZAZeQFr1Q3/p9JWoQQEqmVy+DPTNpGXwhgIetAoYF8JSc33q29QA==}

  '@types/http-errors@2.0.5':
    resolution: {integrity: sha512-r8Tayk8HJnX0FztbZN7oVqGccWgw98T/0neJphO91KkmOzug1KkofZURD4UaD5uH8AqcFLfdPErnBod0u71/qg==}

  '@types/http-proxy@1.17.17':
    resolution: {integrity: sha512-ED6LB+Z1AVylNTu7hdzuBqOgMnvG/ld6wGCG8wFnAzKX5uyW2K3WD52v0gnLCTK/VLpXtKckgWuyScYK6cSPaw==}

  '@types/istanbul-lib-coverage@2.0.6':
    resolution: {integrity: sha512-2QF/t/auWm0lsy8XtKVPG19v3sSOQlJe/YHZgfjb/KBBHOGSV+J2q/S671rcq9uTBrLAXmZpqJiaQbMT+zNU1w==}

  '@types/istanbul-lib-report@3.0.3':
    resolution: {integrity: sha512-NQn7AHQnk/RSLOxrBbGyJM/aVQ+pjj5HCgasFxc0K/KhoATfQ/47AyUl15I2yBUpihjmas+a+VJBOqecrFH+uA==}

  '@types/istanbul-reports@3.0.4':
    resolution: {integrity: sha512-pk2B1NWalF9toCRu6gjBzR69syFjP4Od8WRAX+0mmf9lAjCRicLOWc+ZrxZHx/0XRjotgkF9t6iaMJ+aXcOdZQ==}

  '@types/json-schema@7.0.15':
    resolution: {integrity: sha512-5+fP8P8MFNC+AyZCDxrB2pkZFPGzqQWUzpSeuuVLvm8VMcorNYavBqoFcxK8bQz4Qsbn4oUEEem4wDLfcysGHA==}

  '@types/mdast@4.0.4':
    resolution: {integrity: sha512-kGaNbPh1k7AFzgpud/gMdvIm5xuECykRR+JnWKQno9TAXVa6WIVCGTPvYGekIDL4uwCZQSYbUxNBSb1aUo79oA==}

  '@types/mdx@2.0.13':
    resolution: {integrity: sha512-+OWZQfAYyio6YkJb3HLxDrvnx6SWWDbC0zVPfBRzUk0/nqoDyf6dNxQi3eArPe8rJ473nobTMQ/8Zk+LxJ+Yuw==}

  '@types/mime@1.3.5':
    resolution: {integrity: sha512-/pyBZWSLD2n0dcHE3hq8s8ZvcETHtEuF+3E7XVt0Ig2nvsVQXdghHVcEkIWjy9A0wKfTn97a/PSDYohKIlnP/w==}

  '@types/ms@2.1.0':
    resolution: {integrity: sha512-GsCCIZDE/p3i96vtEqx+7dBUGXrc7zeSK3wwPHIaRThS+9OhWIXRqzs4d6k1SVU8g91DrNRWxWUGhp5KXQb2VA==}

  '@types/node@17.0.45':
    resolution: {integrity: sha512-w+tIMs3rq2afQdsPJlODhoUEKzFP1ayaoyl1CcnwtIlsVe7K7bA1NGm4s3PraqTLlXnbIN84zuBlxBWo1u9BLw==}

  '@types/node@25.0.6':
    resolution: {integrity: sha512-NNu0sjyNxpoiW3YuVFfNz7mxSQ+S4X2G28uqg2s+CzoqoQjLPsWSbsFFyztIAqt2vb8kfEAsJNepMGPTxFDx3Q==}

  '@types/prismjs@1.26.5':
    resolution: {integrity: sha512-AUZTa7hQ2KY5L7AmtSiqxlhWxb4ina0yd8hNbl4TWuqnv/pFP0nDMb3YrfSBf4hJVGLh2YEIBfKaBW/9UEl6IQ==}

  '@types/qs@6.14.0':
    resolution: {integrity: sha512-eOunJqu0K1923aExK6y8p6fsihYEn/BYuQ4g0CxAAgFc4b/ZLN4CrsRZ55srTdqoiLzU2B2evC+apEIxprEzkQ==}

  '@types/range-parser@1.2.7':
    resolution: {integrity: sha512-hKormJbkJqzQGhziax5PItDUTMAM9uE2XXQmM37dyd4hVM+5aVl7oVxMVUiVQn2oCQFN/LKCZdvSM0pFRqbSmQ==}

  '@types/react-dom@19.2.3':
    resolution: {integrity: sha512-jp2L/eY6fn+KgVVQAOqYItbF0VY/YApe5Mz2F0aykSO8gx31bYCZyvSeYxCHKvzHG5eZjc+zyaS5BrBWya2+kQ==}
    peerDependencies:
      '@types/react': ^19.2.0

  '@types/react-router-config@5.0.11':
    resolution: {integrity: sha512-WmSAg7WgqW7m4x8Mt4N6ZyKz0BubSj/2tVUMsAHp+Yd2AMwcSbeFq9WympT19p5heCFmF97R9eD5uUR/t4HEqw==}

  '@types/react-router-dom@5.3.3':
    resolution: {integrity: sha512-kpqnYK4wcdm5UaWI3fLcELopqLrHgLqNsdpHauzlQktfkHL3npOSwtj1Uz9oKBAzs7lFtVkV8j83voAz2D8fhw==}

  '@types/react-router@5.1.20':
    resolution: {integrity: sha512-jGjmu/ZqS7FjSH6owMcD5qpq19+1RS9DeVRqfl1FeBMxTDQAGwlMWOcs52NDoXaNKyG3d1cYQFMs9rCrb88o9Q==}

  '@types/react@19.2.8':
    resolution: {integrity: sha512-3MbSL37jEchWZz2p2mjntRZtPt837ij10ApxKfgmXCTuHWagYg7iA5bqPw6C8BMPfwidlvfPI/fxOc42HLhcyg==}

  '@types/retry@0.12.2':
    resolution: {integrity: sha512-XISRgDJ2Tc5q4TRqvgJtzsRkFYNJzZrhTdtMoGVBttwzzQJkPnS3WWTFc7kuDRoPtPakl+T+OfdEUjYJj7Jbow==}

  '@types/sax@1.2.7':
    resolution: {integrity: sha512-rO73L89PJxeYM3s3pPPjiPgVVcymqU490g0YO5n5By0k2Erzj6tay/4lr1CHAAU4JyOWd1rpQ8bCf6cZfHU96A==}

  '@types/send@0.17.6':
    resolution: {integrity: sha512-Uqt8rPBE8SY0RK8JB1EzVOIZ32uqy8HwdxCnoCOsYrvnswqmFZ/k+9Ikidlk/ImhsdvBsloHbAlewb2IEBV/Og==}

  '@types/send@1.2.1':
    resolution: {integrity: sha512-arsCikDvlU99zl1g69TcAB3mzZPpxgw0UQnaHeC1Nwb015xp8bknZv5rIfri9xTOcMuaVgvabfIRA7PSZVuZIQ==}

  '@types/serve-index@1.9.4':
    resolution: {integrity: sha512-qLpGZ/c2fhSs5gnYsQxtDEq3Oy8SXPClIXkW5ghvAvsNuVSA8k+gCONcUCS/UjLEYvYps+e8uBtfgXgvhwfNug==}

  '@types/serve-static@1.15.10':
    resolution: {integrity: sha512-tRs1dB+g8Itk72rlSI2ZrW6vZg0YrLI81iQSTkMmOqnqCaNr/8Ek4VwWcN5vZgCYWbg/JJSGBlUaYGAOP73qBw==}

  '@types/sockjs@0.3.36':
    resolution: {integrity: sha512-MK9V6NzAS1+Ud7JV9lJLFqW85VbC9dq3LmwZCuBe4wBDgKC0Kj/jd8Xl+nSviU+Qc3+m7umHHyHg//2KSa0a0Q==}

  '@types/trusted-types@2.0.7':
    resolution: {integrity: sha512-ScaPdn1dQczgbl0QFTeTOmVHFULt394XJgOQNoyVhZ6r2vLnMLJfBPd53SB52T/3G36VI1/g2MZaX0cwDuXsfw==}

  '@types/unist@2.0.11':
    resolution: {integrity: sha512-CmBKiL6NNo/OqgmMn95Fk9Whlp2mtvIv+KNpQKN2F4SjvrEesubTRWGYSg+BnWZOnlCaSTU1sMpsBOzgbYhnsA==}

  '@types/unist@3.0.3':
    resolution: {integrity: sha512-ko/gIFJRv177XgZsZcBwnqJN5x/Gien8qNOn0D5bQU/zAzVf9Zt3BlcUiLqhV9y4ARk0GbT3tnUiPNgnTXzc/Q==}

  '@types/ws@8.18.1':
    resolution: {integrity: sha512-ThVF6DCVhA8kUGy+aazFQ4kXQ7E1Ty7A3ypFOe0IcJV8O/M511G99AW24irKrW56Wt44yG9+ij8FaqoBGkuBXg==}

  '@types/yargs-parser@21.0.3':
    resolution: {integrity: sha512-I4q9QU9MQv4oEOz4tAHJtNz1cwuLxn2F3xcc2iV5WdqLPpUnj30aUuxt1mAxYTG+oe8CZMV/+6rU4S4gRDzqtQ==}

  '@types/yargs@17.0.35':
    resolution: {integrity: sha512-qUHkeCyQFxMXg79wQfTtfndEC+N9ZZg76HJftDJp+qH2tV7Gj4OJi7l+PiWwJ+pWtW8GwSmqsDj/oymhrTWXjg==}

  '@typescript-eslint/eslint-plugin@8.52.0':
    resolution: {integrity: sha512-okqtOgqu2qmZJ5iN4TWlgfF171dZmx2FzdOv2K/ixL2LZWDStL8+JgQerI2sa8eAEfoydG9+0V96m7V+P8yE1Q==}
    engines: {node: ^18.18.0 || ^20.9.0 || >=21.1.0}
    peerDependencies:
      '@typescript-eslint/parser': ^8.52.0
      eslint: ^8.57.0 || ^9.0.0
      typescript: '>=4.8.4 <6.0.0'

  '@typescript-eslint/parser@8.52.0':
    resolution: {integrity: sha512-iIACsx8pxRnguSYhHiMn2PvhvfpopO9FXHyn1mG5txZIsAaB6F0KwbFnUQN3KCiG3Jcuad/Cao2FAs1Wp7vAyg==}
    engines: {node: ^18.18.0 || ^20.9.0 || >=21.1.0}
    peerDependencies:
      eslint: ^8.57.0 || ^9.0.0
      typescript: '>=4.8.4 <6.0.0'

  '@typescript-eslint/project-service@8.52.0':
    resolution: {integrity: sha512-xD0MfdSdEmeFa3OmVqonHi+Cciab96ls1UhIF/qX/O/gPu5KXD0bY9lu33jj04fjzrXHcuvjBcBC+D3SNSadaw==}
    engines: {node: ^18.18.0 || ^20.9.0 || >=21.1.0}
    peerDependencies:
      typescript: '>=4.8.4 <6.0.0'

  '@typescript-eslint/scope-manager@8.52.0':
    resolution: {integrity: sha512-ixxqmmCcc1Nf8S0mS0TkJ/3LKcC8mruYJPOU6Ia2F/zUUR4pApW7LzrpU3JmtePbRUTes9bEqRc1Gg4iyRnDzA==}
    engines: {node: ^18.18.0 || ^20.9.0 || >=21.1.0}

  '@typescript-eslint/tsconfig-utils@8.52.0':
    resolution: {integrity: sha512-jl+8fzr/SdzdxWJznq5nvoI7qn2tNYV/ZBAEcaFMVXf+K6jmXvAFrgo/+5rxgnL152f//pDEAYAhhBAZGrVfwg==}
    engines: {node: ^18.18.0 || ^20.9.0 || >=21.1.0}
    peerDependencies:
      typescript: '>=4.8.4 <6.0.0'

  '@typescript-eslint/type-utils@8.52.0':
    resolution: {integrity: sha512-JD3wKBRWglYRQkAtsyGz1AewDu3mTc7NtRjR/ceTyGoPqmdS5oCdx/oZMWD5Zuqmo6/MpsYs0wp6axNt88/2EQ==}
    engines: {node: ^18.18.0 || ^20.9.0 || >=21.1.0}
    peerDependencies:
      eslint: ^8.57.0 || ^9.0.0
      typescript: '>=4.8.4 <6.0.0'

  '@typescript-eslint/types@8.52.0':
    resolution: {integrity: sha512-LWQV1V4q9V4cT4H5JCIx3481iIFxH1UkVk+ZkGGAV1ZGcjGI9IoFOfg3O6ywz8QqCDEp7Inlg6kovMofsNRaGg==}
    engines: {node: ^18.18.0 || ^20.9.0 || >=21.1.0}

  '@typescript-eslint/typescript-estree@8.52.0':
    resolution: {integrity: sha512-XP3LClsCc0FsTK5/frGjolyADTh3QmsLp6nKd476xNI9CsSsLnmn4f0jrzNoAulmxlmNIpeXuHYeEQv61Q6qeQ==}
    engines: {node: ^18.18.0 || ^20.9.0 || >=21.1.0}
    peerDependencies:
      typescript: '>=4.8.4 <6.0.0'

  '@typescript-eslint/utils@8.52.0':
    resolution: {integrity: sha512-wYndVMWkweqHpEpwPhwqE2lnD2DxC6WVLupU/DOt/0/v+/+iQbbzO3jOHjmBMnhu0DgLULvOaU4h4pwHYi2oRQ==}
    engines: {node: ^18.18.0 || ^20.9.0 || >=21.1.0}
    peerDependencies:
      eslint: ^8.57.0 || ^9.0.0
      typescript: '>=4.8.4 <6.0.0'

  '@typescript-eslint/visitor-keys@8.52.0':
    resolution: {integrity: sha512-ink3/Zofus34nmBsPjow63FP5M7IGff0RKAgqR6+CFpdk22M7aLwC9gOcLGYqr7MczLPzZVERW9hRog3O4n1sQ==}
    engines: {node: ^18.18.0 || ^20.9.0 || >=21.1.0}

  '@ungap/structured-clone@1.3.0':
    resolution: {integrity: sha512-WmoN8qaIAo7WTYWbAZuG8PYEhn5fkz7dZrqTBZ7dtt//lL2Gwms1IcnQ5yHqjDfX8Ft5j4YzDM23f87zBfDe9g==}

  '@vercel/oidc@3.0.5':
    resolution: {integrity: sha512-fnYhv671l+eTTp48gB4zEsTW/YtRgRPnkI2nT7x6qw5rkI1Lq2hTmQIpHPgyThI0znLK+vX2n9XxKdXZ7BUbbw==}
    engines: {node: '>= 20'}

  '@webassemblyjs/ast@1.14.1':
    resolution: {integrity: sha512-nuBEDgQfm1ccRp/8bCQrx1frohyufl4JlbMMZ4P1wpeOfDhF6FQkxZJ1b/e+PLwr6X1Nhw6OLme5usuBWYBvuQ==}

  '@webassemblyjs/floating-point-hex-parser@1.13.2':
    resolution: {integrity: sha512-6oXyTOzbKxGH4steLbLNOu71Oj+C8Lg34n6CqRvqfS2O71BxY6ByfMDRhBytzknj9yGUPVJ1qIKhRlAwO1AovA==}

  '@webassemblyjs/helper-api-error@1.13.2':
    resolution: {integrity: sha512-U56GMYxy4ZQCbDZd6JuvvNV/WFildOjsaWD3Tzzvmw/mas3cXzRJPMjP83JqEsgSbyrmaGjBfDtV7KDXV9UzFQ==}

  '@webassemblyjs/helper-buffer@1.14.1':
    resolution: {integrity: sha512-jyH7wtcHiKssDtFPRB+iQdxlDf96m0E39yb0k5uJVhFGleZFoNw1c4aeIcVUPPbXUVJ94wwnMOAqUHyzoEPVMA==}

  '@webassemblyjs/helper-numbers@1.13.2':
    resolution: {integrity: sha512-FE8aCmS5Q6eQYcV3gI35O4J789wlQA+7JrqTTpJqn5emA4U2hvwJmvFRC0HODS+3Ye6WioDklgd6scJ3+PLnEA==}

  '@webassemblyjs/helper-wasm-bytecode@1.13.2':
    resolution: {integrity: sha512-3QbLKy93F0EAIXLh0ogEVR6rOubA9AoZ+WRYhNbFyuB70j3dRdwH9g+qXhLAO0kiYGlg3TxDV+I4rQTr/YNXkA==}

  '@webassemblyjs/helper-wasm-section@1.14.1':
    resolution: {integrity: sha512-ds5mXEqTJ6oxRoqjhWDU83OgzAYjwsCV8Lo/N+oRsNDmx/ZDpqalmrtgOMkHwxsG0iI//3BwWAErYRHtgn0dZw==}

  '@webassemblyjs/ieee754@1.13.2':
    resolution: {integrity: sha512-4LtOzh58S/5lX4ITKxnAK2USuNEvpdVV9AlgGQb8rJDHaLeHciwG4zlGr0j/SNWlr7x3vO1lDEsuePvtcDNCkw==}

  '@webassemblyjs/leb128@1.13.2':
    resolution: {integrity: sha512-Lde1oNoIdzVzdkNEAWZ1dZ5orIbff80YPdHx20mrHwHrVNNTjNr8E3xz9BdpcGqRQbAEa+fkrCb+fRFTl/6sQw==}

  '@webassemblyjs/utf8@1.13.2':
    resolution: {integrity: sha512-3NQWGjKTASY1xV5m7Hr0iPeXD9+RDobLll3T9d2AO+g3my8xy5peVyjSag4I50mR1bBSN/Ct12lo+R9tJk0NZQ==}

  '@webassemblyjs/wasm-edit@1.14.1':
    resolution: {integrity: sha512-RNJUIQH/J8iA/1NzlE4N7KtyZNHi3w7at7hDjvRNm5rcUXa00z1vRz3glZoULfJ5mpvYhLybmVcwcjGrC1pRrQ==}

  '@webassemblyjs/wasm-gen@1.14.1':
    resolution: {integrity: sha512-AmomSIjP8ZbfGQhumkNvgC33AY7qtMCXnN6bL2u2Js4gVCg8fp735aEiMSBbDR7UQIj90n4wKAFUSEd0QN2Ukg==}

  '@webassemblyjs/wasm-opt@1.14.1':
    resolution: {integrity: sha512-PTcKLUNvBqnY2U6E5bdOQcSM+oVP/PmrDY9NzowJjislEjwP/C4an2303MCVS2Mg9d3AJpIGdUFIQQWbPds0Sw==}

  '@webassemblyjs/wasm-parser@1.14.1':
    resolution: {integrity: sha512-JLBl+KZ0R5qB7mCnud/yyX08jWFw5MsoalJ1pQ4EdFlgj9VdXKGuENGsiCIjegI1W7p91rUlcB/LB5yRJKNTcQ==}

  '@webassemblyjs/wast-printer@1.14.1':
    resolution: {integrity: sha512-kPSSXE6De1XOR820C90RIo2ogvZG+c3KiHzqUoO/F34Y2shGzesfqv7o57xrxovZJH/MetF5UjroJ/R/3isoiw==}

  '@xtuc/ieee754@1.2.0':
    resolution: {integrity: sha512-DX8nKgqcGwsc0eJSqYt5lwP4DH5FlHnmuWWBRy7X0NcaGR0ZtuyeESgMwTYVEtxmsNGY+qit4QYT/MIYTOTPeA==}

  '@xtuc/long@4.2.2':
    resolution: {integrity: sha512-NuHqBY1PB/D8xU6s/thBgOAiAP7HOYDQ32+BFZILJ8ivkUkAHQnWfn6WhL79Owj1qmUnoN/YPhktdIoucipkAQ==}

  accepts@1.3.8:
    resolution: {integrity: sha512-PYAthTa2m2VKxuvSD3DPC/Gy+U+sOA1LAuT8mkmRuvw+NACSaeXEQ+NHcVF7rONl6qcaxV3Uuemwawk+7+SJLw==}
    engines: {node: '>= 0.6'}

  acorn-import-phases@1.0.4:
    resolution: {integrity: sha512-wKmbr/DDiIXzEOiWrTTUcDm24kQ2vGfZQvM2fwg2vXqR5uW6aapr7ObPtj1th32b9u90/Pf4AItvdTh42fBmVQ==}
    engines: {node: '>=10.13.0'}
    peerDependencies:
      acorn: ^8.14.0

  acorn-jsx@5.3.2:
    resolution: {integrity: sha512-rq9s+JNhf0IChjtDXxllJ7g41oZk5SlXtp0LHwyA5cejwn7vKmKp4pPri6YEePv2PU65sAsegbXtIinmDFDXgQ==}
    peerDependencies:
      acorn: ^6.0.0 || ^7.0.0 || ^8.0.0

  acorn-walk@8.3.4:
    resolution: {integrity: sha512-ueEepnujpqee2o5aIYnvHU6C0A42MNdsIDeqy5BydrkuC5R1ZuUFnm27EeFJGoEHJQgn3uleRvmTXaJgfXbt4g==}
    engines: {node: '>=0.4.0'}

  acorn@8.15.0:
    resolution: {integrity: sha512-NZyJarBfL7nWwIq+FDL6Zp/yHEhePMNnnJ0y3qfieCrmNvYct8uvtiV41UvlSe6apAfk0fY1FbWx+NwfmpvtTg==}
    engines: {node: '>=0.4.0'}
    hasBin: true

  address@1.2.2:
    resolution: {integrity: sha512-4B/qKCfeE/ODUaAUpSwfzazo5x29WD4r3vXiWsB7I2mSDAihwEqKO+g8GELZUQSSAo5e1XTYh3ZVfLyxBc12nA==}
    engines: {node: '>= 10.0.0'}

  aggregate-error@3.1.0:
    resolution: {integrity: sha512-4I7Td01quW/RpocfNayFdFVk1qSuoh0E7JrbRJ16nH01HhKFQ88INq9Sd+nd72zqRySlr9BmDA8xlEJ6vJMrYA==}
    engines: {node: '>=8'}

  ai@5.0.119:
    resolution: {integrity: sha512-HUOwhc17fl2SZTJGZyA/99aNu706qKfXaUBCy9vgZiXBwrxg2eTzn2BCz7kmYDsfx6Fg2ACBy2icm41bsDXCTw==}
    engines: {node: '>=18'}
    peerDependencies:
      zod: ^3.25.76 || ^4.1.8

  ajv-formats@2.1.1:
    resolution: {integrity: sha512-Wx0Kx52hxE7C18hkMEggYlEifqWZtYaRgouJor+WMdPnQyEK13vgEWyVNup7SoeeoLMsr4kf5h6dOW11I15MUA==}
    peerDependencies:
      ajv: ^8.0.0
    peerDependenciesMeta:
      ajv:
        optional: true

  ajv-keywords@3.5.2:
    resolution: {integrity: sha512-5p6WTN0DdTGVQk6VjcEju19IgaHudalcfabD7yhDGeA6bcQnmL+CpveLJq/3hvfwd1aof6L386Ougkx6RfyMIQ==}
    peerDependencies:
      ajv: ^6.9.1

  ajv-keywords@5.1.0:
    resolution: {integrity: sha512-YCS/JNFAUyr5vAuhk1DWm1CBxRHW9LbJ2ozWeemrIqpbsqKjHVxYPyi5GC0rjZIT5JxJ3virVTS8wk4i/Z+krw==}
    peerDependencies:
      ajv: ^8.8.2

  ajv@6.12.6:
    resolution: {integrity: sha512-j3fVLgvTo527anyYyJOGTYJbG+vnnQYvE0m5mmkc1TK+nxAppkCLMIL0aZ4dblVCNoGShhm+kzE4ZUykBoMg4g==}

  ajv@8.17.1:
    resolution: {integrity: sha512-B/gBuNg5SiMTrPkC+A2+cW0RszwxYmn6VYxB/inlBStS5nx6xHIt/ehKRhIMhqusl7a8LjQoZnjCs5vhwxOQ1g==}

  algoliasearch-helper@3.27.0:
    resolution: {integrity: sha512-eNYchRerbsvk2doHOMfdS1/B6Tm70oGtu8mzQlrNzbCeQ8p1MjCW8t/BL6iZ5PD+cL5NNMgTMyMnmiXZ1sgmNw==}
    peerDependencies:
      algoliasearch: '>= 3.1 < 6'

  algoliasearch@5.46.2:
    resolution: {integrity: sha512-qqAXW9QvKf2tTyhpDA4qXv1IfBwD2eduSW6tUEBFIfCeE9gn9HQ9I5+MaKoenRuHrzk5sQoNh1/iof8mY7uD6Q==}
    engines: {node: '>= 14.0.0'}

  ansi-align@3.0.1:
    resolution: {integrity: sha512-IOfwwBF5iczOjp/WeY4YxyjqAFMQoZufdQWDd19SEExbVLNXqvpzSJ/M7Za4/sCPmQ0+GRquoA7bGcINcxew6w==}

  ansi-escapes@4.3.2:
    resolution: {integrity: sha512-gKXj5ALrKWQLsYG9jlTRmR/xKluxHV+Z9QEwNIgCfM1/uwPMCuzVVnh5mwTd+OuBZcwSIMbqssNWRm1lE51QaQ==}
    engines: {node: '>=8'}

  ansi-escapes@7.2.0:
    resolution: {integrity: sha512-g6LhBsl+GBPRWGWsBtutpzBYuIIdBkLEvad5C/va/74Db018+5TZiyA26cZJAr3Rft5lprVqOIPxf5Vid6tqAw==}
    engines: {node: '>=18'}

  ansi-html-community@0.0.8:
    resolution: {integrity: sha512-1APHAyr3+PCamwNw3bXCPp4HFLONZt/yIH0sZp0/469KWNTEy+qN5jQ3GVX6DMZ1UXAi34yVwtTeaG/HpBuuzw==}
    engines: {'0': node >= 0.8.0}
    hasBin: true

  ansi-regex@5.0.1:
    resolution: {integrity: sha512-quJQXlTSUGL2LH9SUXo8VwsY4soanhgo6LNSm84E1LBcE8s3O0wpdiRzyR9z/ZZJMlMWv37qOOb9pdJlMUEKFQ==}
    engines: {node: '>=8'}

  ansi-regex@6.2.2:
    resolution: {integrity: sha512-Bq3SmSpyFHaWjPk8If9yc6svM8c56dB5BAtW4Qbw5jHTwwXXcTLoRMkpDJp6VL0XzlWaCHTXrkFURMYmD0sLqg==}
    engines: {node: '>=12'}

  ansi-styles@4.3.0:
    resolution: {integrity: sha512-zbB9rCJAT1rbjiVDb2hqKFHNYLxgtk8NURxZ3IZwD3F6NtxbXZQCnnSi1Lkx+IDohdPlFp222wVALIheZJQSEg==}
    engines: {node: '>=8'}

  ansi-styles@6.2.3:
    resolution: {integrity: sha512-4Dj6M28JB+oAH8kFkTLUo+a2jwOFkuqb3yucU0CANcRRUbxS0cP0nZYCGjcc3BNXwRIsUVmDGgzawme7zvJHvg==}
    engines: {node: '>=12'}

  anymatch@3.1.3:
    resolution: {integrity: sha512-KMReFUr0B4t+D+OBkjR3KYqvocp2XaSzO55UcB6mgQMd3KbcE+mWTyvVV7D/zsdEbNnV6acZUutkiHQXvTr1Rw==}
    engines: {node: '>= 8'}

  arg@5.0.2:
    resolution: {integrity: sha512-PYjyFOLKQ9y57JvQ6QLo8dAgNqswh8M1RMJYdQduT6xbWSgK36P/Z/v+p888pM69jMMfS8Xd8F6I1kQ/I9HUGg==}

  argparse@1.0.10:
    resolution: {integrity: sha512-o5Roy6tNG4SL/FOkCAN6RzjiakZS25RLYFrcMttJqbdd8BWrnA+fGz57iN5Pb06pvBGvl5gQ0B48dJlslXvoTg==}

  argparse@2.0.1:
    resolution: {integrity: sha512-8+9WqebbFzpX9OR+Wa6O29asIogeRMzcGtAINdpMHHyAg10f05aSFVBbcEqGf/PXw1EjAZ+q2/bEBg3DvurK3Q==}

  array-buffer-byte-length@1.0.2:
    resolution: {integrity: sha512-LHE+8BuR7RYGDKvnrmcuSq3tDcKv9OFEXQt/HpbZhY7V6h0zlUXutnAD82GiFx9rdieCMjkvtcsPqBwgUl1Iiw==}
    engines: {node: '>= 0.4'}

  array-flatten@1.1.1:
    resolution: {integrity: sha512-PCVAQswWemu6UdxsDFFX/+gVeYqKAod3D3UVm91jHwynguOwAvYPhx8nNlM++NqRcK6CxxpUafjmhIdKiHibqg==}

  array-includes@3.1.9:
    resolution: {integrity: sha512-FmeCCAenzH0KH381SPT5FZmiA/TmpndpcaShhfgEN9eCVjnFBqq3l1xrI42y8+PPLI6hypzou4GXw00WHmPBLQ==}
    engines: {node: '>= 0.4'}

  array-union@2.1.0:
    resolution: {integrity: sha512-HGyxoOTYUyCM6stUe6EJgnd4EoewAI7zMdfqO+kGjnlZmBDz/cR5pf8r/cR4Wq60sL/p0IkcjUEEPwS3GFrIyw==}
    engines: {node: '>=8'}

  array.prototype.findlast@1.2.5:
    resolution: {integrity: sha512-CVvd6FHg1Z3POpBLxO6E6zr+rSKEQ9L6rZHAaY7lLfhKsWYUBBOuMs0e9o24oopj6H+geRCX0YJ+TJLBK2eHyQ==}
    engines: {node: '>= 0.4'}

  array.prototype.flat@1.3.3:
    resolution: {integrity: sha512-rwG/ja1neyLqCuGZ5YYrznA62D4mZXg0i1cIskIUKSiqF3Cje9/wXAls9B9s1Wa2fomMsIv8czB8jZcPmxCXFg==}
    engines: {node: '>= 0.4'}

  array.prototype.flatmap@1.3.3:
    resolution: {integrity: sha512-Y7Wt51eKJSyi80hFrJCePGGNo5ktJCslFuboqJsbf57CCPcm5zztluPlc4/aD8sWsKvlwatezpV4U1efk8kpjg==}
    engines: {node: '>= 0.4'}

  array.prototype.tosorted@1.1.4:
    resolution: {integrity: sha512-p6Fx8B7b7ZhL/gmUsAy0D15WhvDccw3mnGNbZpi3pmeJdxtWsj2jEaI4Y6oo3XiHfzuSgPwKc04MYt6KgvC/wA==}
    engines: {node: '>= 0.4'}

  arraybuffer.prototype.slice@1.0.4:
    resolution: {integrity: sha512-BNoCY6SXXPQ7gF2opIP4GBE+Xw7U+pHMYKuzjgCN3GwiaIR09UUeKfheyIry77QtrCBlC0KK0q5/TER/tYh3PQ==}
    engines: {node: '>= 0.4'}

  asn1js@3.0.7:
    resolution: {integrity: sha512-uLvq6KJu04qoQM6gvBfKFjlh6Gl0vOKQuR5cJMDHQkmwfMOQeN3F3SHCv9SNYSL+CRoHvOGFfllDlVz03GQjvQ==}
    engines: {node: '>=12.0.0'}

  astring@1.9.0:
    resolution: {integrity: sha512-LElXdjswlqjWrPpJFg1Fx4wpkOCxj1TDHlSV4PlaRxHGWko024xICaa97ZkMfs6DRKlCguiAI+rbXv5GWwXIkg==}
    hasBin: true

  async-function@1.0.0:
    resolution: {integrity: sha512-hsU18Ae8CDTR6Kgu9DYf0EbCr/a5iGL0rytQDobUcdpYOKokk8LEjVphnXkDkgpi0wYVsqrXuP0bZxJaTqdgoA==}
    engines: {node: '>= 0.4'}

  autoprefixer@10.4.23:
    resolution: {integrity: sha512-YYTXSFulfwytnjAPlw8QHncHJmlvFKtczb8InXaAx9Q0LbfDnfEYDE55omerIJKihhmU61Ft+cAOSzQVaBUmeA==}
    engines: {node: ^10 || ^12 || >=14}
    hasBin: true
    peerDependencies:
      postcss: ^8.1.0

  available-typed-arrays@1.0.7:
    resolution: {integrity: sha512-wvUjBtSGN7+7SjNpq/9M2Tg350UZD3q62IFZLbRAR1bSMlCo1ZaeW+BJ+D090e4hIIZLBcTDWe4Mh4jvUDajzQ==}
    engines: {node: '>= 0.4'}

  babel-loader@9.2.1:
    resolution: {integrity: sha512-fqe8naHt46e0yIdkjUZYqddSXfej3AHajX+CSO5X7oy0EmPc6o5Xh+RClNoHjnieWz9AW4kZxW9yyFMhVB1QLA==}
    engines: {node: '>= 14.15.0'}
    peerDependencies:
      '@babel/core': ^7.12.0
      webpack: '>=5'

  babel-plugin-dynamic-import-node@2.3.3:
    resolution: {integrity: sha512-jZVI+s9Zg3IqA/kdi0i6UDCybUI3aSBLnglhYbSSjKlV7yF1F/5LWv8MakQmvYpnbJDS6fcBL2KzHSxNCMtWSQ==}

  babel-plugin-polyfill-corejs2@0.4.14:
    resolution: {integrity: sha512-Co2Y9wX854ts6U8gAAPXfn0GmAyctHuK8n0Yhfjd6t30g7yvKjspvvOo9yG+z52PZRgFErt7Ka2pYnXCjLKEpg==}
    peerDependencies:
      '@babel/core': ^7.4.0 || ^8.0.0-0 <8.0.0

  babel-plugin-polyfill-corejs3@0.13.0:
    resolution: {integrity: sha512-U+GNwMdSFgzVmfhNm8GJUX88AadB3uo9KpJqS3FaqNIPKgySuvMb+bHPsOmmuWyIcuqZj/pzt1RUIUZns4y2+A==}
    peerDependencies:
      '@babel/core': ^7.4.0 || ^8.0.0-0 <8.0.0

  babel-plugin-polyfill-regenerator@0.6.5:
    resolution: {integrity: sha512-ISqQ2frbiNU9vIJkzg7dlPpznPZ4jOiUQ1uSmB0fEHeowtN3COYRsXr/xexn64NpU13P06jc/L5TgiJXOgrbEg==}
    peerDependencies:
      '@babel/core': ^7.4.0 || ^8.0.0-0 <8.0.0

  bail@2.0.2:
    resolution: {integrity: sha512-0xO6mYd7JB2YesxDKplafRpsiOzPt9V02ddPCLbY1xYGPOX24NTyN50qnUxgCPcSoYMhKpAuBTjQoRZCAkUDRw==}

  balanced-match@1.0.2:
    resolution: {integrity: sha512-3oSeUO0TMV67hN1AmbXsK4yaqU7tjiHlbxRDZOpH0KW9+CeX4bRAaX0Anxt0tx2MrpRpWwQaPwIlISEJhYU5Pw==}

  baseline-browser-mapping@2.9.14:
    resolution: {integrity: sha512-B0xUquLkiGLgHhpPBqvl7GWegWBUNuujQ6kXd/r1U38ElPT6Ok8KZ8e+FpUGEc2ZoRQUzq/aUnaKFc/svWUGSg==}
    hasBin: true

  batch@0.6.1:
    resolution: {integrity: sha512-x+VAiMRL6UPkx+kudNvxTl6hB2XNNCG2r+7wixVfIYwu/2HKRXimwQyaumLjMveWvT2Hkd/cAJw+QBMfJ/EKVw==}

  big.js@5.2.2:
    resolution: {integrity: sha512-vyL2OymJxmarO8gxMr0mhChsO9QGwhynfuu4+MHTAW6czfq9humCB7rKpUjDd9YUiDPU4mzpyupFSvOClAwbmQ==}

  binary-extensions@2.3.0:
    resolution: {integrity: sha512-Ceh+7ox5qe7LJuLHoY0feh3pHuUDHAcRUeyL2VYghZwfpkNIy/+8Ocg0a3UuSoYzavmylwuLWQOf3hl0jjMMIw==}
    engines: {node: '>=8'}

  body-parser@1.20.4:
    resolution: {integrity: sha512-ZTgYYLMOXY9qKU/57FAo8F+HA2dGX7bqGc71txDRC1rS4frdFI5R7NhluHxH6M0YItAP0sHB4uqAOcYKxO6uGA==}
    engines: {node: '>= 0.8', npm: 1.2.8000 || >= 1.4.16}

  bonjour-service@1.3.0:
    resolution: {integrity: sha512-3YuAUiSkWykd+2Azjgyxei8OWf8thdn8AITIog2M4UICzoqfjlqr64WIjEXZllf/W6vK1goqleSR6brGomxQqA==}

  boolbase@1.0.0:
    resolution: {integrity: sha512-JZOSA7Mo9sNGB8+UjSgzdLtokWAky1zbztM3WRLCbZ70/3cTANmQmOdR7y2g+J0e2WXywy1yS468tY+IruqEww==}

  boxen@6.2.1:
    resolution: {integrity: sha512-H4PEsJXfFI/Pt8sjDWbHlQPx4zL/bvSQjcilJmaulGt5mLDorHOHpmdXAJcBcmru7PhYSp/cDMWRko4ZUMFkSw==}
    engines: {node: ^12.20.0 || ^14.13.1 || >=16.0.0}

  boxen@7.1.1:
    resolution: {integrity: sha512-2hCgjEmP8YLWQ130n2FerGv7rYpfBmnmp9Uy2Le1vge6X3gZIfSmEzP5QTDElFxcvVcXlEn8Aq6MU/PZygIOog==}
    engines: {node: '>=14.16'}

  brace-expansion@1.1.12:
    resolution: {integrity: sha512-9T9UjW3r0UW5c1Q7GTwllptXwhvYmEzFhzMfZ9H7FQWt+uZePjZPjBP/W1ZEyZ1twGWom5/56TF4lPcqjnDHcg==}

  brace-expansion@2.0.2:
    resolution: {integrity: sha512-Jt0vHyM+jmUBqojB7E1NIYadt0vI0Qxjxd2TErW94wDz+E2LAm5vKMXXwg6ZZBTHPuUlDgQHKXvjGBdfcF1ZDQ==}

  braces@3.0.3:
    resolution: {integrity: sha512-yQbXgO/OSZVD2IsiLlro+7Hf6Q18EJrKSEsdoMzKePKXct3gvD8oLcOQdIzGupr5Fj+EDe8gO/lxc1BzfMpxvA==}
    engines: {node: '>=8'}

  browserslist@4.28.1:
    resolution: {integrity: sha512-ZC5Bd0LgJXgwGqUknZY/vkUQ04r8NXnJZ3yYi4vDmSiZmC/pdSN0NbNRPxZpbtO4uAfDUAFffO8IZoM3Gj8IkA==}
    engines: {node: ^6 || ^7 || ^8 || ^9 || ^10 || ^11 || ^12 || >=13.7}
    hasBin: true

  buffer-from@1.1.2:
    resolution: {integrity: sha512-E+XQCRwSbaaiChtv6k6Dwgc+bx+Bs6vuKJHHl5kox/BaKbhiXzqQOwK4cO22yElGp2OCmjwVhT3HmxgyPGnJfQ==}

  bundle-name@4.1.0:
    resolution: {integrity: sha512-tjwM5exMg6BGRI+kNmTntNsvdZS1X8BFYS6tnJ2hdH0kVxM6/eVZ2xy+FqStSWvYmtfFMDLIxurorHwDKfDz5Q==}
    engines: {node: '>=18'}

  bytes@3.0.0:
    resolution: {integrity: sha512-pMhOfFDPiv9t5jjIXkHosWmkSyQbvsgEVNkz0ERHbuLh2T/7j4Mqqpz523Fe8MVY89KC6Sh/QfS2sM+SjgFDcw==}
    engines: {node: '>= 0.8'}

  bytes@3.1.2:
    resolution: {integrity: sha512-/Nf7TyzTx6S3yRJObOAV7956r8cr2+Oj8AC5dt8wSP3BQAoeX58NoHyCU8P8zGkNXStjTSi6fzO6F0pBdcYbEg==}
    engines: {node: '>= 0.8'}

  bytestreamjs@2.0.1:
    resolution: {integrity: sha512-U1Z/ob71V/bXfVABvNr/Kumf5VyeQRBEm6Txb0PQ6S7V5GpBM3w4Cbqz/xPDicR5tN0uvDifng8C+5qECeGwyQ==}
    engines: {node: '>=6.0.0'}

  cacheable-lookup@7.0.0:
    resolution: {integrity: sha512-+qJyx4xiKra8mZrcwhjMRMUhD5NR1R8esPkzIYxX96JiecFoxAXFuz/GpR3+ev4PE1WamHip78wV0vcmPQtp8w==}
    engines: {node: '>=14.16'}

  cacheable-request@10.2.14:
    resolution: {integrity: sha512-zkDT5WAF4hSSoUgyfg5tFIxz8XQK+25W/TLVojJTMKBaxevLBBtLxgqguAuVQB8PVW79FVjHcU+GJ9tVbDZ9mQ==}
    engines: {node: '>=14.16'}

  call-bind-apply-helpers@1.0.2:
    resolution: {integrity: sha512-Sp1ablJ0ivDkSzjcaJdxEunN5/XvksFJ2sMBFfq6x0ryhQV/2b/KwFe21cMpmHtPOSij8K99/wSfoEuTObmuMQ==}
    engines: {node: '>= 0.4'}

  call-bind@1.0.8:
    resolution: {integrity: sha512-oKlSFMcMwpUg2ednkhQ454wfWiU/ul3CkJe/PEHcTKuiX6RpbehUiFMXu13HalGZxfUwCQzZG747YXBn1im9ww==}
    engines: {node: '>= 0.4'}

  call-bound@1.0.4:
    resolution: {integrity: sha512-+ys997U96po4Kx/ABpBCqhA9EuxJaQWDQg7295H4hBphv3IZg0boBKuwYpt4YXp6MZ5AmZQnU/tyMTlRpaSejg==}
    engines: {node: '>= 0.4'}

  callsites@3.1.0:
    resolution: {integrity: sha512-P8BjAsXvZS+VIDUI11hHCQEv74YT67YUi5JJFNWIqL235sBmjX4+qx9Muvls5ivyNENctx46xQLQ3aTuE7ssaQ==}
    engines: {node: '>=6'}

  camel-case@4.1.2:
    resolution: {integrity: sha512-gxGWBrTT1JuMx6R+o5PTXMmUnhnVzLQ9SNutD4YqKtI6ap897t3tKECYla6gCWEkplXnlNybEkZg9GEGxKFCgw==}

  camelcase@6.3.0:
    resolution: {integrity: sha512-Gmy6FhYlCY7uOElZUSbxo2UCDH8owEk996gkbrpsgGtrJLM3J7jGxl9Ic7Qwwj4ivOE5AWZWRMecDdF7hqGjFA==}
    engines: {node: '>=10'}

  camelcase@7.0.1:
    resolution: {integrity: sha512-xlx1yCK2Oc1APsPXDL2LdlNP6+uu8OCDdhOBSVT279M/S+y75O30C2VuD8T2ogdePBBl7PfPF4504tnLgX3zfw==}
    engines: {node: '>=14.16'}

  caniuse-api@3.0.0:
    resolution: {integrity: sha512-bsTwuIg/BZZK/vreVTYYbSWoe2F+71P7K5QGEX+pT250DZbfU1MQ5prOKpPR+LL6uWKK3KMwMCAS74QB3Um1uw==}

  caniuse-lite@1.0.30001764:
    resolution: {integrity: sha512-9JGuzl2M+vPL+pz70gtMF9sHdMFbY9FJaQBi186cHKH3pSzDvzoUJUPV6fqiKIMyXbud9ZLg4F3Yza1vJ1+93g==}

  ccount@2.0.1:
    resolution: {integrity: sha512-eyrF0jiFpY+3drT6383f1qhkbGsLSifNAjA61IUjZjmLCWjItY6LB9ft9YhoDgwfmclB2zhu51Lc7+95b8NRAg==}

  chalk@4.1.2:
    resolution: {integrity: sha512-oKnbhFyRIXpUuez8iBMmyEa4nbj4IOQyuhc/wy9kY7/WVPcwIO9VA668Pu8RkO7+0G76SLROeyw9CpQ061i4mA==}
    engines: {node: '>=10'}

  chalk@5.6.2:
    resolution: {integrity: sha512-7NzBL0rN6fMUW+f7A6Io4h40qQlG+xGmtMxfbnH/K7TAtt8JQWVQK+6g0UXKMeVJoyV5EkkNsErQ8pVD3bLHbA==}
    engines: {node: ^12.17.0 || ^14.13 || >=16.0.0}

  char-regex@1.0.2:
    resolution: {integrity: sha512-kWWXztvZ5SBQV+eRgKFeh8q5sLuZY2+8WUIzlxWVTg+oGwY14qylx1KbKzHd8P6ZYkAg0xyIDU9JMHhyJMZ1jw==}
    engines: {node: '>=10'}

  character-entities-html4@2.1.0:
    resolution: {integrity: sha512-1v7fgQRj6hnSwFpq1Eu0ynr/CDEw0rXo2B61qXrLNdHZmPKgb7fqS1a2JwF0rISo9q77jDI8VMEHoApn8qDoZA==}

  character-entities-legacy@3.0.0:
    resolution: {integrity: sha512-RpPp0asT/6ufRm//AJVwpViZbGM/MkjQFxJccQRHmISF/22NBtsHqAWmL+/pmkPWoIUJdWyeVleTl1wydHATVQ==}

  character-entities@2.0.2:
    resolution: {integrity: sha512-shx7oQ0Awen/BRIdkjkvz54PnEEI/EjwXDSIZp86/KKdbafHh1Df/RYGBhn4hbe2+uKC9FnT5UCEdyPz3ai9hQ==}

  character-reference-invalid@2.0.1:
    resolution: {integrity: sha512-iBZ4F4wRbyORVsu0jPV7gXkOsGYjGHPmAyv+HiHG8gi5PtC9KI2j1+v8/tlibRvjoWX027ypmG/n0HtO5t7unw==}

  cheerio-select@2.1.0:
    resolution: {integrity: sha512-9v9kG0LvzrlcungtnJtpGNxY+fzECQKhK4EGJX2vByejiMX84MFNQw4UxPJl3bFbTMw+Dfs37XaIkCwTZfLh4g==}

  cheerio@1.0.0-rc.12:
    resolution: {integrity: sha512-VqR8m68vM46BNnuZ5NtnGBKIE/DfN0cRIzg9n40EIq9NOv90ayxLBXA8fXC5gquFRGJSTRqBq25Jt2ECLR431Q==}
    engines: {node: '>= 6'}

  chevrotain-allstar@0.3.1:
    resolution: {integrity: sha512-b7g+y9A0v4mxCW1qUhf3BSVPg+/NvGErk/dOkrDaHA0nQIQGAtrOjlX//9OQtRlSCy+x9rfB5N8yC71lH1nvMw==}
    peerDependencies:
      chevrotain: ^11.0.0

  chevrotain@11.0.3:
    resolution: {integrity: sha512-ci2iJH6LeIkvP9eJW6gpueU8cnZhv85ELY8w8WiFtNjMHA5ad6pQLaJo9mEly/9qUyCpvqX8/POVUTf18/HFdw==}

  chokidar@3.6.0:
    resolution: {integrity: sha512-7VT13fmjotKpGipCW9JEQAusEPE+Ei8nl6/g4FBAmIm0GOOLMua9NDDo/DWp0ZAxCr3cPq5ZpBqmPAQgDda2Pw==}
    engines: {node: '>= 8.10.0'}

  chrome-trace-event@1.0.4:
    resolution: {integrity: sha512-rNjApaLzuwaOTjCiT8lSDdGN1APCiqkChLMJxJPWLunPAt5fy8xgU9/jNOchV84wfIxrA0lRQB7oCT8jrn/wrQ==}
    engines: {node: '>=6.0'}

  ci-info@3.9.0:
    resolution: {integrity: sha512-NIxF55hv4nSqQswkAeiOi1r83xy8JldOFDTWiug55KBu9Jnblncd2U6ViHmYgHf01TPZS77NJBhBMKdWj9HQMQ==}
    engines: {node: '>=8'}

  clean-css@5.3.3:
    resolution: {integrity: sha512-D5J+kHaVb/wKSFcyyV75uCn8fiY4sV38XJoe4CUyGQ+mOU/fMVYUdH1hJC+CJQ5uY3EnW27SbJYS4X8BiLrAFg==}
    engines: {node: '>= 10.0'}

  clean-stack@2.2.0:
    resolution: {integrity: sha512-4diC9HaTE+KRAMWhDhrGOECgWZxoevMc5TlkObMqNSsVU62PYzXZ/SMTjzyGAFF1YusgxGcSWTEXBhp0CPwQ1A==}
    engines: {node: '>=6'}

  cli-boxes@3.0.0:
    resolution: {integrity: sha512-/lzGpEWL/8PfI0BmBOPRwp0c/wFNX1RdUML3jK/RcSBA9T8mZDdQpqYBKtCFTOfQbwPqWEOpjqW+Fnayc0969g==}
    engines: {node: '>=10'}

  cli-cursor@5.0.0:
    resolution: {integrity: sha512-aCj4O5wKyszjMmDT4tZj93kxyydN/K5zPWSCe6/0AV/AA1pqe5ZBIw0a2ZfPQV7lL5/yb5HsUreJ6UFAF1tEQw==}
    engines: {node: '>=18'}

  cli-table3@0.6.5:
    resolution: {integrity: sha512-+W/5efTR7y5HRD7gACw9yQjqMVvEMLBHmboM/kPWam+H+Hmyrgjh6YncVKK122YZkXrLudzTuAukUw9FnMf7IQ==}
    engines: {node: 10.* || >= 12.*}

  cli-truncate@5.1.1:
    resolution: {integrity: sha512-SroPvNHxUnk+vIW/dOSfNqdy1sPEFkrTk6TUtqLCnBlo3N7TNYYkzzN7uSD6+jVjrdO4+p8nH7JzH6cIvUem6A==}
    engines: {node: '>=20'}

  clone-deep@4.0.1:
    resolution: {integrity: sha512-neHB9xuzh/wk0dIHweyAXv2aPGZIVk3pLMe+/RNzINf17fe0OG96QroktYAUm7SM1PBnzTabaLboqqxDyMU+SQ==}
    engines: {node: '>=6'}

  clsx@2.1.1:
    resolution: {integrity: sha512-eYm0QWBtUrBWZWG0d386OGAw16Z995PiOVo2B7bjWSbHedGl5e0ZWaq65kOGgUSNesEIDkB9ISbTg/JK9dhCZA==}
    engines: {node: '>=6'}

  collapse-white-space@2.1.0:
    resolution: {integrity: sha512-loKTxY1zCOuG4j9f6EPnuyyYkf58RnhhWTvRoZEokgB+WbdXehfjFviyOVYkqzEWz1Q5kRiZdBYS5SwxbQYwzw==}

  color-convert@2.0.1:
    resolution: {integrity: sha512-RRECPsj7iu/xb5oKYcsFHSppFNnsj/52OVTRKb4zP5onXwVF3zVmmToNcOfGC+CRDpfK/U584fMg38ZHCaElKQ==}
    engines: {node: '>=7.0.0'}

  color-name@1.1.4:
    resolution: {integrity: sha512-dOy+3AuW3a2wNbZHIuMZpTcgjGuLU/uBL/ubcZF9OXbDo8ff4O8yVp5Bf0efS8uEoYo5q4Fx7dY9OgQGXgAsQA==}

  colord@2.9.3:
    resolution: {integrity: sha512-jeC1axXpnb0/2nn/Y1LPuLdgXBLH7aDcHu4KEKfqw3CUhX7ZpfBSlPKyqXE6btIgEzfWtrX3/tyBCaCvXvMkOw==}

  colorette@2.0.20:
    resolution: {integrity: sha512-IfEDxwoWIjkeXL1eXcDiow4UbKjhLdq6/EuSVR9GMN7KVH3r9gQ83e73hsz1Nd1T3ijd5xv1wcWRYO+D6kCI2w==}

  combine-promises@1.2.0:
    resolution: {integrity: sha512-VcQB1ziGD0NXrhKxiwyNbCDmRzs/OShMs2GqW2DlU2A/Sd0nQxE1oWDAE5O0ygSx5mgQOn9eIFh7yKPgFRVkPQ==}
    engines: {node: '>=10'}

  comma-separated-tokens@2.0.3:
    resolution: {integrity: sha512-Fu4hJdvzeylCfQPp9SGWidpzrMs7tTrlu6Vb8XGaRGck8QSNZJJp538Wrb60Lax4fPwR64ViY468OIUTbRlGZg==}

  commander@10.0.1:
    resolution: {integrity: sha512-y4Mg2tXshplEbSGzx7amzPwKKOCGuoSRP/CjEdwwk0FOGlUbq6lKuoyDZTNZkmxHdJtp54hdfY/JUrdL7Xfdug==}
    engines: {node: '>=14'}

  commander@14.0.2:
    resolution: {integrity: sha512-TywoWNNRbhoD0BXs1P3ZEScW8W5iKrnbithIl0YH+uCmBd0QpPOA8yc82DS3BIE5Ma6FnBVUsJ7wVUDz4dvOWQ==}
    engines: {node: '>=20'}

  commander@2.20.3:
    resolution: {integrity: sha512-GpVkmM8vF2vQUkj2LvZmD35JxeJOLCwJ9cUkugyk2nuhbv3+mJvpLYYt+0+USMxE+oj+ey/lJEnhZw75x/OMcQ==}

  commander@5.1.0:
    resolution: {integrity: sha512-P0CysNDQ7rtVw4QIQtm+MRxV66vKFSvlsQvGYXZWR3qFU0jlMKHZZZgw8e+8DSah4UDKMqnknRDQz+xuQXQ/Zg==}
    engines: {node: '>= 6'}

  commander@7.2.0:
    resolution: {integrity: sha512-QrWXB+ZQSVPmIWIhtEO9H+gwHaMGYiF5ChvoJ+K9ZGHG/sVsa6yiesAD1GC/x46sET00Xlwo1u49RVVVzvcSkw==}
    engines: {node: '>= 10'}

  commander@8.3.0:
    resolution: {integrity: sha512-OkTL9umf+He2DZkUq8f8J9of7yL6RJKI24dVITBmNfZBmri9zYZQrKkuXiKhyfPSu8tUhnVBB1iKXevvnlR4Ww==}
    engines: {node: '>= 12'}

  common-path-prefix@3.0.0:
    resolution: {integrity: sha512-QE33hToZseCH3jS0qN96O/bSh3kaw/h+Tq7ngyY9eWDUnTlTNUyqfqvCXioLe5Na5jFsL78ra/wuBU4iuEgd4w==}

  compressible@2.0.18:
    resolution: {integrity: sha512-AF3r7P5dWxL8MxyITRMlORQNaOA2IkAFaTr4k7BUumjPtRpGDTZpl0Pb1XCO6JeDCBdp126Cgs9sMxqSjgYyRg==}
    engines: {node: '>= 0.6'}

  compression@1.8.1:
    resolution: {integrity: sha512-9mAqGPHLakhCLeNyxPkK4xVo746zQ/czLH1Ky+vkitMnWfWZps8r0qXuwhwizagCRttsL4lfG4pIOvaWLpAP0w==}
    engines: {node: '>= 0.8.0'}

  concat-map@0.0.1:
    resolution: {integrity: sha512-/Srv4dswyQNBfohGpz9o6Yb3Gz3SrUDqBH5rTuhGR7ahtlbYKnVxw2bCFMRljaA7EXHaXZ8wsHdodFvbkhKmqg==}

  confbox@0.1.8:
    resolution: {integrity: sha512-RMtmw0iFkeR4YV+fUOSucriAQNb9g8zFR52MWCtl+cCZOFRNL6zeB395vPzFhEjjn4fMxXudmELnl/KF/WrK6w==}

  config-chain@1.1.13:
    resolution: {integrity: sha512-qj+f8APARXHrM0hraqXYb2/bOVSV4PvJQlNZ/DVj0QrmNM2q2euizkeuVckQ57J+W0mRH6Hvi+k50M4Jul2VRQ==}

  configstore@6.0.0:
    resolution: {integrity: sha512-cD31W1v3GqUlQvbBCGcXmd2Nj9SvLDOP1oQ0YFuLETufzSPaKp11rYBsSOm7rCsW3OnIRAFM3OxRhceaXNYHkA==}
    engines: {node: '>=12'}

  connect-history-api-fallback@2.0.0:
    resolution: {integrity: sha512-U73+6lQFmfiNPrYbXqr6kZ1i1wiRqXnp2nhMsINseWXO8lDau0LGEffJ8kQi4EjLZympVgRdvqjAgiZ1tgzDDA==}
    engines: {node: '>=0.8'}

  consola@3.4.2:
    resolution: {integrity: sha512-5IKcdX0nnYavi6G7TtOhwkYzyjfJlatbjMjuLSfE2kYT5pMDOilZ4OvMhi637CcDICTmz3wARPoyhqyX1Y+XvA==}
    engines: {node: ^14.18.0 || >=16.10.0}

  content-disposition@0.5.2:
    resolution: {integrity: sha512-kRGRZw3bLlFISDBgwTSA1TMBFN6J6GWDeubmDE3AF+3+yXL8hTWv8r5rkLbqYXY4RjPk/EzHnClI3zQf1cFmHA==}
    engines: {node: '>= 0.6'}

  content-disposition@0.5.4:
    resolution: {integrity: sha512-FveZTNuGw04cxlAiWbzi6zTAL/lhehaWbTtgluJh4/E95DqMwTmha3KZN1aAWA8cFIhHzMZUvLevkw5Rqk+tSQ==}
    engines: {node: '>= 0.6'}

  content-type@1.0.5:
    resolution: {integrity: sha512-nTjqfcBFEipKdXCv4YDQWCfmcLZKm81ldF0pAopTvyrFGVbcR6P/VAAd5G7N+0tTr8QqiU0tFadD6FK4NtJwOA==}
    engines: {node: '>= 0.6'}

  convert-source-map@2.0.0:
    resolution: {integrity: sha512-Kvp459HrV2FEJ1CAsi1Ku+MY3kasH19TFykTz2xWmMeq6bk2NU3XXvfJ+Q61m0xktWwt+1HSYf3JZsTms3aRJg==}

  cookie-signature@1.0.7:
    resolution: {integrity: sha512-NXdYc3dLr47pBkpUCHtKSwIOQXLVn8dZEuywboCOJY/osA0wFSLlSawr3KN8qXJEyX66FcONTH8EIlVuK0yyFA==}

  cookie@0.7.2:
    resolution: {integrity: sha512-yki5XnKuf750l50uGTllt6kKILY4nQ1eNIQatoXEByZ5dWgnKqbnqmTrBE5B4N7lrMJKQ2ytWMiTO2o0v6Ew/w==}
    engines: {node: '>= 0.6'}

  copy-webpack-plugin@11.0.0:
    resolution: {integrity: sha512-fX2MWpamkW0hZxMEg0+mYnA40LTosOSa5TqZ9GYIBzyJa9C3QUaMPSE2xAi/buNr8u89SfD9wHSQVBzrRa/SOQ==}
    engines: {node: '>= 14.15.0'}
    peerDependencies:
      webpack: ^5.1.0

  core-js-compat@3.47.0:
    resolution: {integrity: sha512-IGfuznZ/n7Kp9+nypamBhvwdwLsW6KC8IOaURw2doAK5e98AG3acVLdh0woOnEqCfUtS+Vu882JE4k/DAm3ItQ==}

  core-js-pure@3.47.0:
    resolution: {integrity: sha512-BcxeDbzUrRnXGYIVAGFtcGQVNpFcUhVjr6W7F8XktvQW2iJP9e66GP6xdKotCRFlrxBvNIBrhwKteRXqMV86Nw==}

  core-js@3.47.0:
    resolution: {integrity: sha512-c3Q2VVkGAUyupsjRnaNX6u8Dq2vAdzm9iuPj5FW0fRxzlxgq9Q39MDq10IvmQSpLgHQNyQzQmOo6bgGHmH3NNg==}

  core-util-is@1.0.3:
    resolution: {integrity: sha512-ZQBvi1DcpJ4GDqanjucZ2Hj3wEO5pZDS89BWbkcrvdxksJorwUDDZamX9ldFkp9aw2lmBDLgkObEA4DWNJ9FYQ==}

  cose-base@1.0.3:
    resolution: {integrity: sha512-s9whTXInMSgAp/NVXVNuVxVKzGH2qck3aQlVHxDCdAEPgtMKwc4Wq6/QKhgdEdgbLSi9rBTAcPoRa6JpiG4ksg==}

  cose-base@2.2.0:
    resolution: {integrity: sha512-AzlgcsCbUMymkADOJtQm3wO9S3ltPfYOFD5033keQn9NJzIbtnZj+UdBJe7DYml/8TdbtHJW3j58SOnKhWY/5g==}

  cosmiconfig@8.3.6:
    resolution: {integrity: sha512-kcZ6+W5QzcJ3P1Mt+83OUv/oHFqZHIx8DuxG6eZ5RGMERoLqp4BuGjhHLYGK+Kf5XVkQvqBSmAy/nGWN3qDgEA==}
    engines: {node: '>=14'}
    peerDependencies:
      typescript: '>=4.9.5'
    peerDependenciesMeta:
      typescript:
        optional: true

  cross-spawn@7.0.6:
    resolution: {integrity: sha512-uV2QOWP2nWzsy2aMp8aRibhi9dlzF5Hgh5SHaB9OiTGEyDTiJJyx0uy51QXdyWbtAHNua4XJzUKca3OzKUd3vA==}
    engines: {node: '>= 8'}

  crypto-random-string@4.0.0:
    resolution: {integrity: sha512-x8dy3RnvYdlUcPOjkEHqozhiwzKNSq7GcPuXFbnyMOCHxX8V3OgIg/pYuabl2sbUPfIJaeAQB7PMOK8DFIdoRA==}
    engines: {node: '>=12'}

  css-blank-pseudo@7.0.1:
    resolution: {integrity: sha512-jf+twWGDf6LDoXDUode+nc7ZlrqfaNphrBIBrcmeP3D8yw1uPaix1gCC8LUQUGQ6CycuK2opkbFFWFuq/a94ag==}
    engines: {node: '>=18'}
    peerDependencies:
      postcss: ^8.4

  css-declaration-sorter@7.3.1:
    resolution: {integrity: sha512-gz6x+KkgNCjxq3Var03pRYLhyNfwhkKF1g/yoLgDNtFvVu0/fOLV9C8fFEZRjACp/XQLumjAYo7JVjzH3wLbxA==}
    engines: {node: ^14 || ^16 || >=18}
    peerDependencies:
      postcss: ^8.0.9

  css-has-pseudo@7.0.3:
    resolution: {integrity: sha512-oG+vKuGyqe/xvEMoxAQrhi7uY16deJR3i7wwhBerVrGQKSqUC5GiOVxTpM9F9B9hw0J+eKeOWLH7E9gZ1Dr5rA==}
    engines: {node: '>=18'}
    peerDependencies:
      postcss: ^8.4

  css-loader@6.11.0:
    resolution: {integrity: sha512-CTJ+AEQJjq5NzLga5pE39qdiSV56F8ywCIsqNIRF0r7BDgWsN25aazToqAFg7ZrtA/U016xudB3ffgweORxX7g==}
    engines: {node: '>= 12.13.0'}
    peerDependencies:
      '@rspack/core': 0.x || 1.x
      webpack: ^5.0.0
    peerDependenciesMeta:
      '@rspack/core':
        optional: true
      webpack:
        optional: true

  css-minimizer-webpack-plugin@5.0.1:
    resolution: {integrity: sha512-3caImjKFQkS+ws1TGcFn0V1HyDJFq1Euy589JlD6/3rV2kj+w7r5G9WDMgSHvpvXHNZ2calVypZWuEDQd9wfLg==}
    engines: {node: '>= 14.15.0'}
    peerDependencies:
      '@parcel/css': '*'
      '@swc/css': '*'
      clean-css: '*'
      csso: '*'
      esbuild: '*'
      lightningcss: '*'
      webpack: ^5.0.0
    peerDependenciesMeta:
      '@parcel/css':
        optional: true
      '@swc/css':
        optional: true
      clean-css:
        optional: true
      csso:
        optional: true
      esbuild:
        optional: true
      lightningcss:
        optional: true

  css-prefers-color-scheme@10.0.0:
    resolution: {integrity: sha512-VCtXZAWivRglTZditUfB4StnsWr6YVZ2PRtuxQLKTNRdtAf8tpzaVPE9zXIF3VaSc7O70iK/j1+NXxyQCqdPjQ==}
    engines: {node: '>=18'}
    peerDependencies:
      postcss: ^8.4

  css-select@4.3.0:
    resolution: {integrity: sha512-wPpOYtnsVontu2mODhA19JrqWxNsfdatRKd64kmpRbQgh1KtItko5sTnEpPdpSaJszTOhEMlF/RPz28qj4HqhQ==}

  css-select@5.2.2:
    resolution: {integrity: sha512-TizTzUddG/xYLA3NXodFM0fSbNizXjOKhqiQQwvhlspadZokn1KDy0NZFS0wuEubIYAV5/c1/lAr0TaaFXEXzw==}

  css-tree@2.2.1:
    resolution: {integrity: sha512-OA0mILzGc1kCOCSJerOeqDxDQ4HOh+G8NbOJFOTgOCzpw7fCBubk0fEyxp8AgOL/jvLgYA/uV0cMbe43ElF1JA==}
    engines: {node: ^10 || ^12.20.0 || ^14.13.0 || >=15.0.0, npm: '>=7.0.0'}

  css-tree@2.3.1:
    resolution: {integrity: sha512-6Fv1DV/TYw//QF5IzQdqsNDjx/wc8TrMBZsqjL9eW01tWb7R7k/mq+/VXfJCl7SoD5emsJop9cOByJZfs8hYIw==}
    engines: {node: ^10 || ^12.20.0 || ^14.13.0 || >=15.0.0}

  css-what@6.2.2:
    resolution: {integrity: sha512-u/O3vwbptzhMs3L1fQE82ZSLHQQfto5gyZzwteVIEyeaY5Fc7R4dapF/BvRoSYFeqfBk4m0V1Vafq5Pjv25wvA==}
    engines: {node: '>= 6'}

  cssdb@8.6.0:
    resolution: {integrity: sha512-7ZrRi/Z3cRL1d5I8RuXEWAkRFP3J4GeQRiyVknI4KC70RAU8hT4LysUZDe0y+fYNOktCbxE8sOPUOhyR12UqGQ==}

  cssesc@3.0.0:
    resolution: {integrity: sha512-/Tb/JcjK111nNScGob5MNtsntNM1aCNUDipB/TkwZFhyDrrE47SOx/18wF2bbjgc3ZzCSKW1T5nt5EbFoAz/Vg==}
    engines: {node: '>=4'}
    hasBin: true

  cssnano-preset-advanced@6.1.2:
    resolution: {integrity: sha512-Nhao7eD8ph2DoHolEzQs5CfRpiEP0xa1HBdnFZ82kvqdmbwVBUr2r1QuQ4t1pi+D1ZpqpcO4T+wy/7RxzJ/WPQ==}
    engines: {node: ^14 || ^16 || >=18.0}
    peerDependencies:
      postcss: ^8.4.31

  cssnano-preset-default@6.1.2:
    resolution: {integrity: sha512-1C0C+eNaeN8OcHQa193aRgYexyJtU8XwbdieEjClw+J9d94E41LwT6ivKH0WT+fYwYWB0Zp3I3IZ7tI/BbUbrg==}
    engines: {node: ^14 || ^16 || >=18.0}
    peerDependencies:
      postcss: ^8.4.31

  cssnano-utils@4.0.2:
    resolution: {integrity: sha512-ZR1jHg+wZ8o4c3zqf1SIUSTIvm/9mU343FMR6Obe/unskbvpGhZOo1J6d/r8D1pzkRQYuwbcH3hToOuoA2G7oQ==}
    engines: {node: ^14 || ^16 || >=18.0}
    peerDependencies:
      postcss: ^8.4.31

  cssnano@6.1.2:
    resolution: {integrity: sha512-rYk5UeX7VAM/u0lNqewCdasdtPK81CgX8wJFLEIXHbV2oldWRgJAsZrdhRXkV1NJzA2g850KiFm9mMU2HxNxMA==}
    engines: {node: ^14 || ^16 || >=18.0}
    peerDependencies:
      postcss: ^8.4.31

  csso@5.0.5:
    resolution: {integrity: sha512-0LrrStPOdJj+SPCCrGhzryycLjwcgUSHBtxNA8aIDxf0GLsRh1cKYhB00Gd1lDOS4yGH69+SNn13+TWbVHETFQ==}
    engines: {node: ^10 || ^12.20.0 || ^14.13.0 || >=15.0.0, npm: '>=7.0.0'}

  csstype@3.2.3:
    resolution: {integrity: sha512-z1HGKcYy2xA8AGQfwrn0PAy+PB7X/GSj3UVJW9qKyn43xWa+gl5nXmU4qqLMRzWVLFC8KusUX8T/0kCiOYpAIQ==}

  cytoscape-cose-bilkent@4.1.0:
    resolution: {integrity: sha512-wgQlVIUJF13Quxiv5e1gstZ08rnZj2XaLHGoFMYXz7SkNfCDOOteKBE6SYRfA9WxxI/iBc3ajfDoc6hb/MRAHQ==}
    peerDependencies:
      cytoscape: ^3.2.0

  cytoscape-fcose@2.2.0:
    resolution: {integrity: sha512-ki1/VuRIHFCzxWNrsshHYPs6L7TvLu3DL+TyIGEsRcvVERmxokbf5Gdk7mFxZnTdiGtnA4cfSmjZJMviqSuZrQ==}
    peerDependencies:
      cytoscape: ^3.2.0

  cytoscape@3.33.1:
    resolution: {integrity: sha512-iJc4TwyANnOGR1OmWhsS9ayRS3s+XQ185FmuHObThD+5AeJCakAAbWv8KimMTt08xCCLNgneQwFp+JRJOr9qGQ==}
    engines: {node: '>=0.10'}

  d3-array@2.12.1:
    resolution: {integrity: sha512-B0ErZK/66mHtEsR1TkPEEkwdy+WDesimkM5gpZr5Dsg54BiTA5RXtYW5qTLIAcekaS9xfZrzBLF/OAkB3Qn1YQ==}

  d3-array@3.2.4:
    resolution: {integrity: sha512-tdQAmyA18i4J7wprpYq8ClcxZy3SC31QMeByyCFyRt7BVHdREQZ5lpzoe5mFEYZUWe+oq8HBvk9JjpibyEV4Jg==}
    engines: {node: '>=12'}

  d3-axis@3.0.0:
    resolution: {integrity: sha512-IH5tgjV4jE/GhHkRV0HiVYPDtvfjHQlQfJHs0usq7M30XcSBvOotpmH1IgkcXsO/5gEQZD43B//fc7SRT5S+xw==}
    engines: {node: '>=12'}
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
